umiahmed30/RuTrash/Data/paper/paper5.jpg

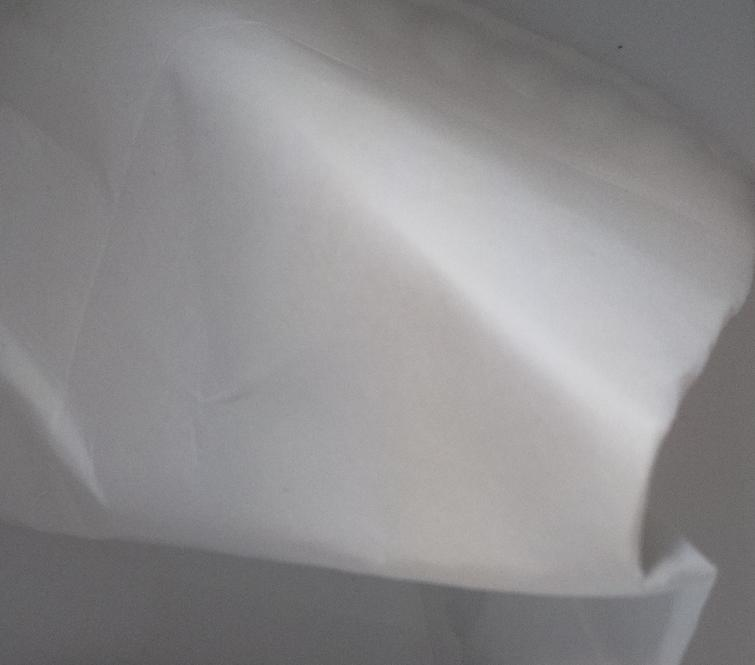
Data/paper/paper5.jpg
