umiahmed30/RuTrash/Data/Valid/paper/paper_new_14.jpg

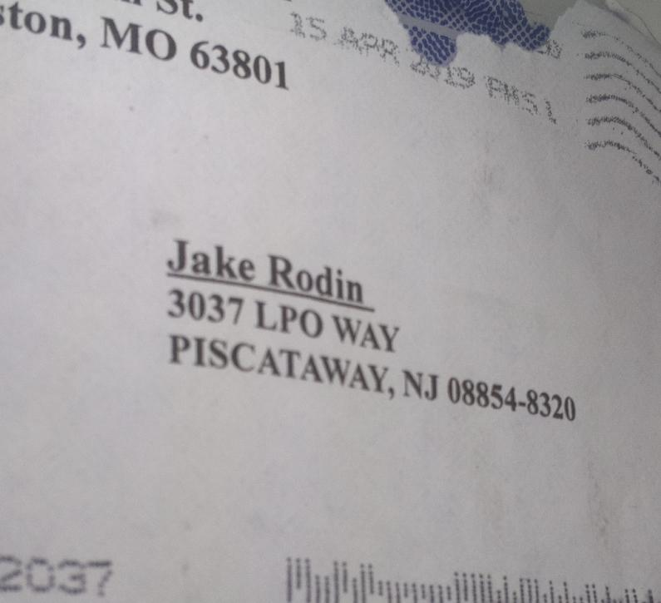
Data/Valid/paper/paper_new_14.jpg
