umiahmed30/RuTrash/Data/glass.jpg

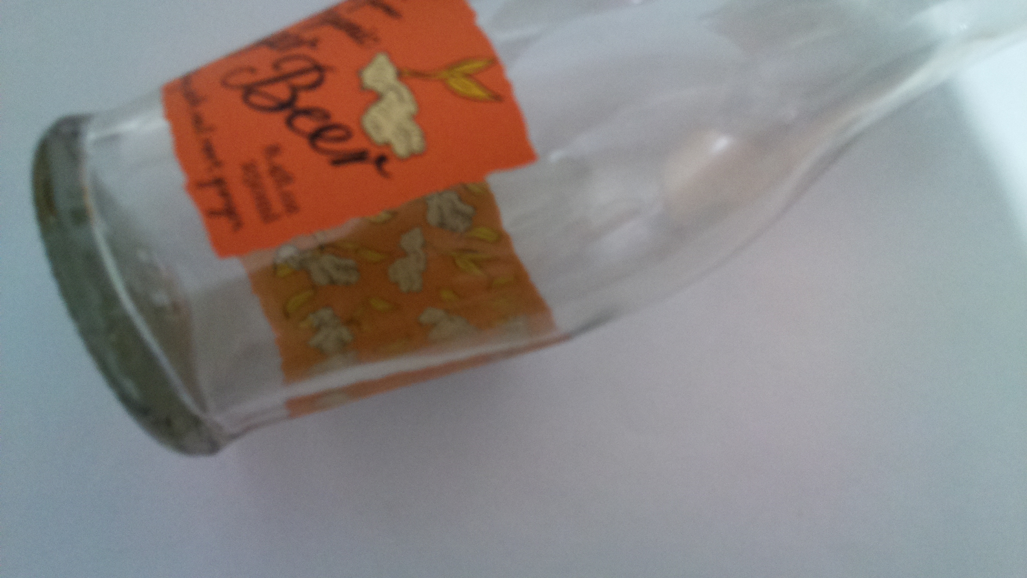
Data/glass.jpg
