umiahmed30/RuTrash/Data/glass/glass1.jpg

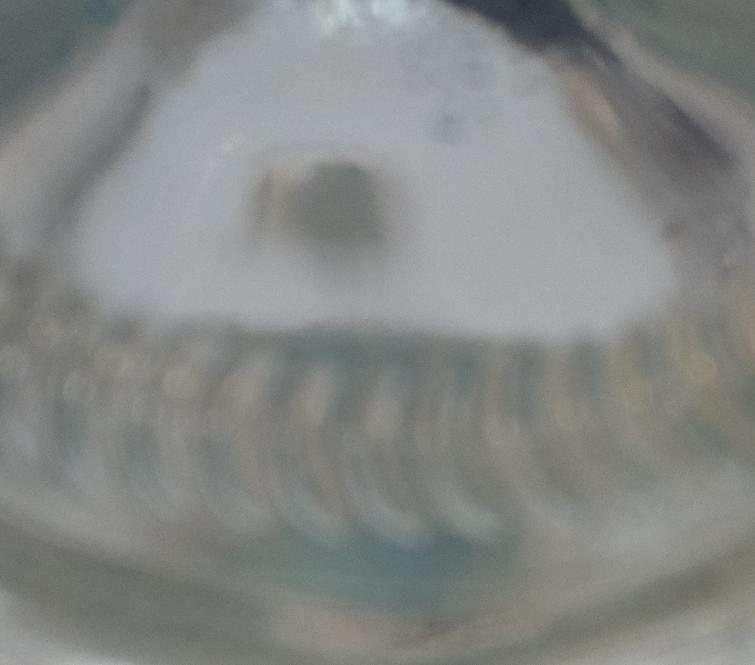
Data/glass/glass1.jpg
