umiahmed30/RuTrash/Data/glass/glass2.jpg

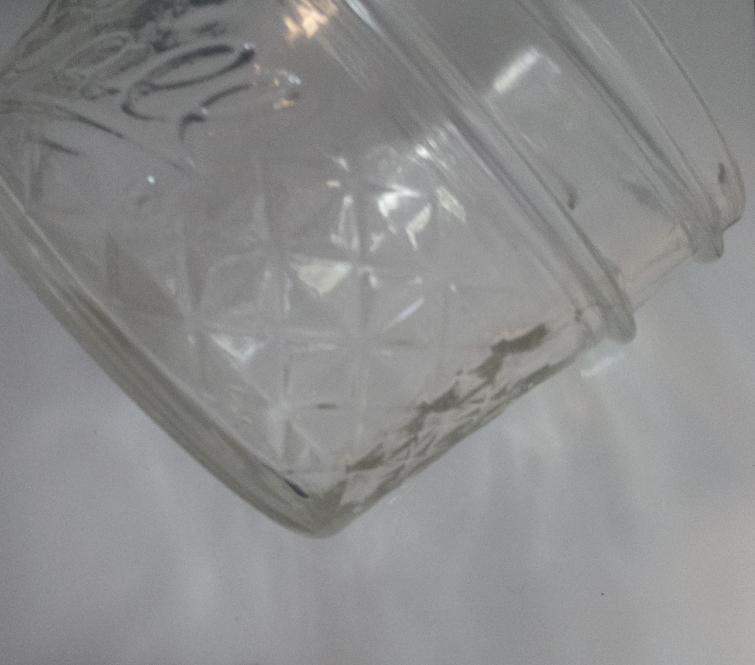
Data/glass/glass2.jpg
