umiahmed30/RuTrash/Data/glass/glass3.jpg

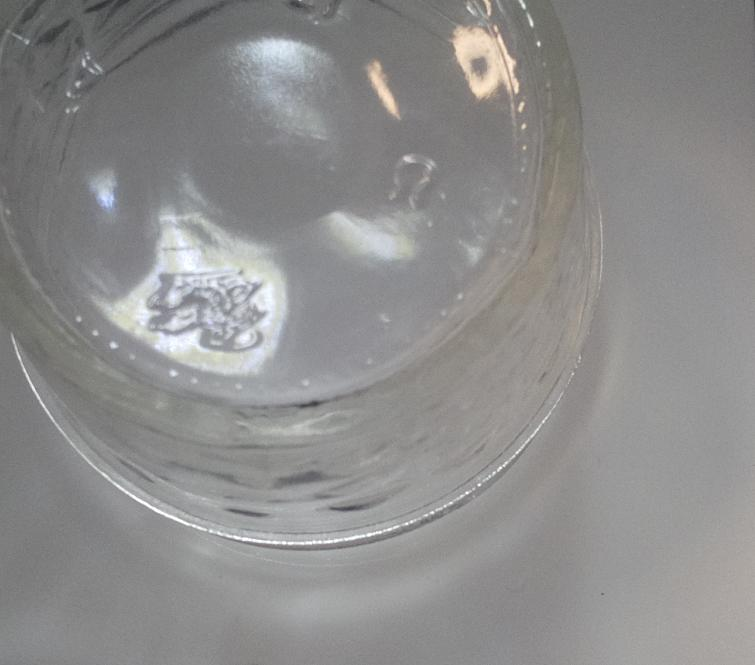
Data/glass/glass3.jpg
