umiahmed30/RuTrash/Data/glass/glass4.jpg

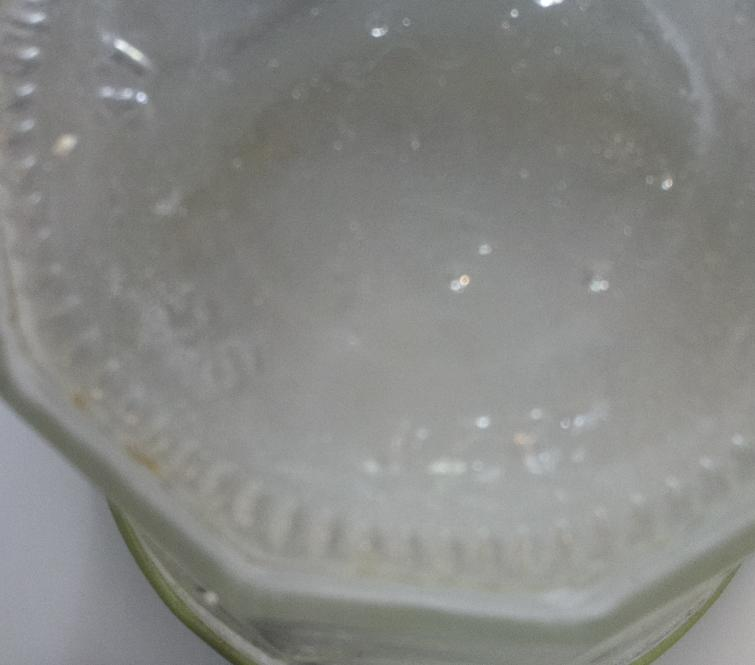
Data/glass/glass4.jpg
