umiahmed30/RuTrash/Data/metal2.jpg

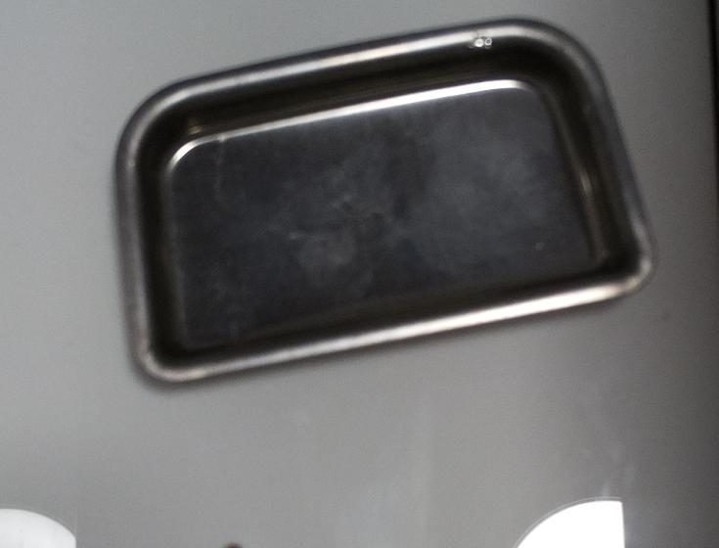
Data/metal2.jpg
