umiahmed30/RuTrash/Data/metal.jpg

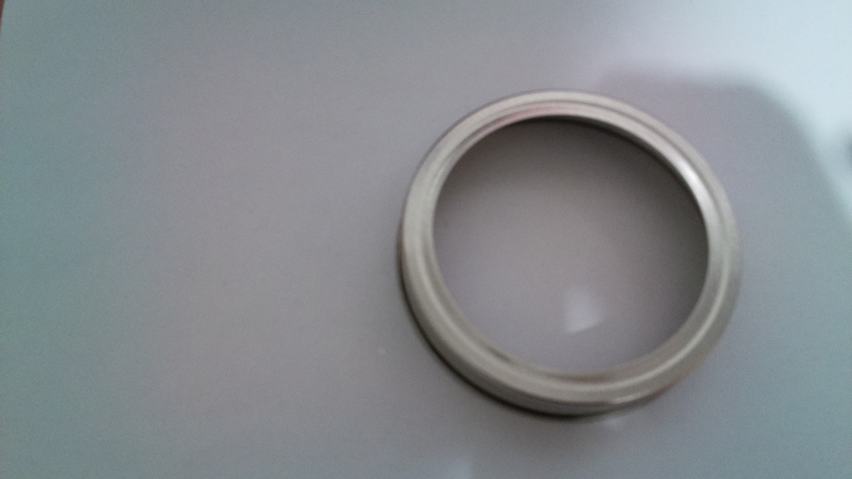
Data/metal.jpg
