umiahmed30/RuTrash/Data/metal/metal0.jpg

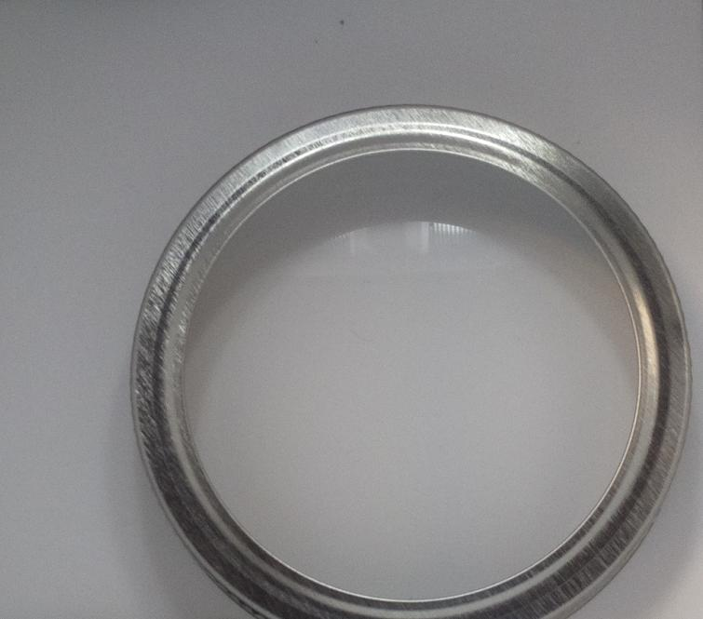
Data/metal/metal0.jpg
