umiahmed30/RuTrash/Data/metal/metal1.jpg

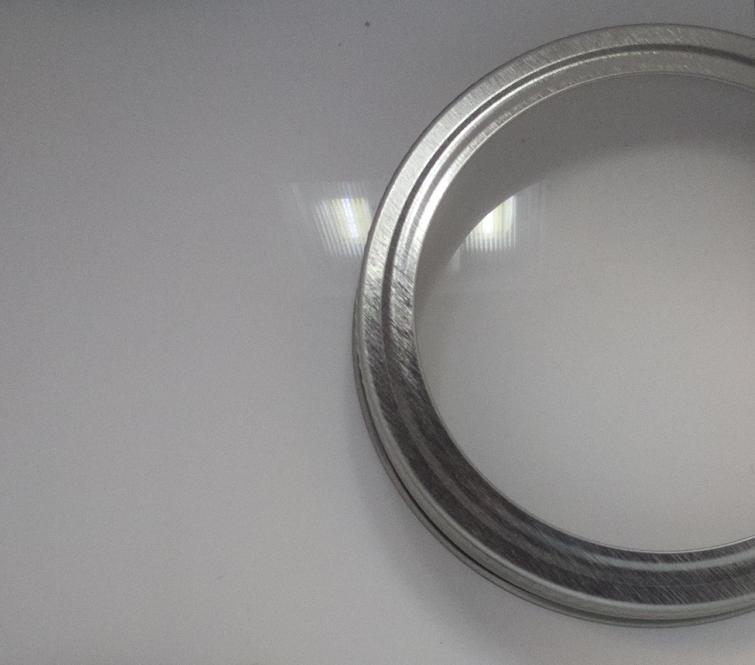
Data/metal/metal1.jpg
