umiahmed30/RuTrash/Data/metal/metal2.jpg

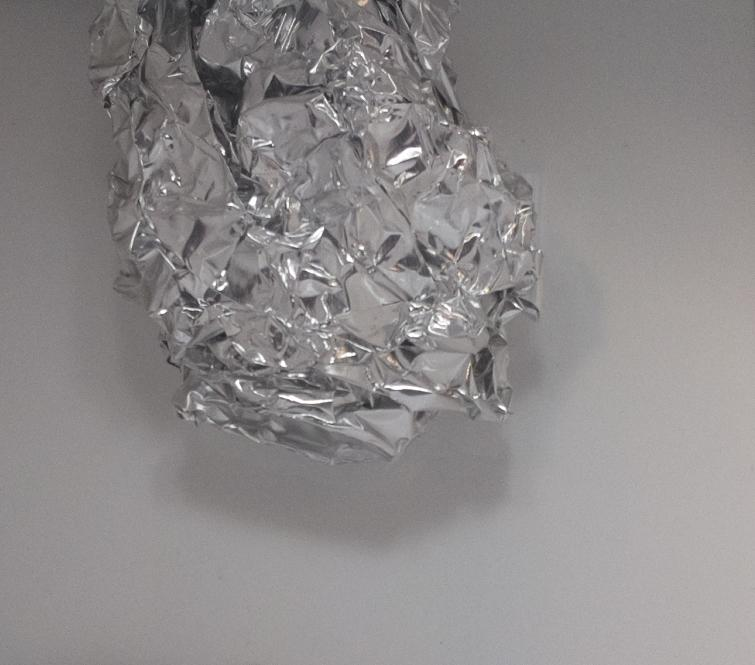
Data/metal/metal2.jpg
