umiahmed30/RuTrash/Data/metal/metal3.jpg

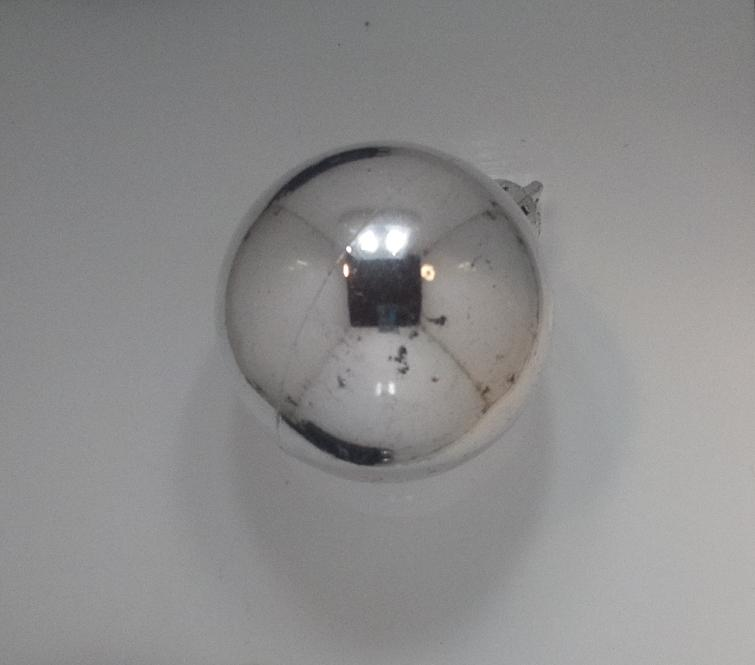
Data/metal/metal3.jpg
