umiahmed30/RuTrash/Data/metal/metal5.jpg

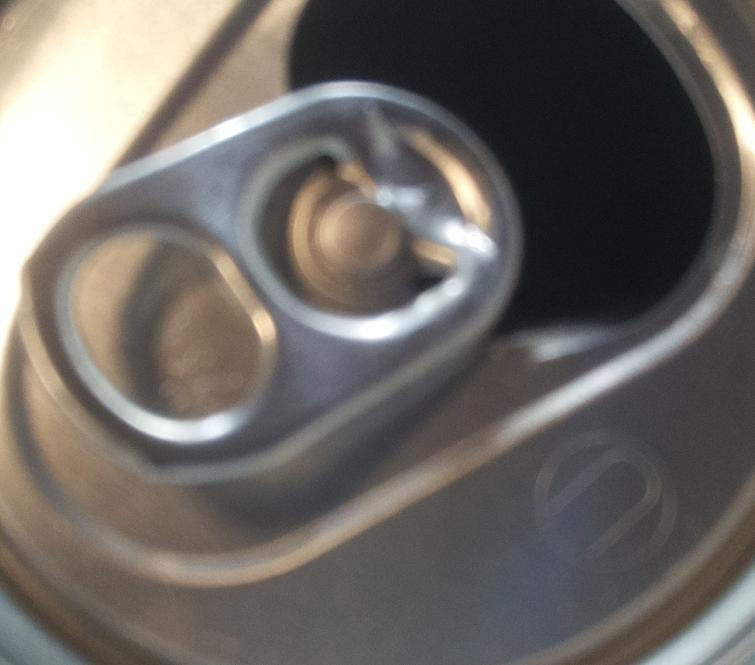
Data/metal/metal5.jpg
