umiahmed30/RuTrash/Data/metal/metal6.jpg

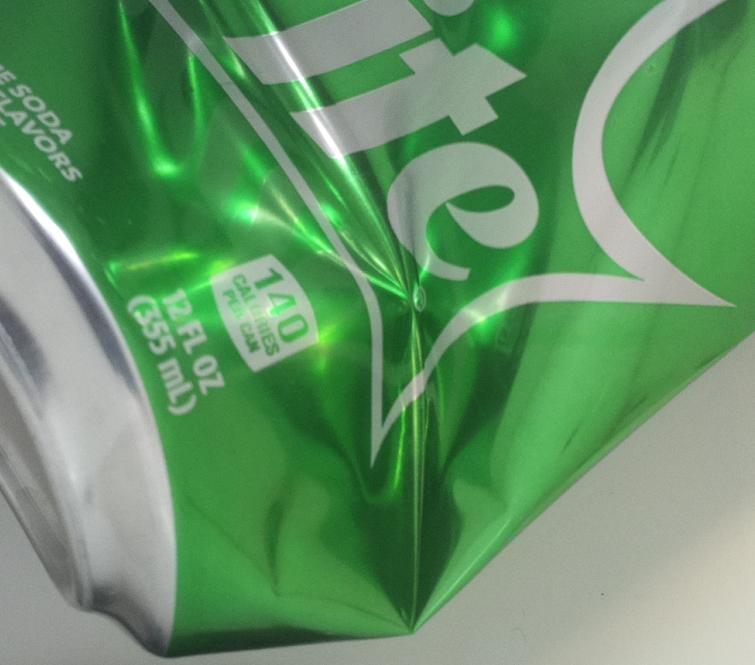
Data/metal/metal6.jpg
