umiahmed30/RuTrash/Data/metal/metal7.jpg

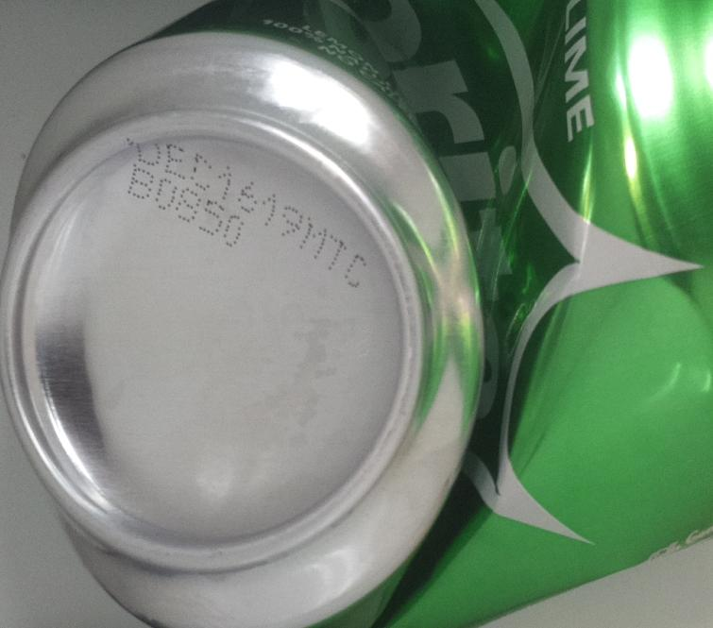
Data/metal/metal7.jpg
