umiahmed30/RuTrash/Data/metal/metal8.jpg

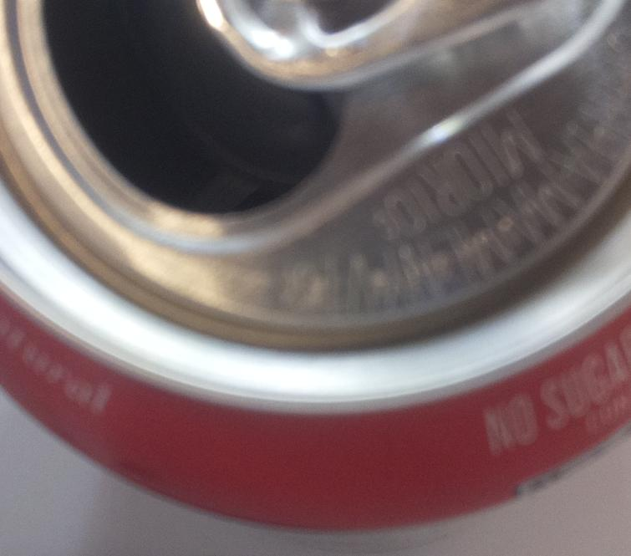
Data/metal/metal8.jpg
