umiahmed30/RuTrash/Data/metal/metal10.jpg

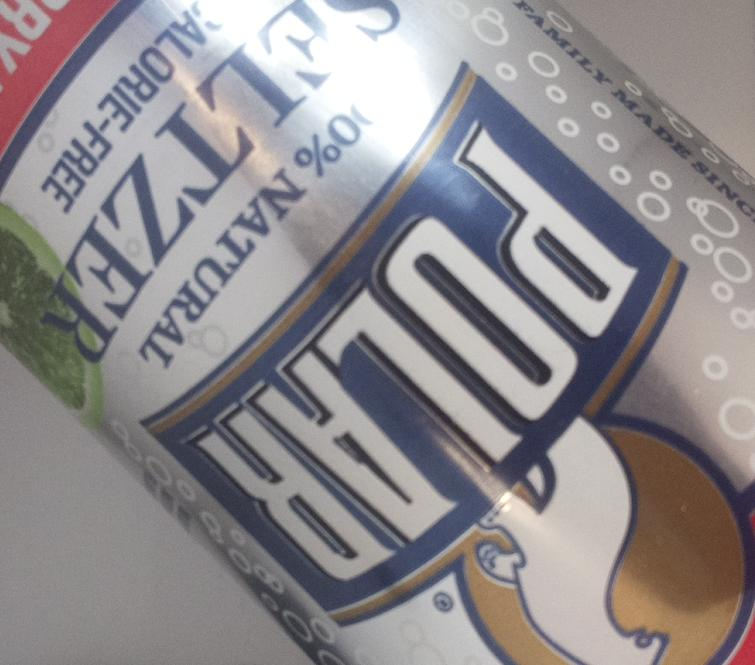
Data/metal/metal10.jpg
