umiahmed30/RuTrash/Data/metal/metal13.jpg

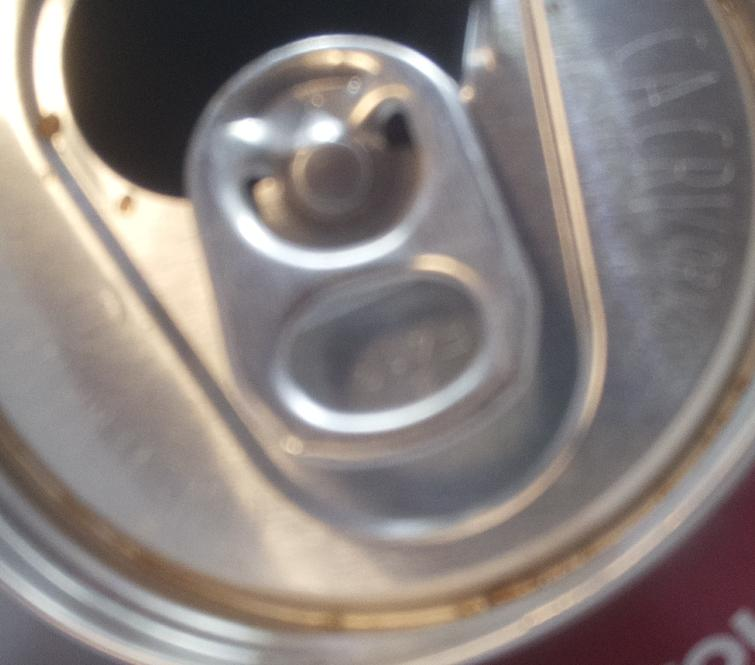
Data/metal/metal13.jpg
