umiahmed30/RuTrash/Data/metal/metal15.jpg

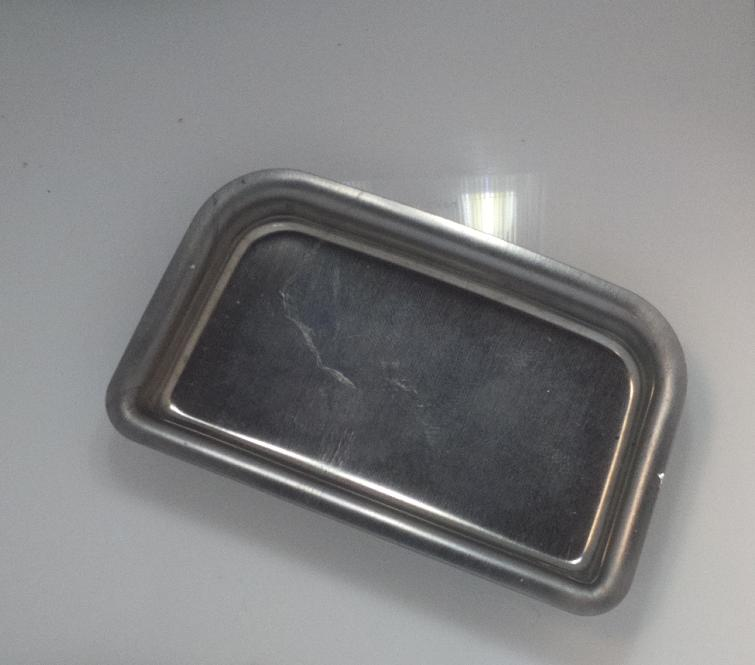
Data/metal/metal15.jpg
