umiahmed30/RuTrash/Data/metal/metal17.jpg

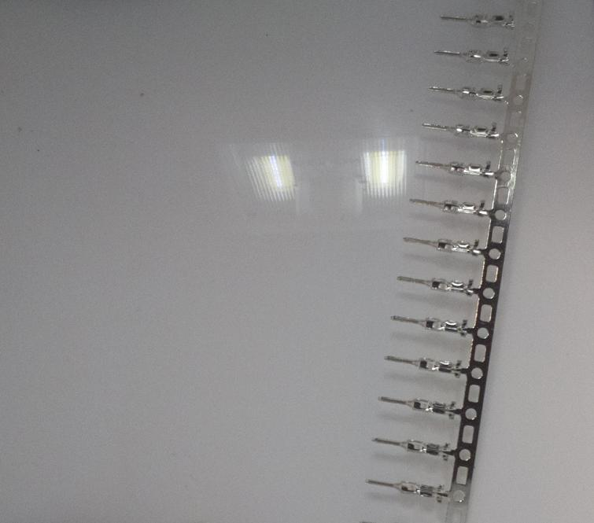
Data/metal/metal17.jpg
