umiahmed30/RuTrash/Data/metal/metal19.jpg

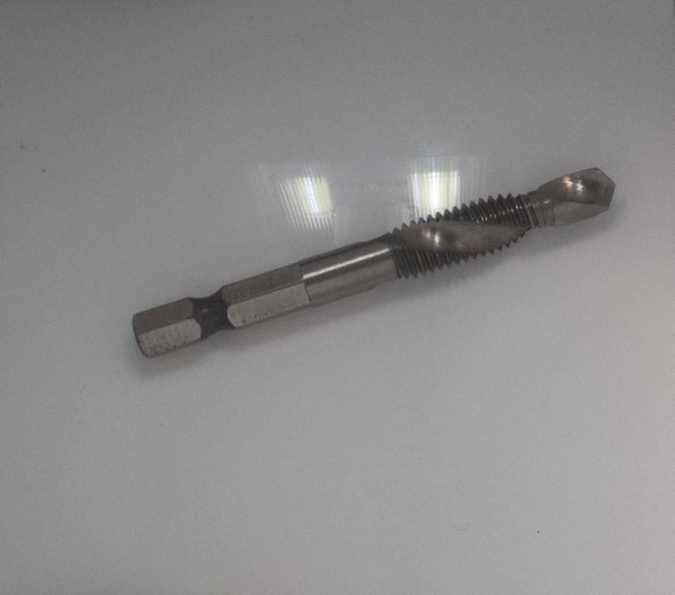
Data/metal/metal19.jpg
