umiahmed30/RuTrash/Data/metal/metal24.jpg

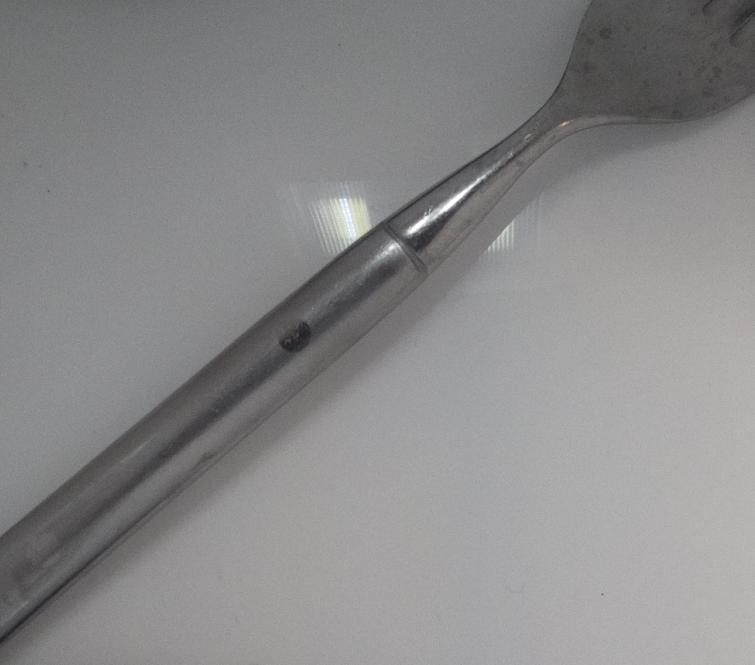
Data/metal/metal24.jpg
