umiahmed30/RuTrash/Data/metal/metal25.jpg

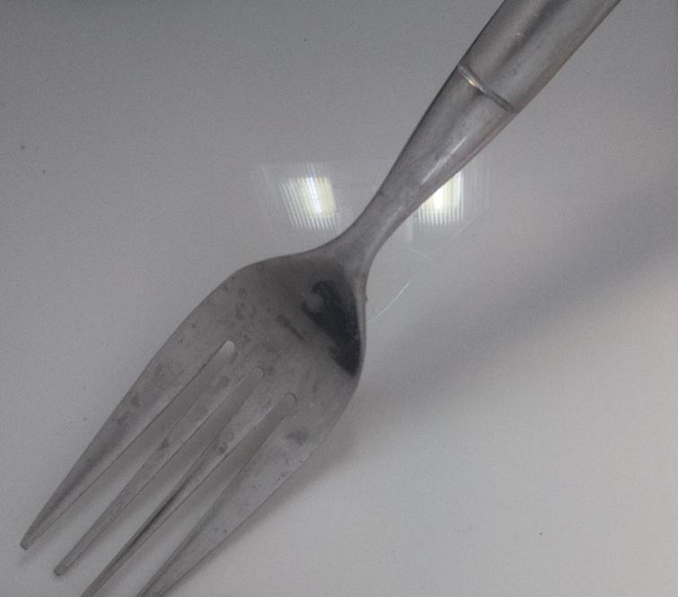
Data/metal/metal25.jpg
