umiahmed30/RuTrash/Data/metal/metal28.jpg

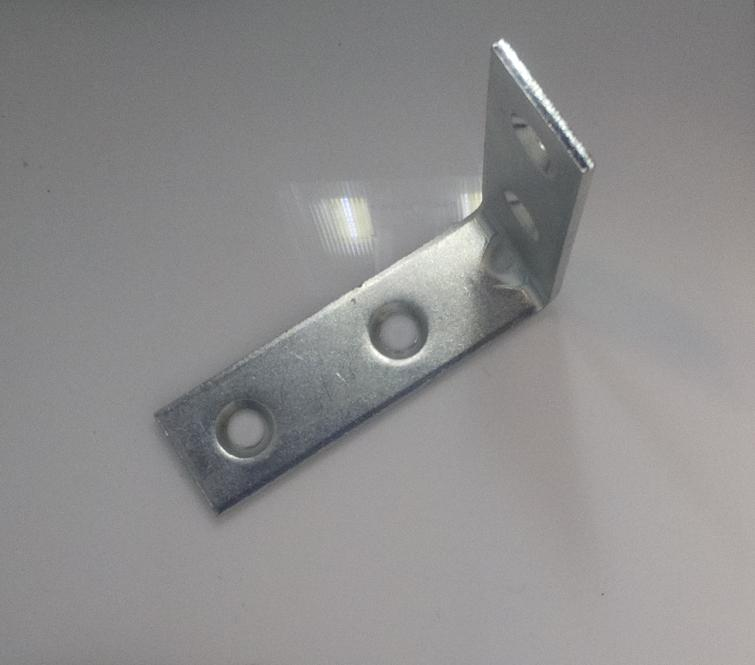
Data/metal/metal28.jpg
