umiahmed30/RuTrash/Data/metal/metal29.jpg

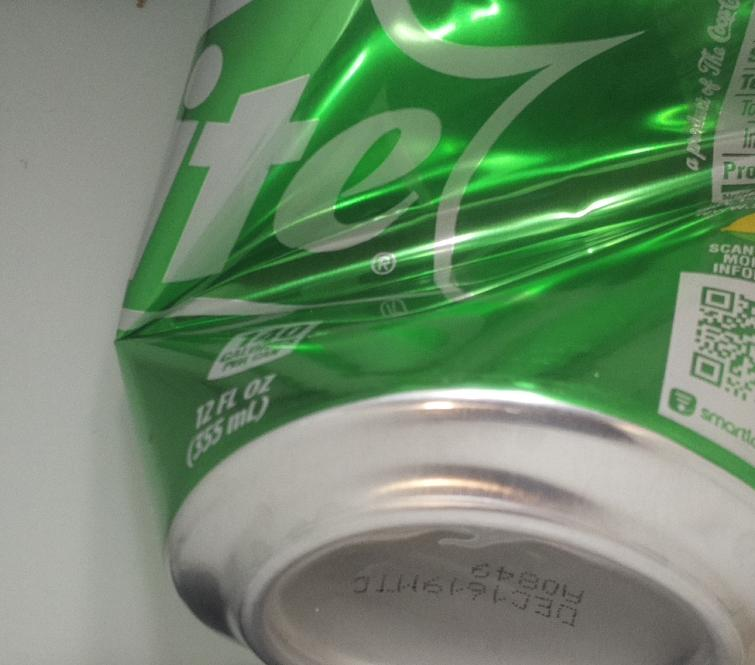
Data/metal/metal29.jpg
