umiahmed30/RuTrash/Data/paper2.jpg

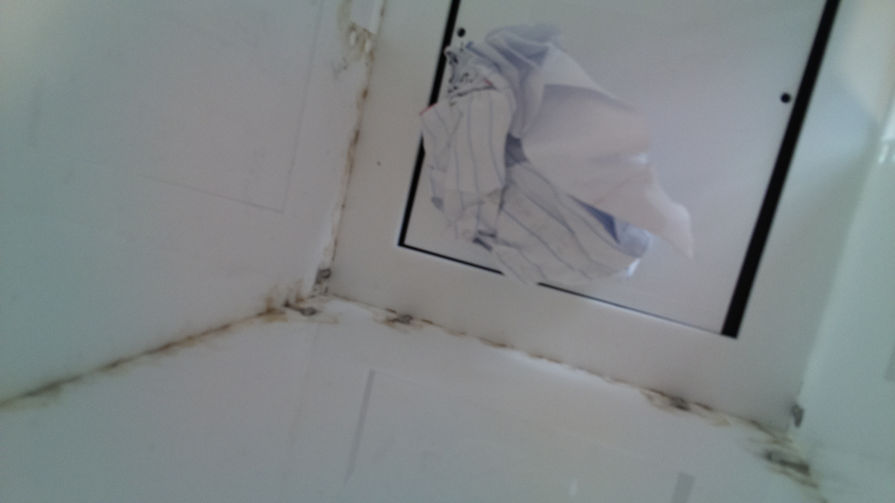
Data/paper2.jpg
