umiahmed30/RuTrash/Data/paper.jpg

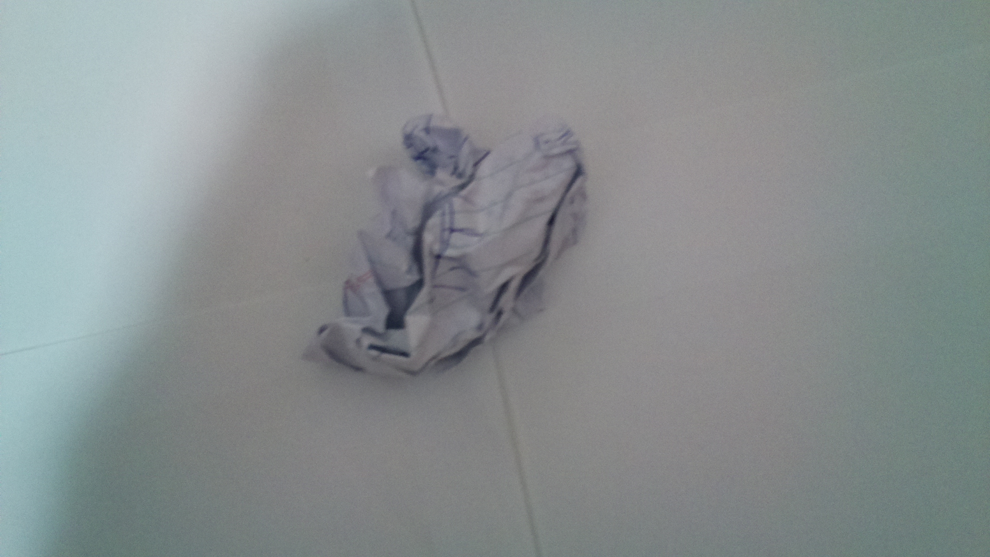
Data/paper.jpg
