umiahmed30/RuTrash/Data/paper/paper1.jpg

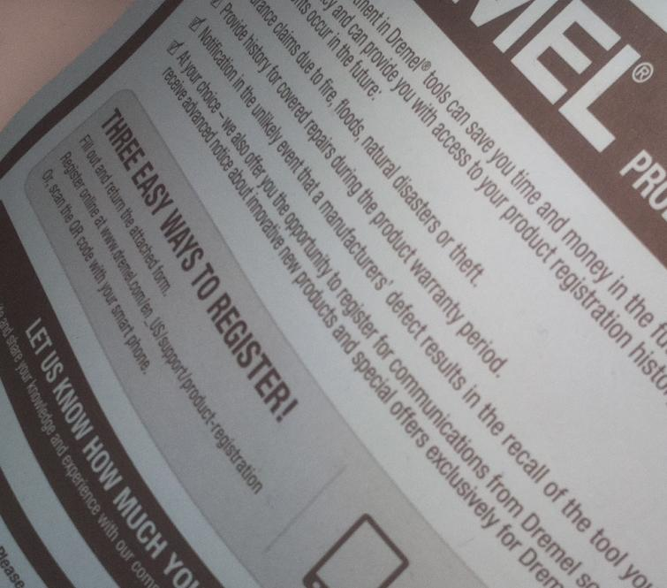
Data/paper/paper1.jpg
