umiahmed30/RuTrash/Data/paper/paper2.jpg

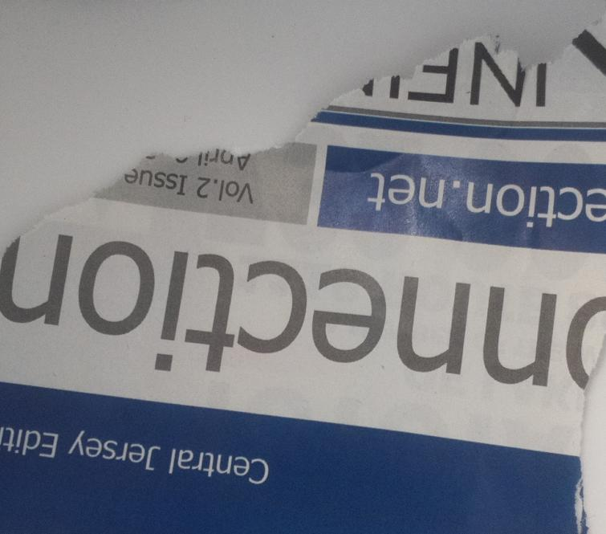
Data/paper/paper2.jpg
