umiahmed30/RuTrash/Data/paper/paper3.jpg

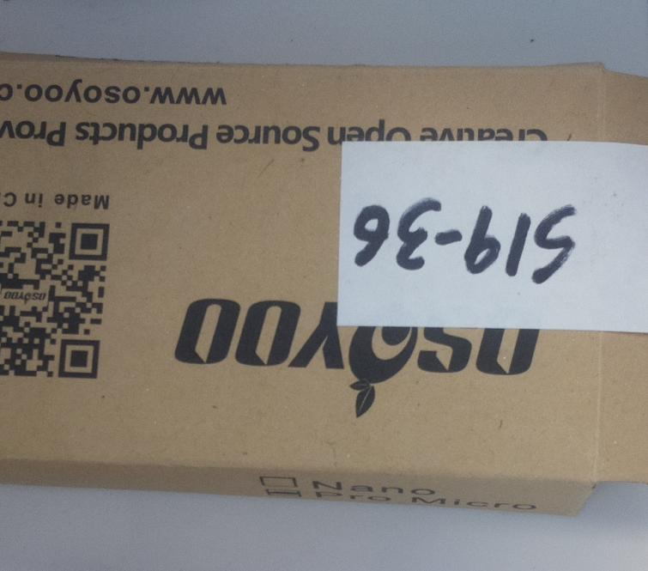
Data/paper/paper3.jpg
