umiahmed30/RuTrash/Data/paper/paper6.jpg

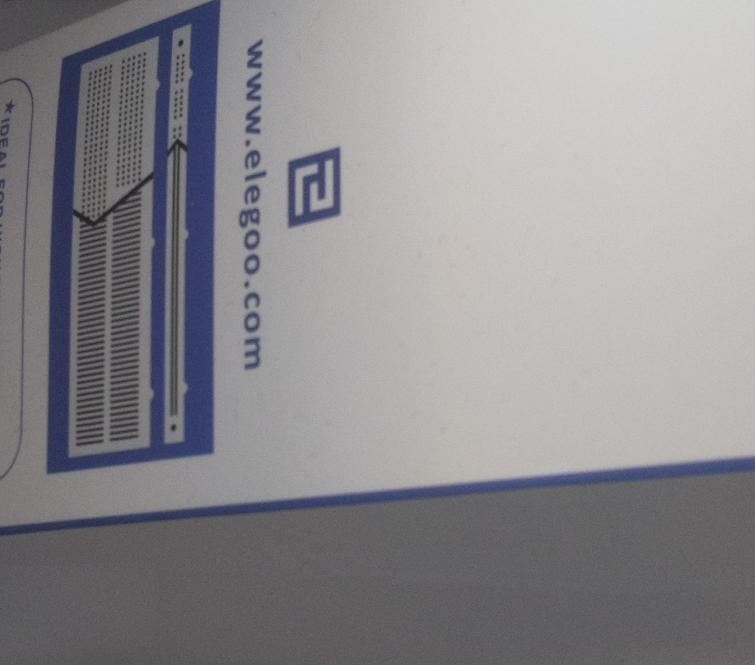
Data/paper/paper6.jpg
