umiahmed30/RuTrash/Data/paper/paper9.jpg

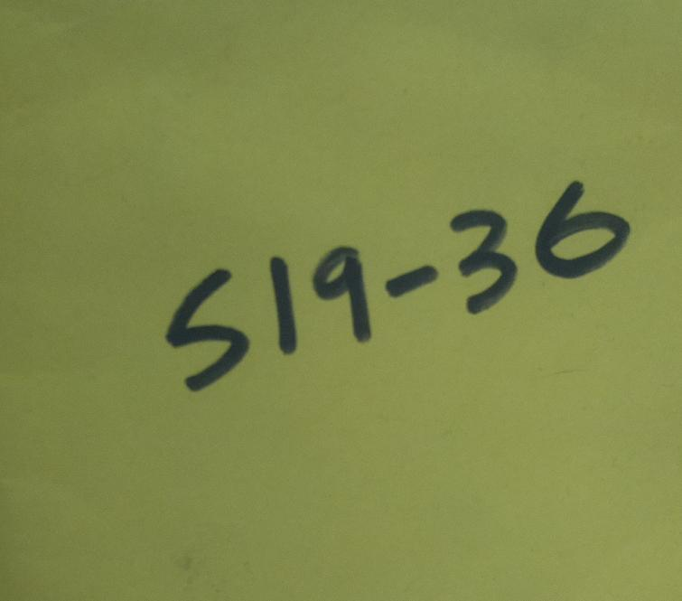
Data/paper/paper9.jpg
