umiahmed30/RuTrash/Data/paper/paper10.jpg

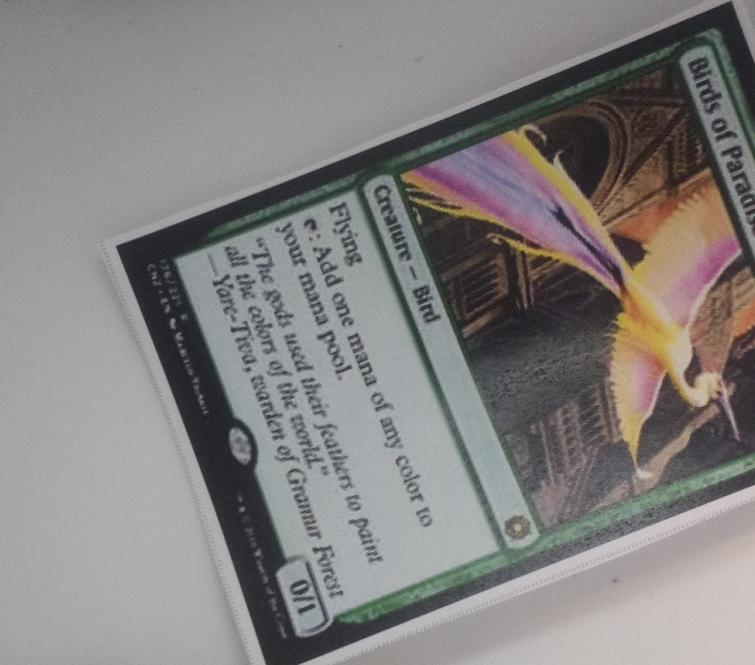
Data/paper/paper10.jpg
