umiahmed30/RuTrash/Data/paper/paper11.jpg

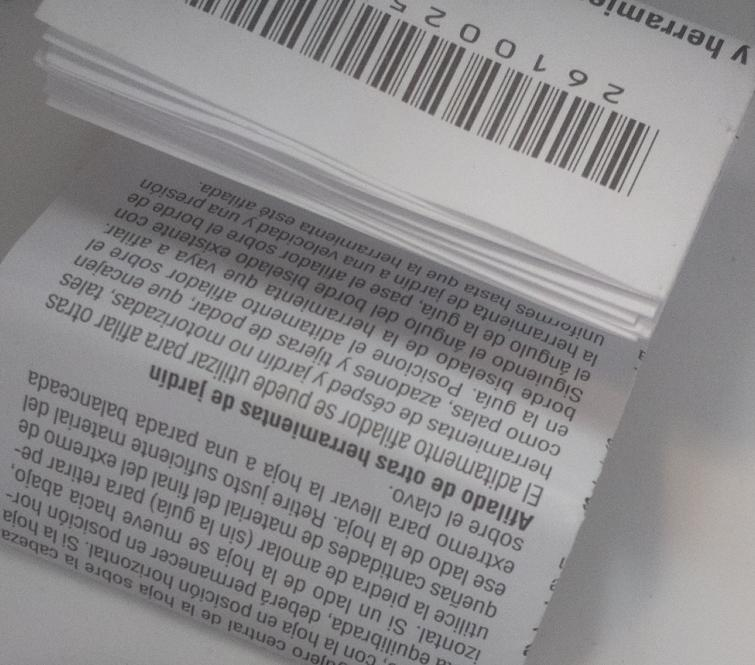
Data/paper/paper11.jpg
