umiahmed30/RuTrash/Data/paper/paper13.jpg

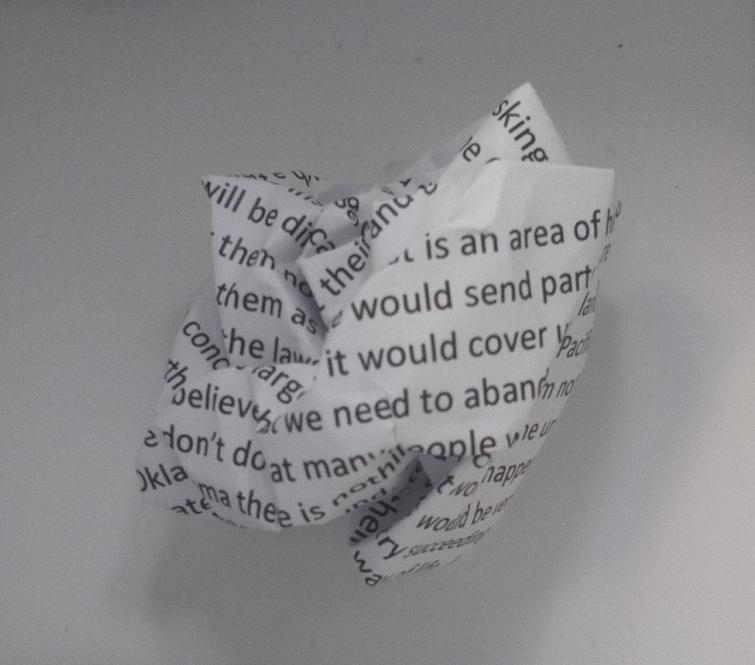
Data/paper/paper13.jpg
