umiahmed30/RuTrash/Data/paper/paper14.jpg

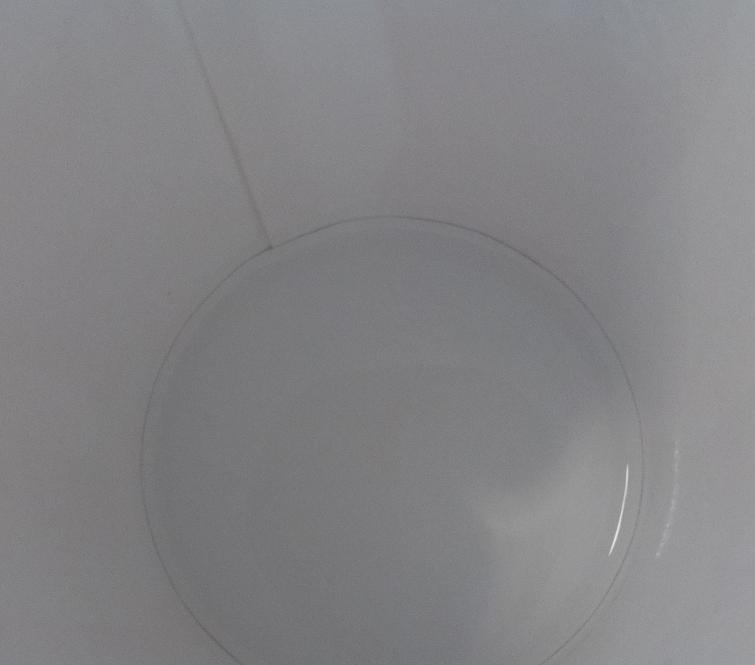
Data/paper/paper14.jpg
