umiahmed30/RuTrash/Data/paper/paper19.jpg

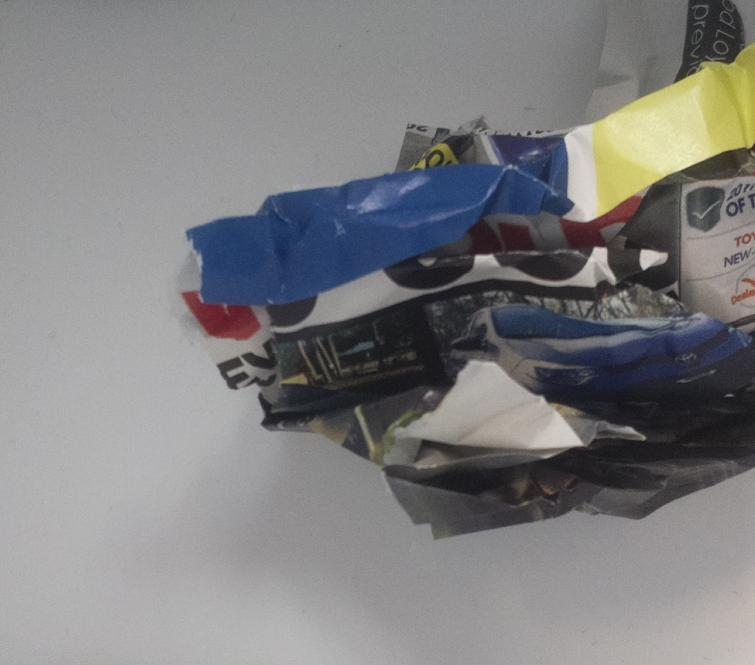
Data/paper/paper19.jpg
