umiahmed30/RuTrash/Data/paper/paper20.jpg

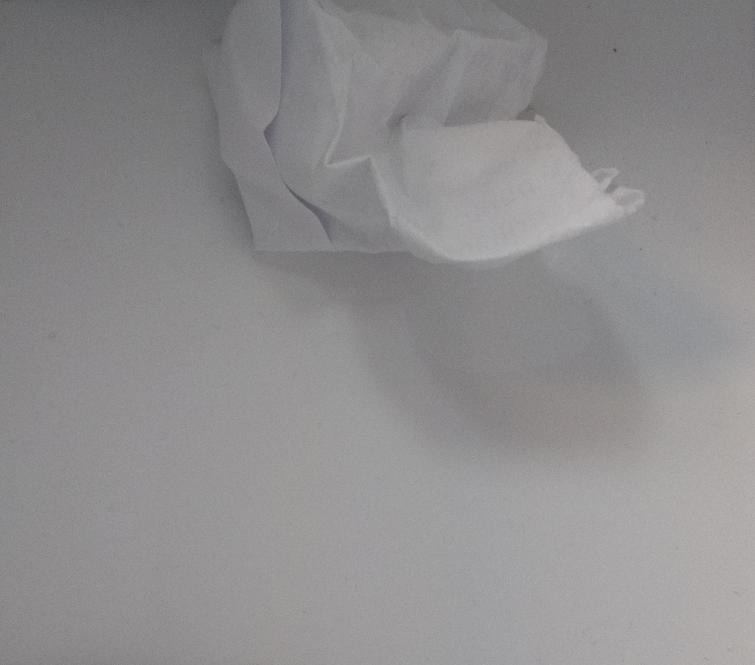
Data/paper/paper20.jpg
