umiahmed30/RuTrash/Data/paper/paper23.jpg

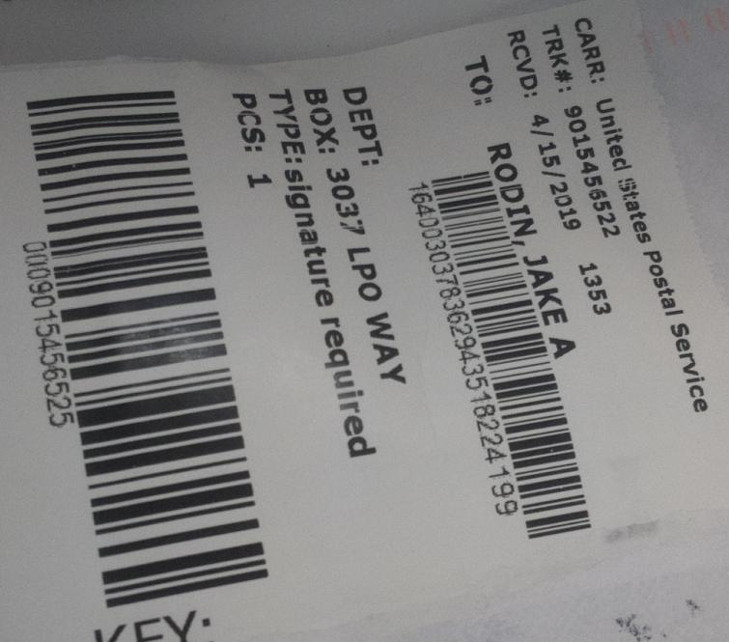
Data/paper/paper23.jpg
