umiahmed30/RuTrash/Data/paper/paper27.jpg

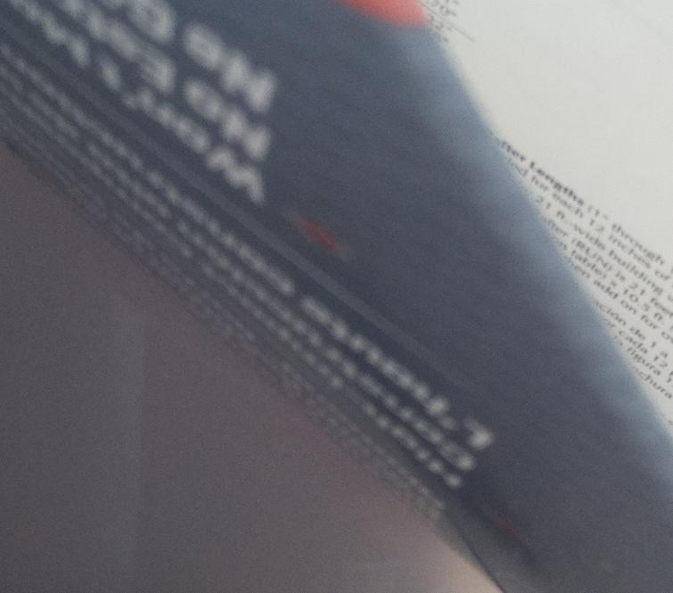
Data/paper/paper27.jpg
