umiahmed30/RuTrash/Data/paper/paper28.jpg

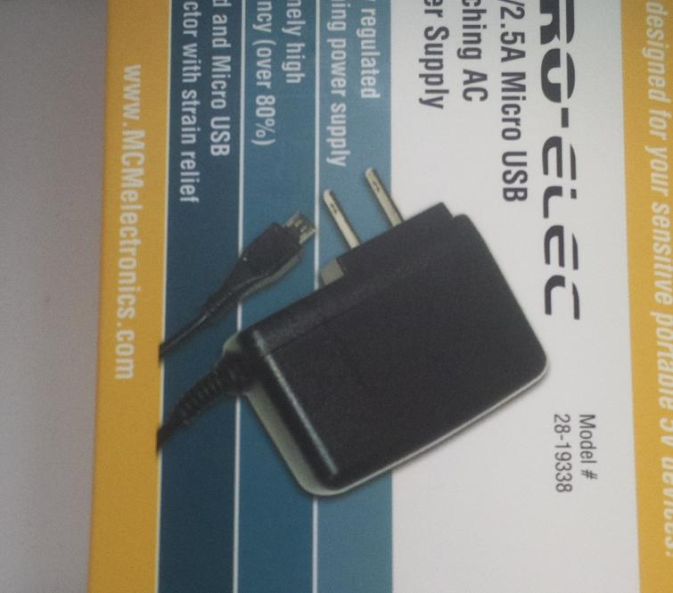
Data/paper/paper28.jpg
