umiahmed30/RuTrash/Data/paper/paper30.jpg

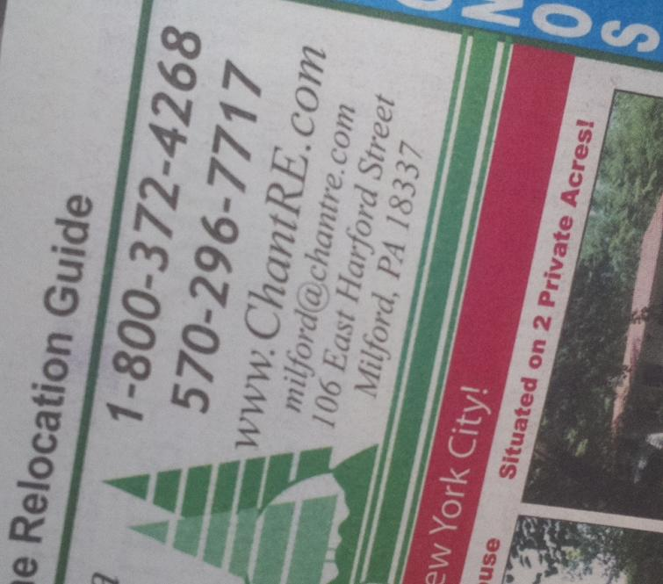
Data/paper/paper30.jpg
