umiahmed30/RuTrash/Data/plastic.jpg

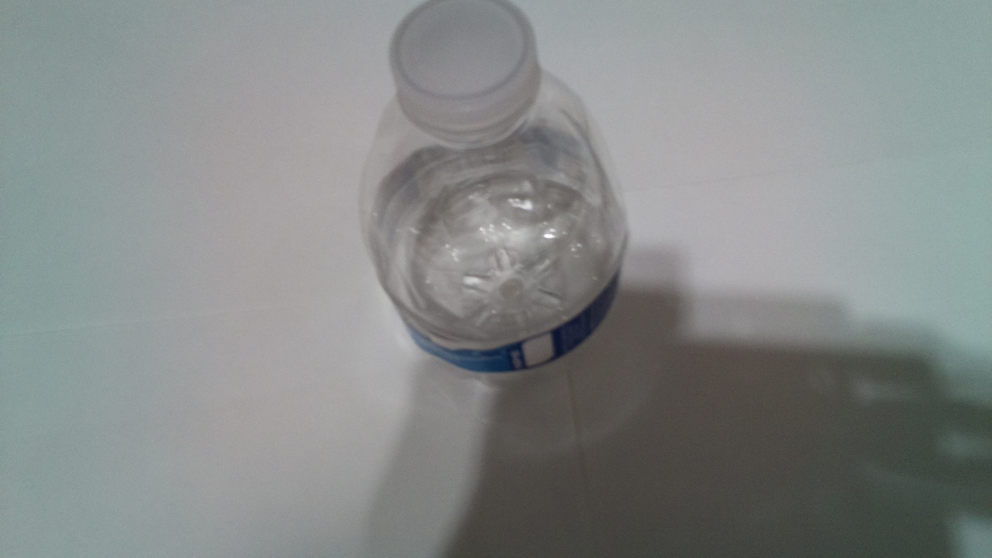
Data/plastic.jpg
