umiahmed30/RuTrash/Data/plastic/plastic1.jpg

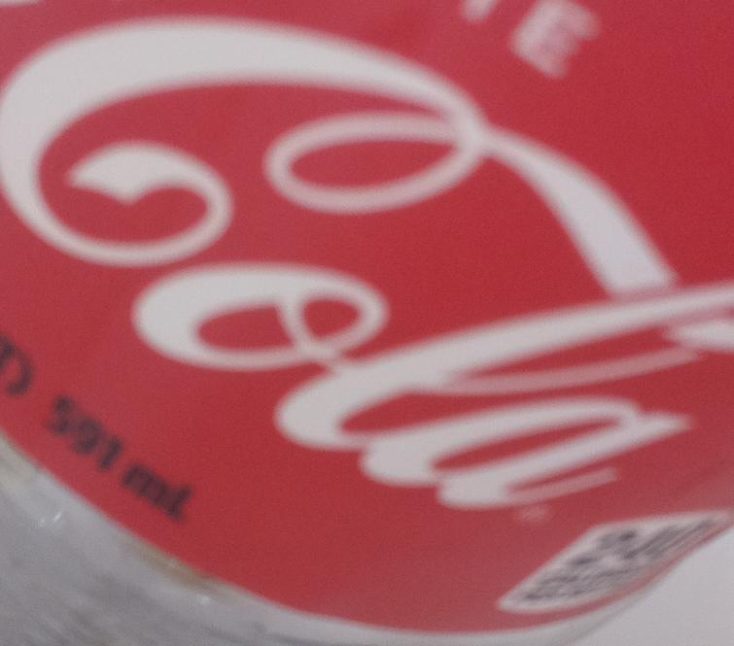
Data/plastic/plastic1.jpg
