umiahmed30/RuTrash/Data/plastic/plastic2.jpg

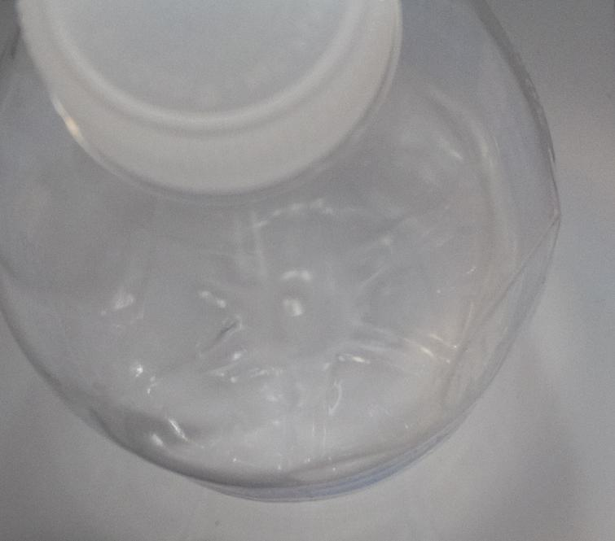
Data/plastic/plastic2.jpg
