umiahmed30/RuTrash/Data/plastic/plastic3.jpg

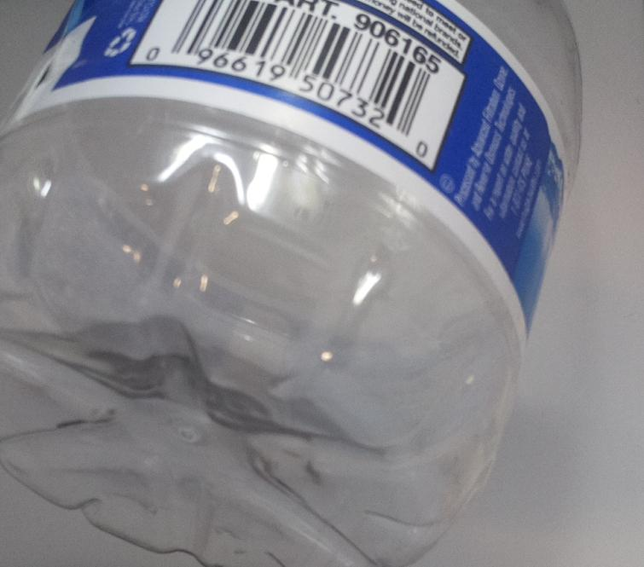
Data/plastic/plastic3.jpg
