umiahmed30/RuTrash/Data/plastic/plastic4.jpg

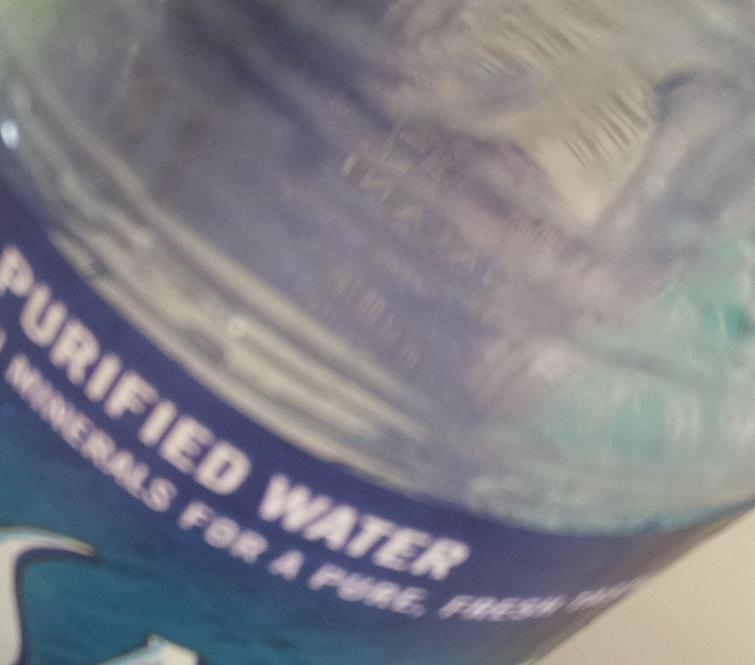
Data/plastic/plastic4.jpg
