umiahmed30/RuTrash/Data/plastic/plastic5.jpg

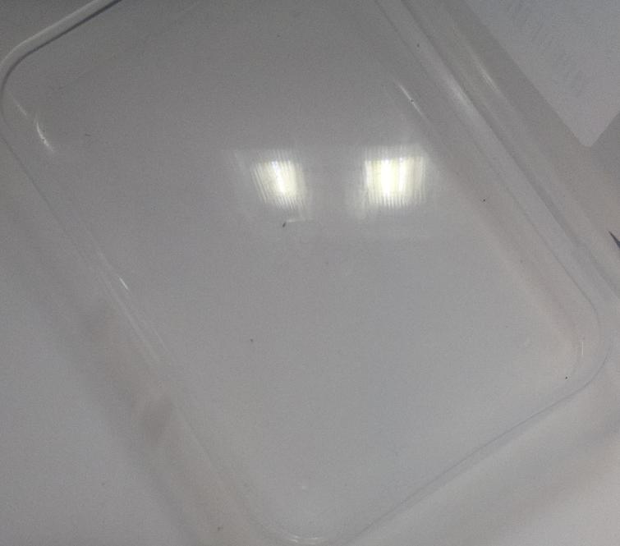
Data/plastic/plastic5.jpg
