umiahmed30/RuTrash/Data/plastic/plastic6.jpg

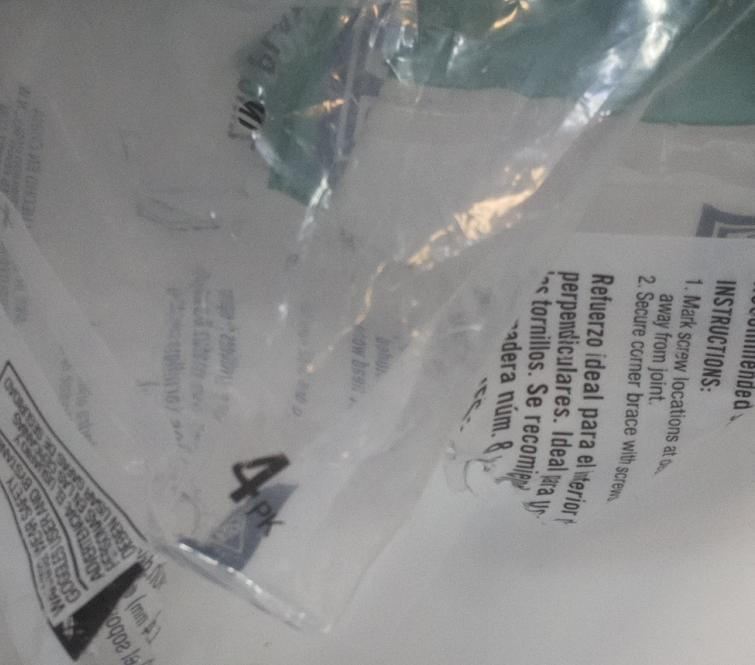
Data/plastic/plastic6.jpg
