umiahmed30/RuTrash/Data/plastic/plastic12.jpg

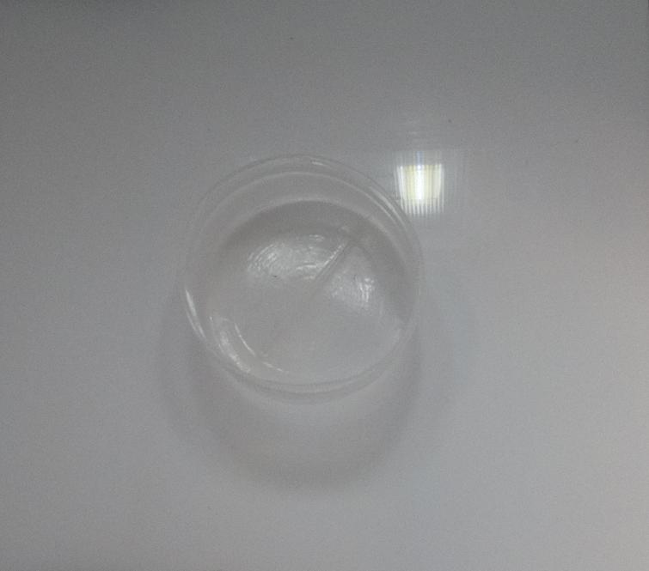
Data/plastic/plastic12.jpg
