umiahmed30/RuTrash/Data/plastic/plastic13.jpg

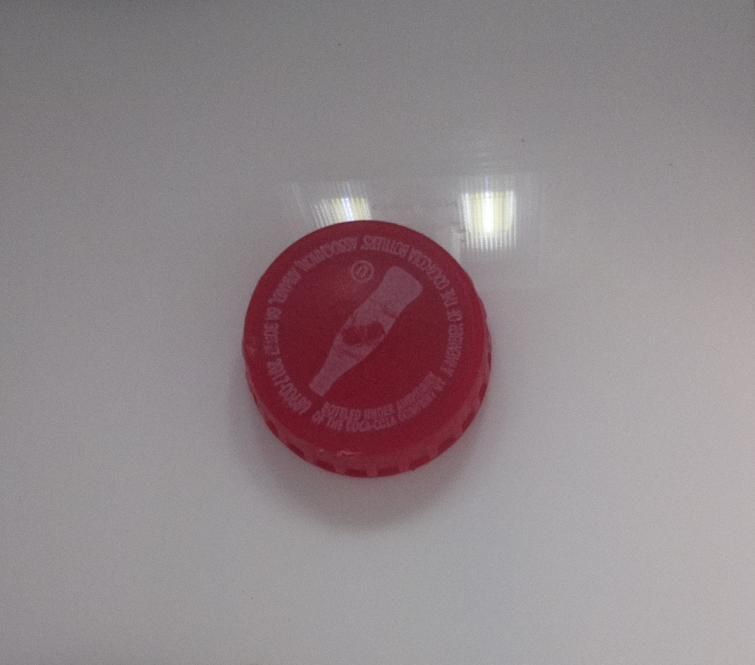
Data/plastic/plastic13.jpg
