umiahmed30/RuTrash/Data/plastic/plastic14.jpg

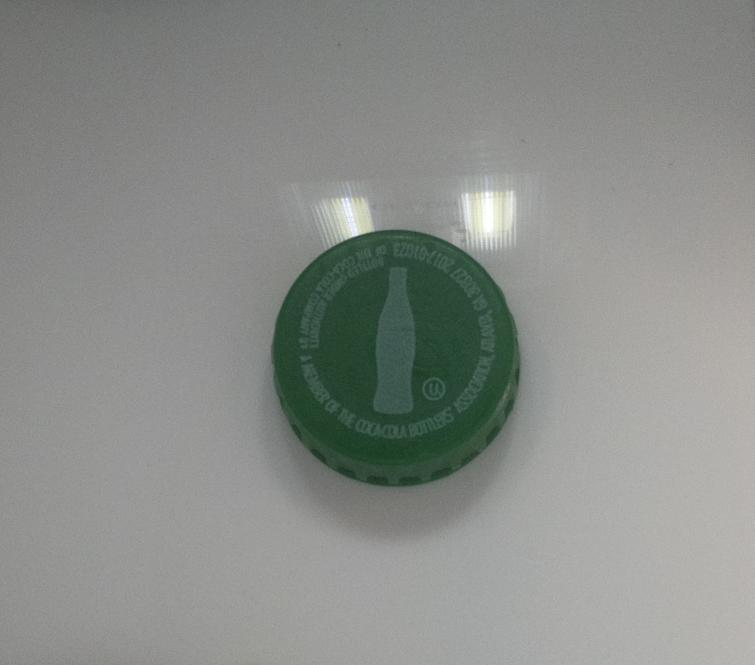
Data/plastic/plastic14.jpg
