umiahmed30/RuTrash/Data/plastic/plastic15.jpg

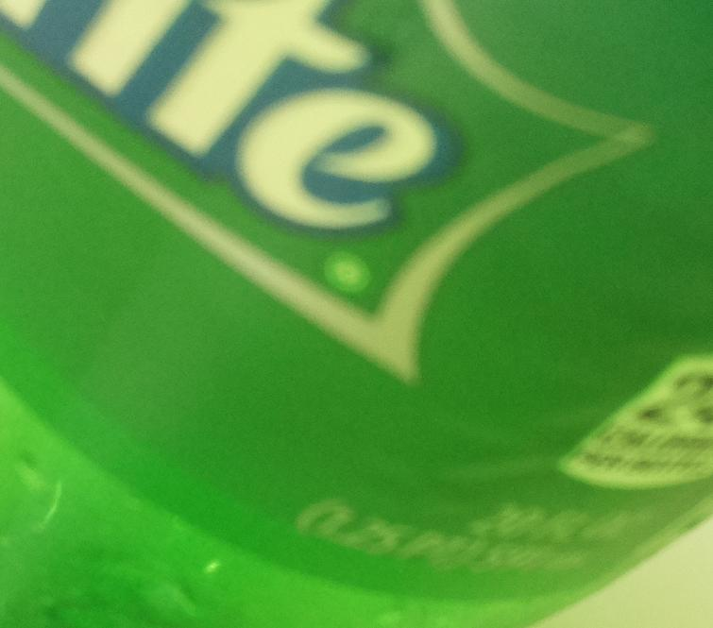
Data/plastic/plastic15.jpg
