umiahmed30/RuTrash/Data/plastic/plastic18.jpg

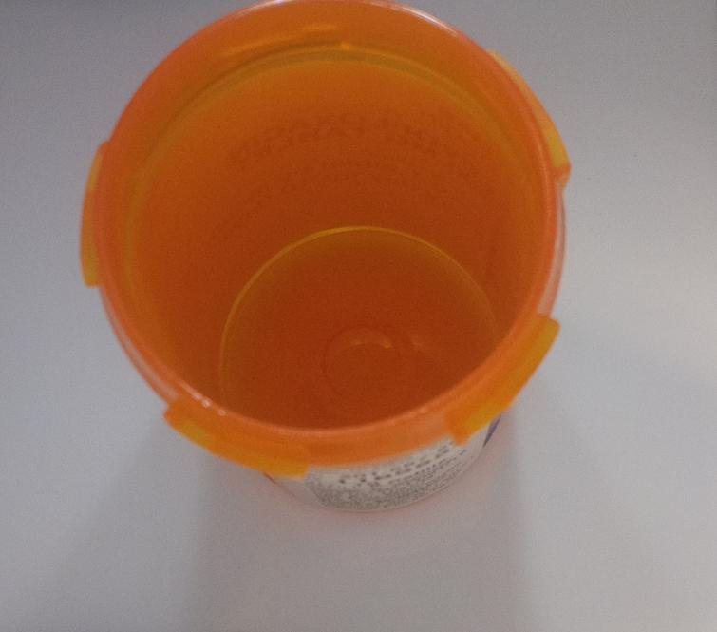
Data/plastic/plastic18.jpg
