umiahmed30/RuTrash/Data/plastic/plastic19.jpg

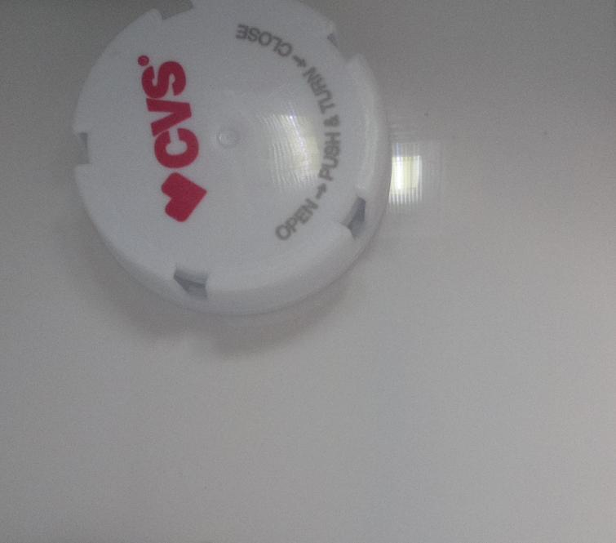
Data/plastic/plastic19.jpg
