umiahmed30/RuTrash/Data/plastic/plastic21.jpg

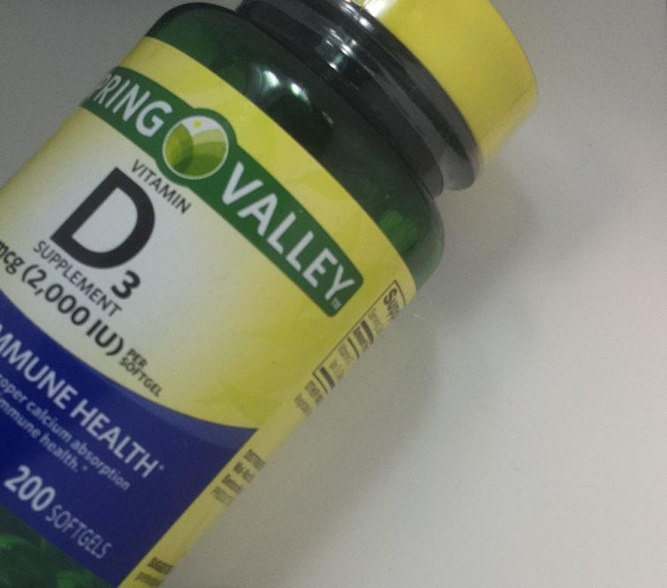
Data/plastic/plastic21.jpg
