umiahmed30/RuTrash/Data/plastic/plastic24.jpg

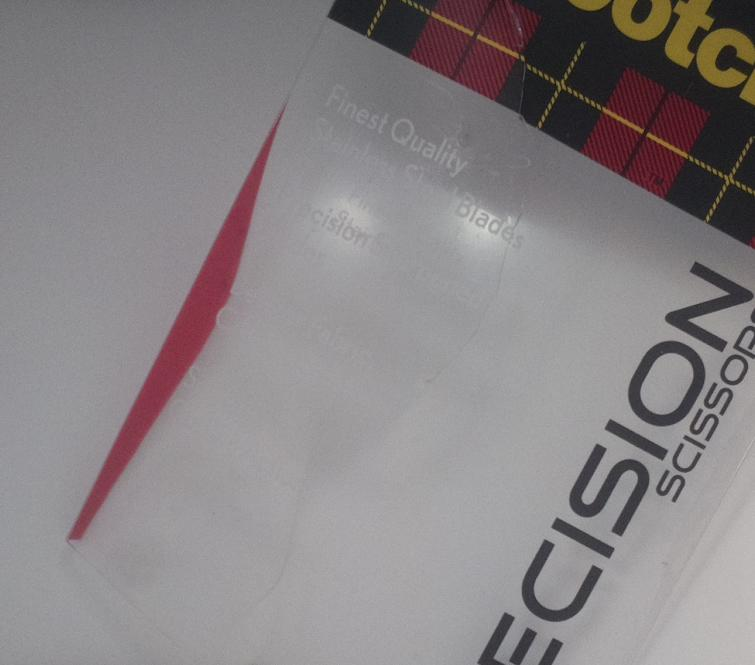
Data/plastic/plastic24.jpg
