umiahmed30/RuTrash/Data/plastic/plastic25.jpg

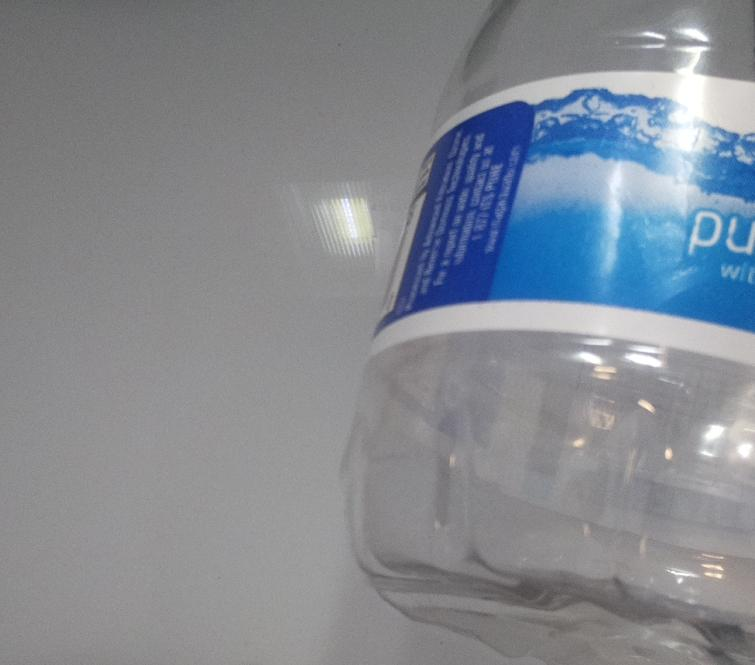
Data/plastic/plastic25.jpg
