umiahmed30/RuTrash/Data/plastic/plastic26.jpg

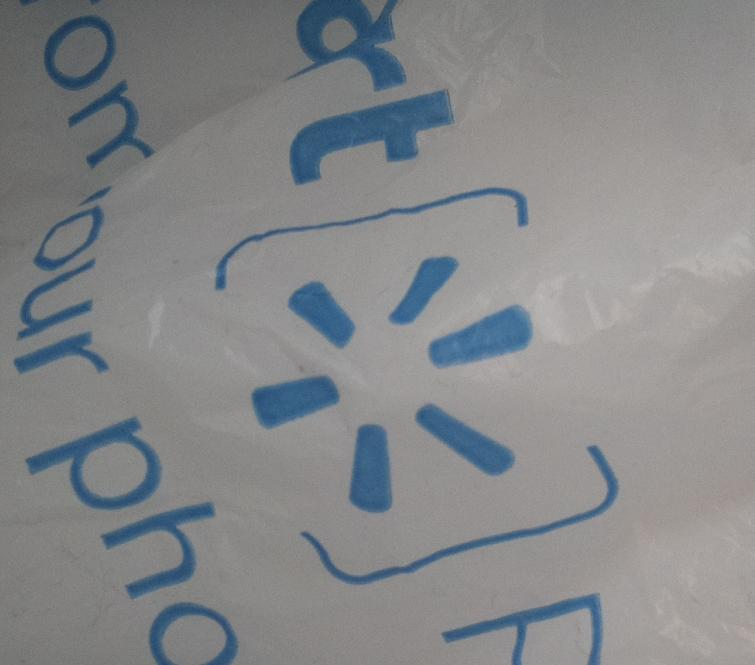
Data/plastic/plastic26.jpg
