umiahmed30/RuTrash/Data/plastic/plastic27.jpg

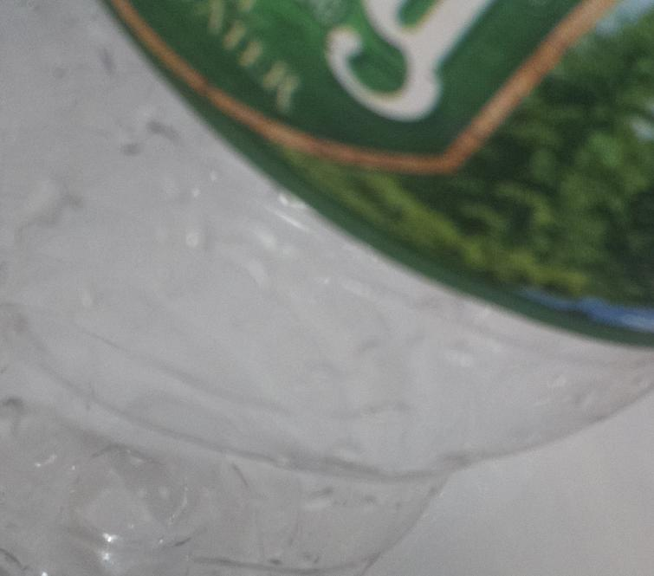
Data/plastic/plastic27.jpg
