umiahmed30/RuTrash/Data/plastic/plastic30.jpg

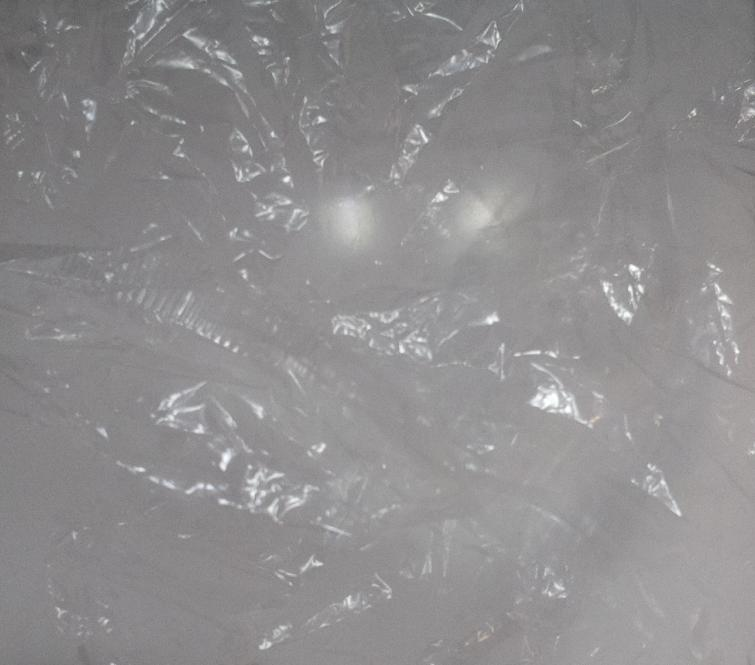
Data/plastic/plastic30.jpg
