umiahmed30/RuTrash/Data/trash.jpg

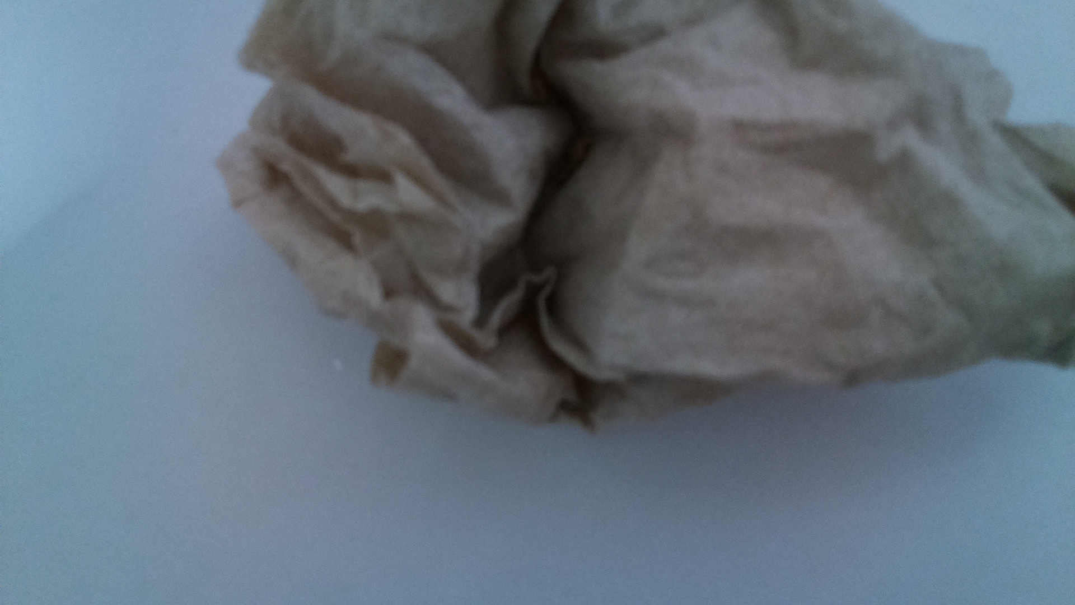
Data/trash.jpg
