umiahmed30/RuTrash/Data/trash/trash26.jpg

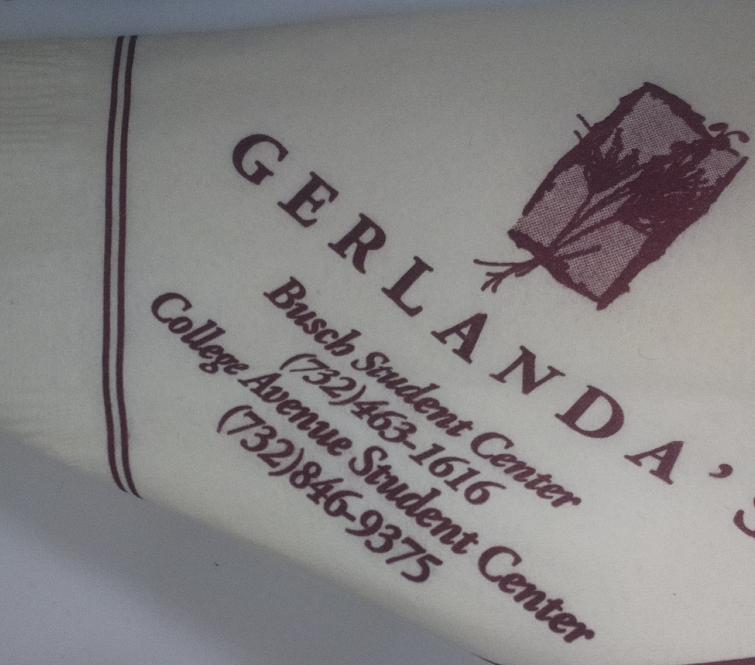
Data/trash/trash26.jpg
