umiahmed30/RuTrash/Data/trash/trash28.jpg

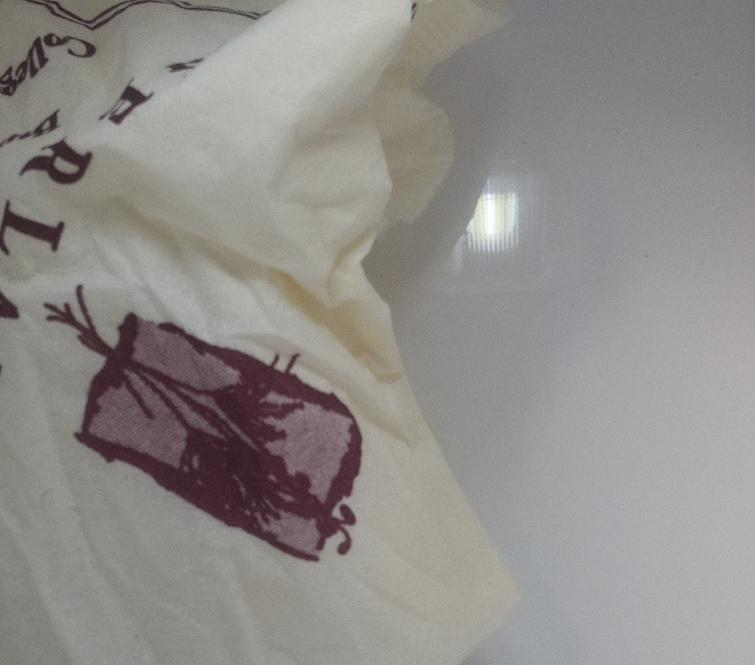
Data/trash/trash28.jpg
