umiahmed30/RuTrash/Data/trash/trash29.jpg

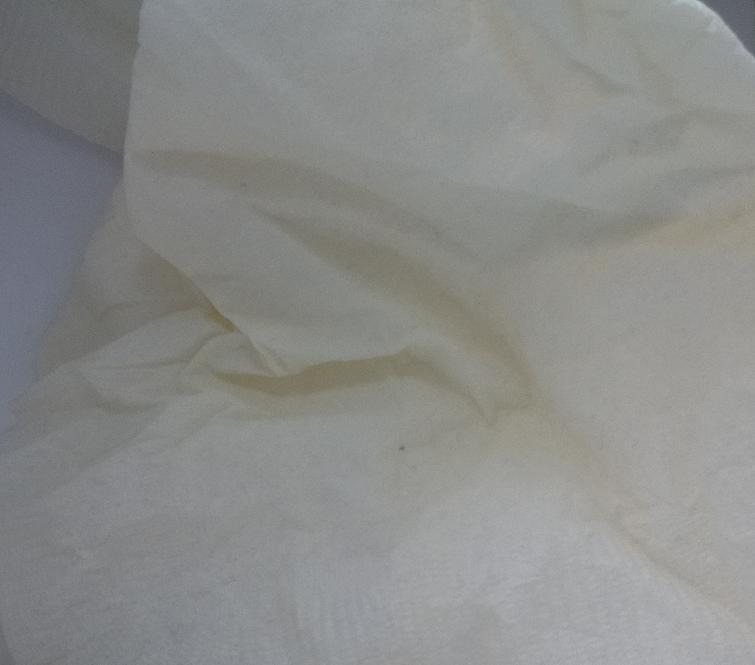
Data/trash/trash29.jpg
