umiahmed30/RuTrash/Data/trash/trash31.jpg

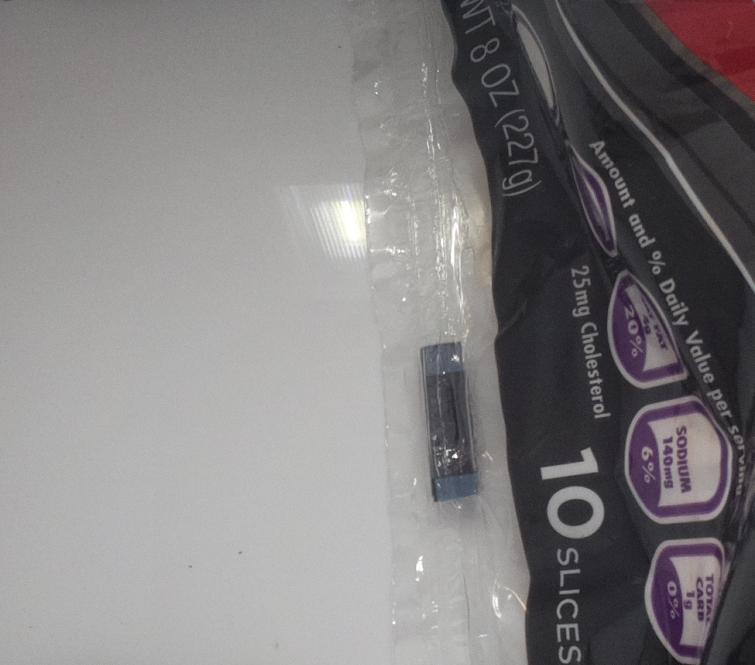
Data/trash/trash31.jpg
