umiahmed30/RuTrash/Data/trash/trash32.jpg

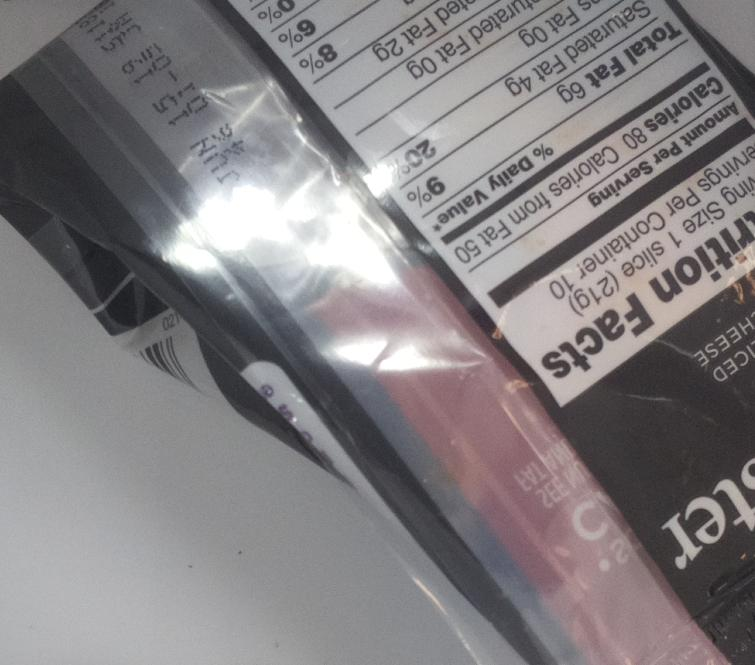
Data/trash/trash32.jpg
