umiahmed30/RuTrash/Data/trash/trash36.jpg

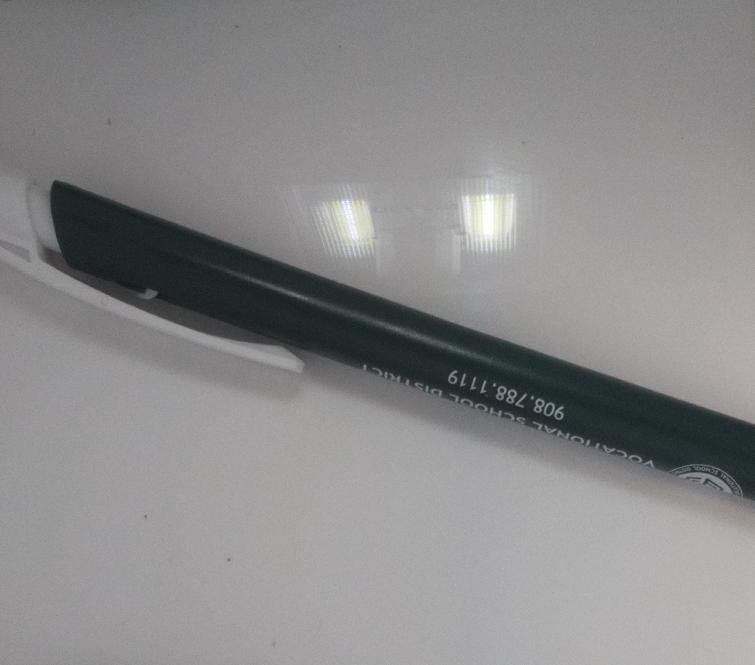
Data/trash/trash36.jpg
