umiahmed30/RuTrash/Data/trash/trash37.jpg

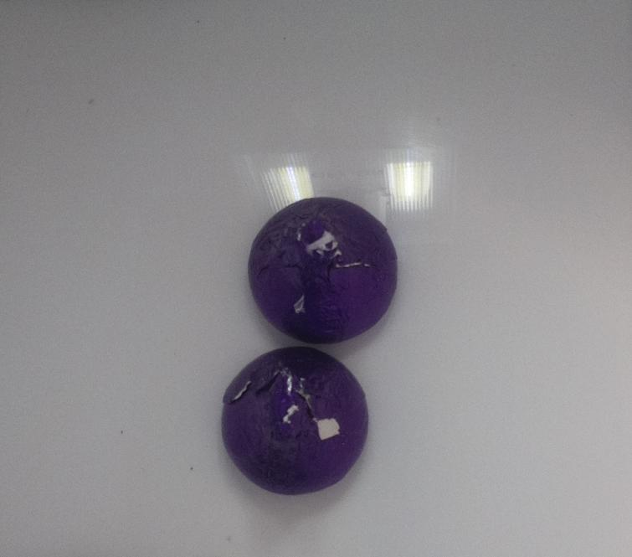
Data/trash/trash37.jpg
