umiahmed30/RuTrash/Data/trash/trash39.jpg

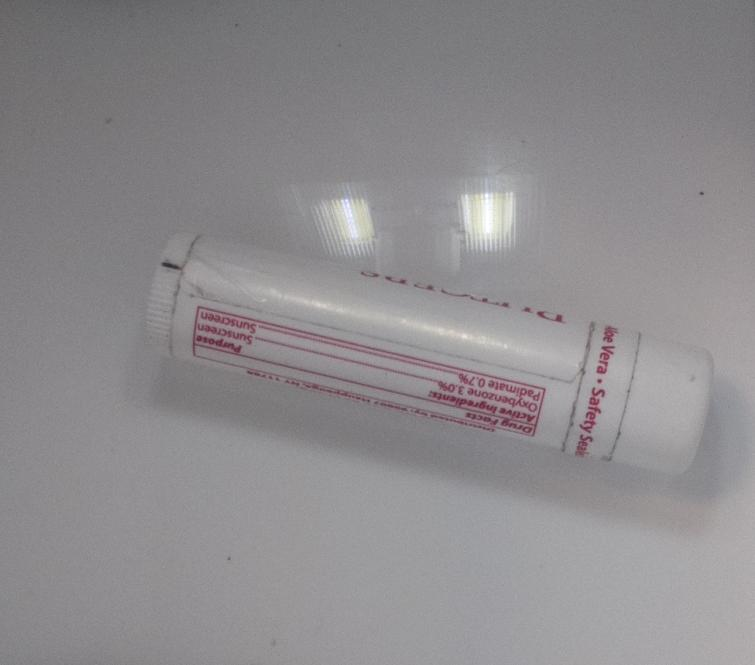
Data/trash/trash39.jpg
