umiahmed30/RuTrash/Data/trash/trash42.jpg

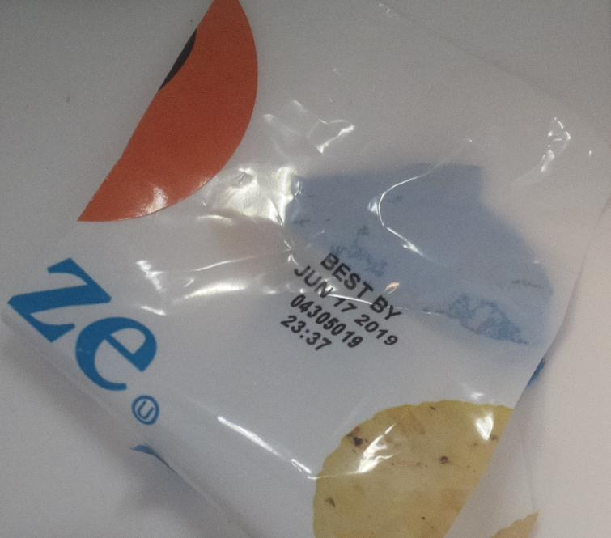
Data/trash/trash42.jpg
