umiahmed30/RuTrash/Data/trash/trash46.jpg

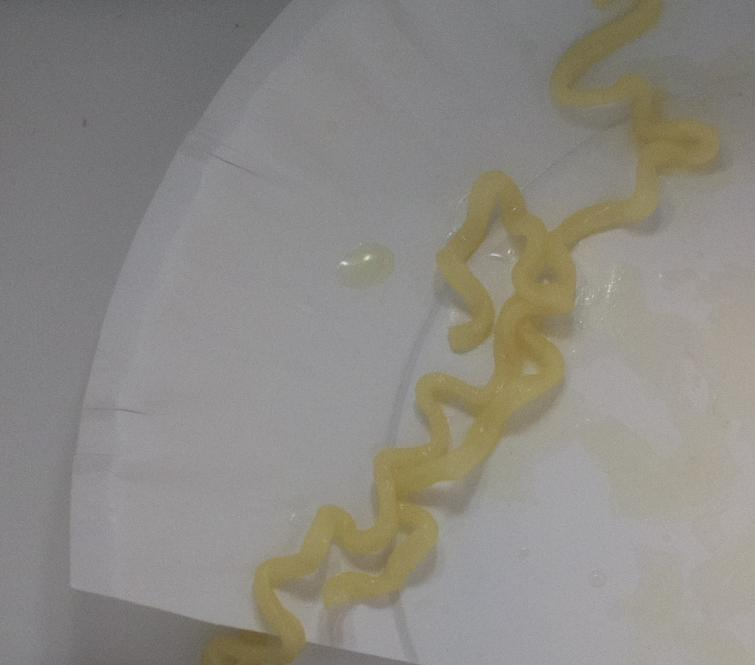
Data/trash/trash46.jpg
