umiahmed30/RuTrash/Data/trash/trash48.jpg

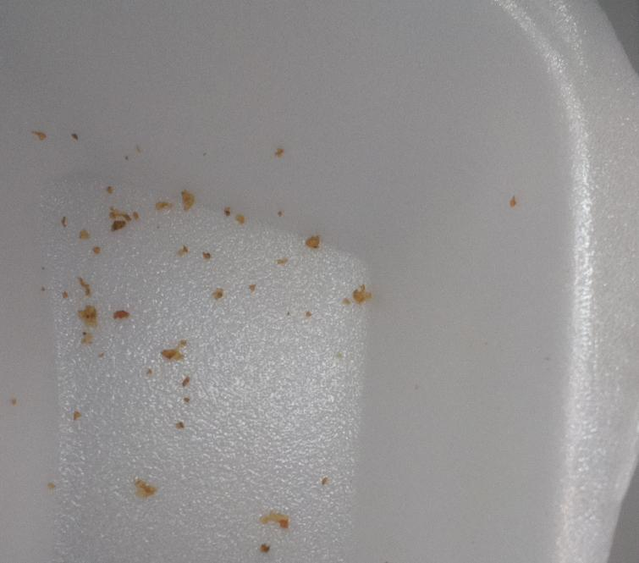
Data/trash/trash48.jpg
