umiahmed30/RuTrash/Data/trash/trash50.jpg

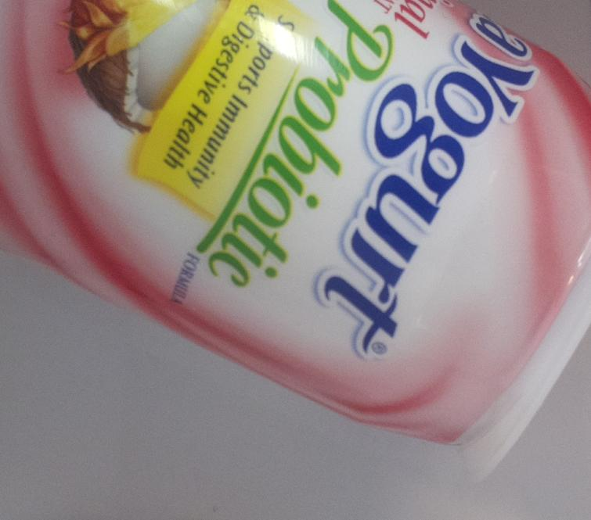
Data/trash/trash50.jpg
