umiahmed30/RuTrash/Data/trash/trash52.jpg

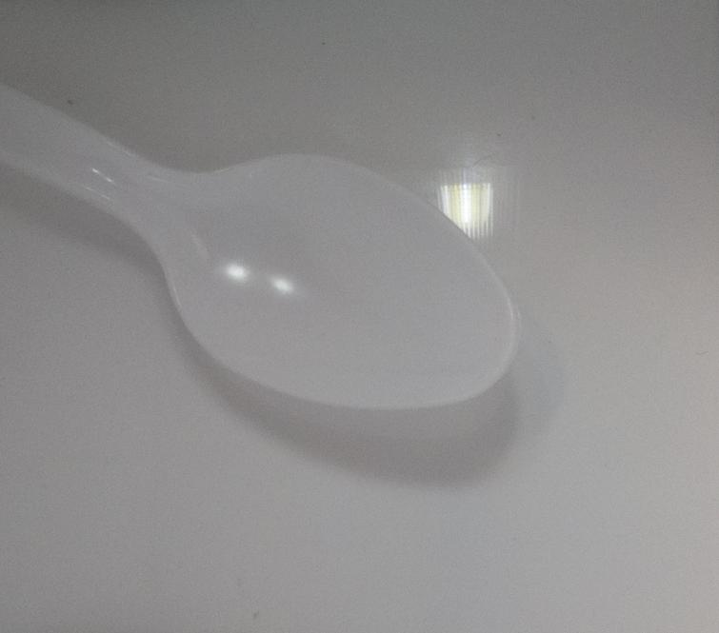
Data/trash/trash52.jpg
