umiahmed30/RuTrash/Data/trash/trash53.jpg

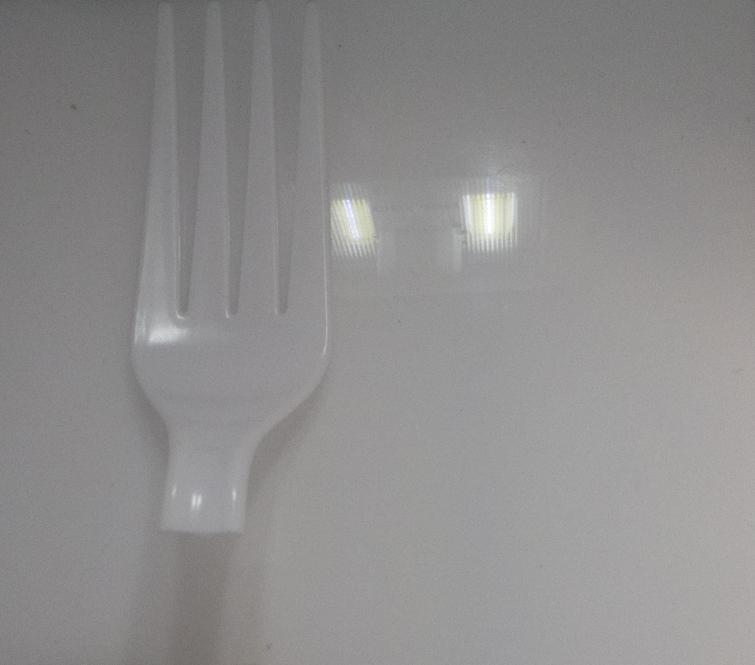
Data/trash/trash53.jpg
