umiahmed30/RuTrash/Data/trash/trash54.jpg

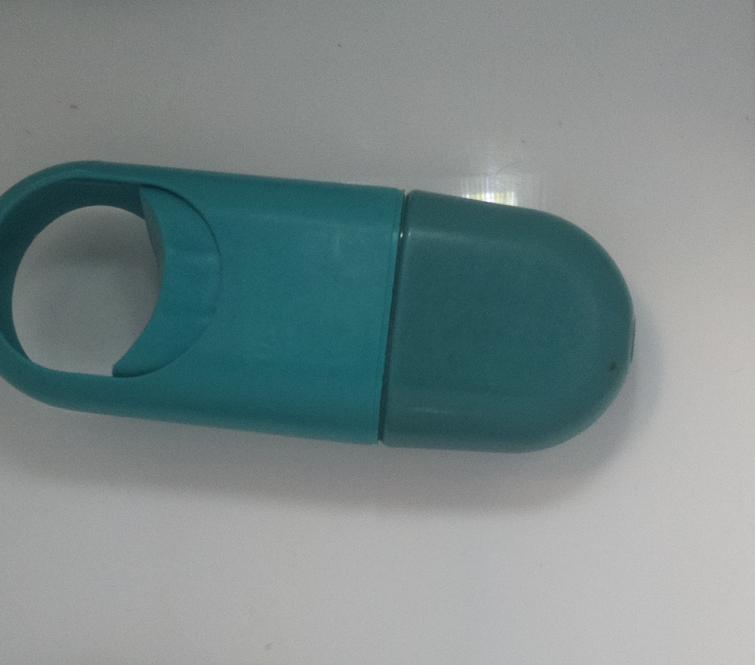
Data/trash/trash54.jpg
