umiahmed30/RuTrash/Data/Valid/metal/metal_new_0.jpg

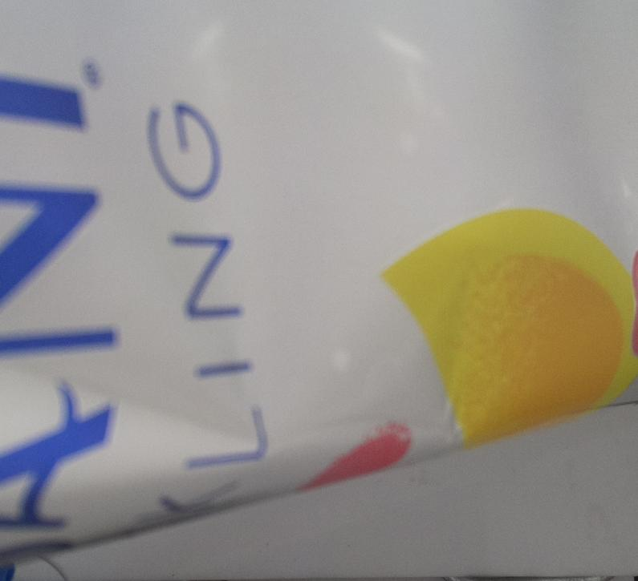
Data/Valid/metal/metal_new_0.jpg
