umiahmed30/RuTrash/Data/Valid/metal/metal_new_1.jpg

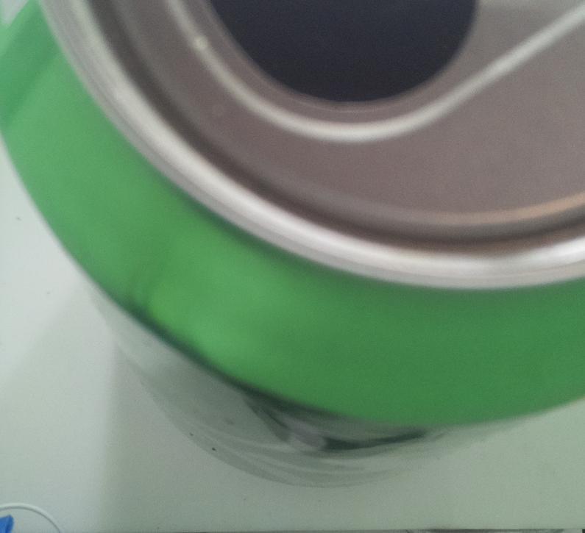
Data/Valid/metal/metal_new_1.jpg
