umiahmed30/RuTrash/Data/Valid/metal/metal_new_2.jpg

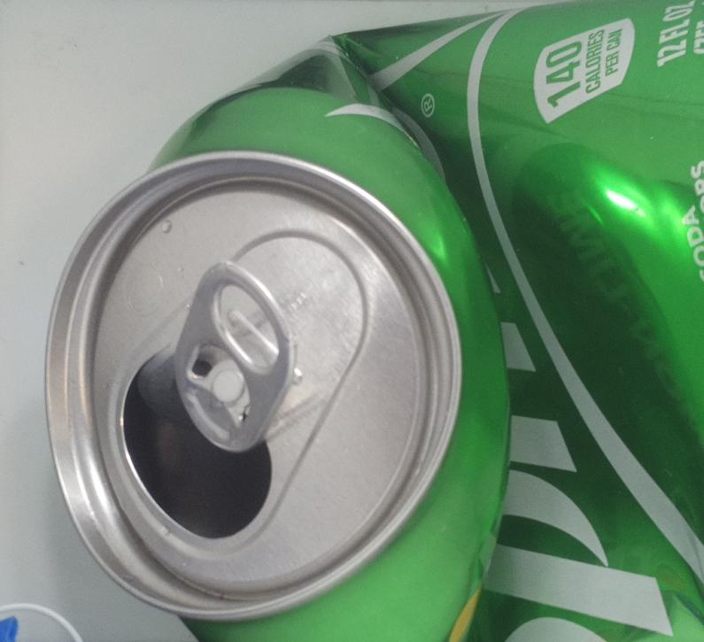
Data/Valid/metal/metal_new_2.jpg
