umiahmed30/RuTrash/Data/Valid/metal/metal_new_3.jpg

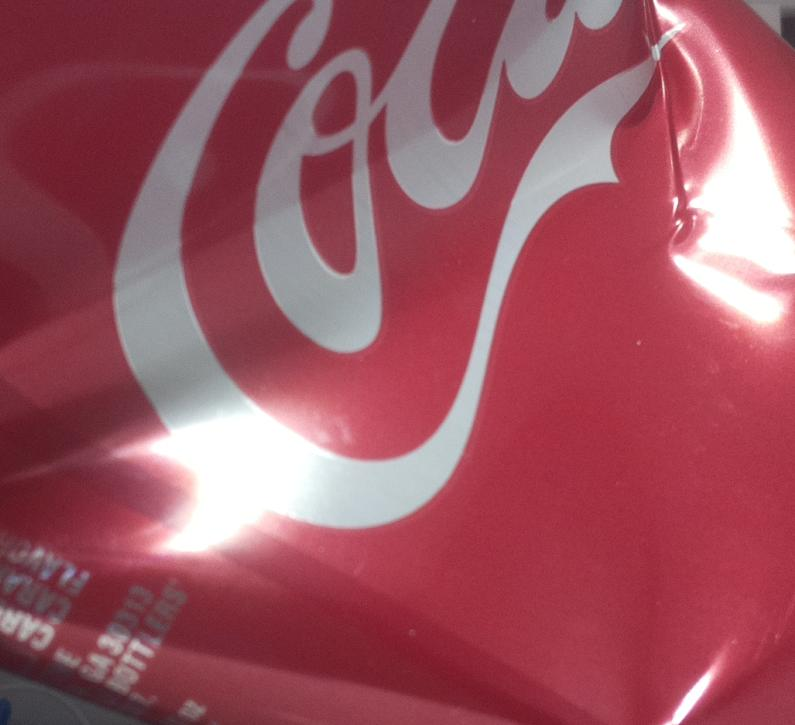
Data/Valid/metal/metal_new_3.jpg
