umiahmed30/RuTrash/Data/Valid/metal/metal_new_4.jpg

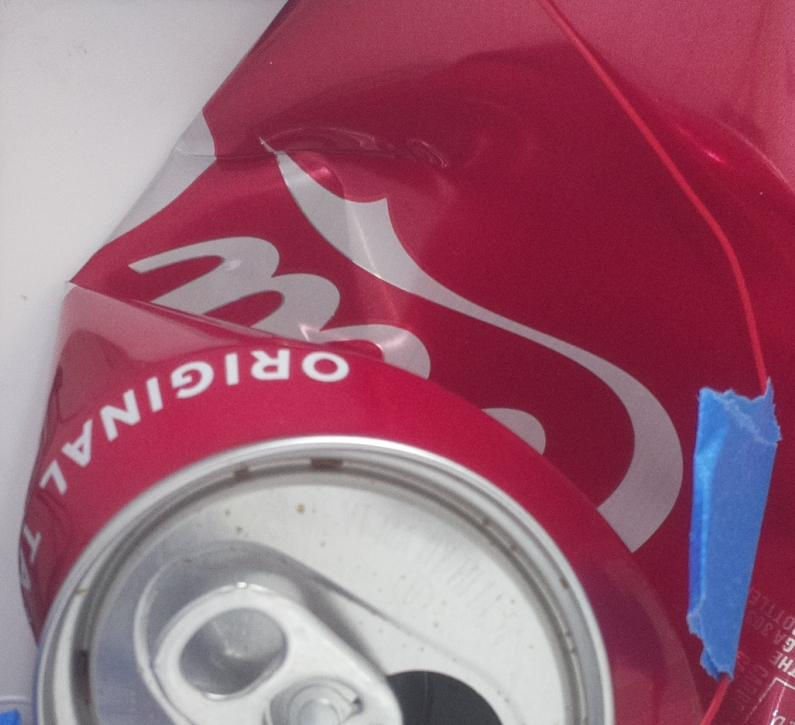
Data/Valid/metal/metal_new_4.jpg
