umiahmed30/RuTrash/Data/Valid/metal/metal_new_5.jpg

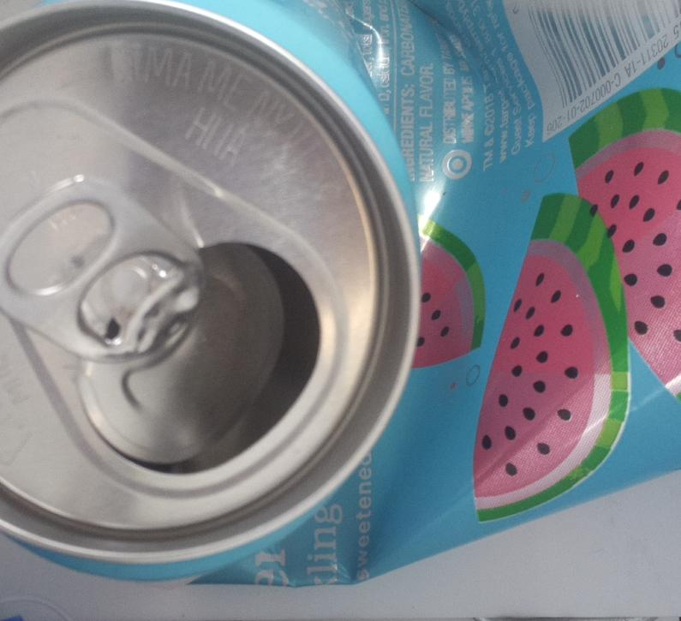
Data/Valid/metal/metal_new_5.jpg
