umiahmed30/RuTrash/Data/Valid/metal/metal_new_6.jpg

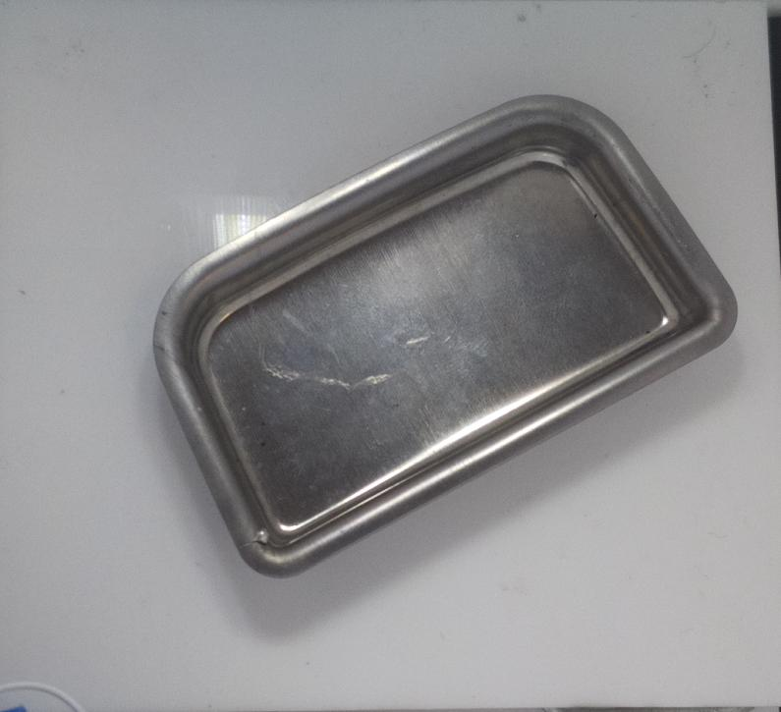
Data/Valid/metal/metal_new_6.jpg
