umiahmed30/RuTrash/Data/Valid/metal/metal_new_7.jpg

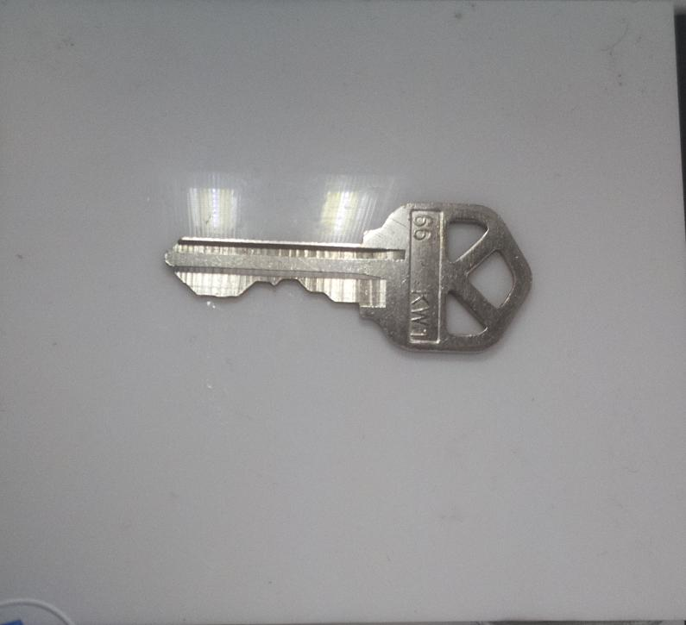
Data/Valid/metal/metal_new_7.jpg
