umiahmed30/RuTrash/Data/Valid/metal/metal_new_8.jpg

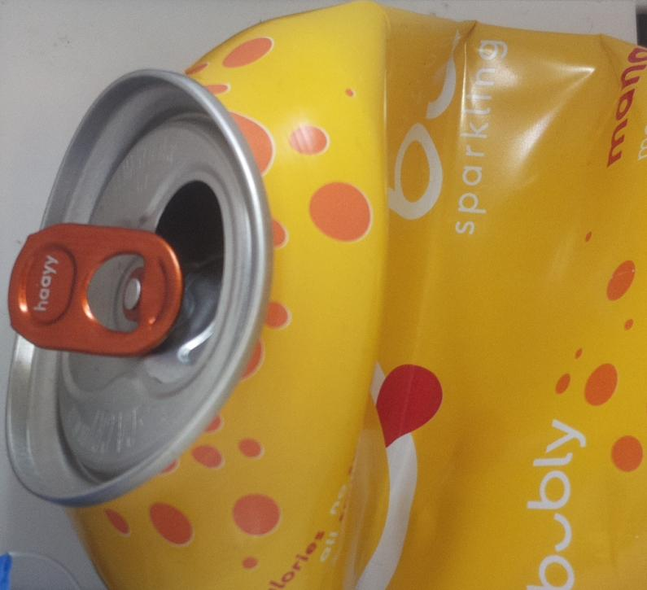
Data/Valid/metal/metal_new_8.jpg
