umiahmed30/RuTrash/Data/Valid/metal/metal_new_10.jpg

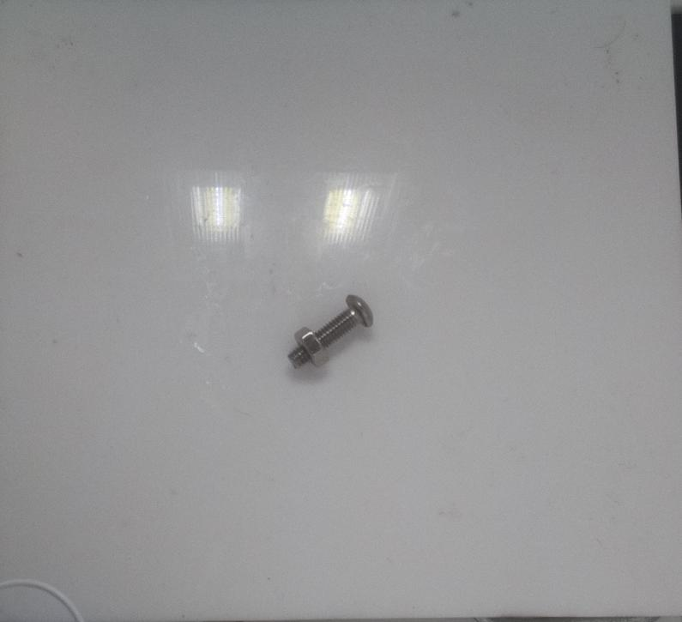
Data/Valid/metal/metal_new_10.jpg
