umiahmed30/RuTrash/Data/Valid/metal/metal_new_11.jpg

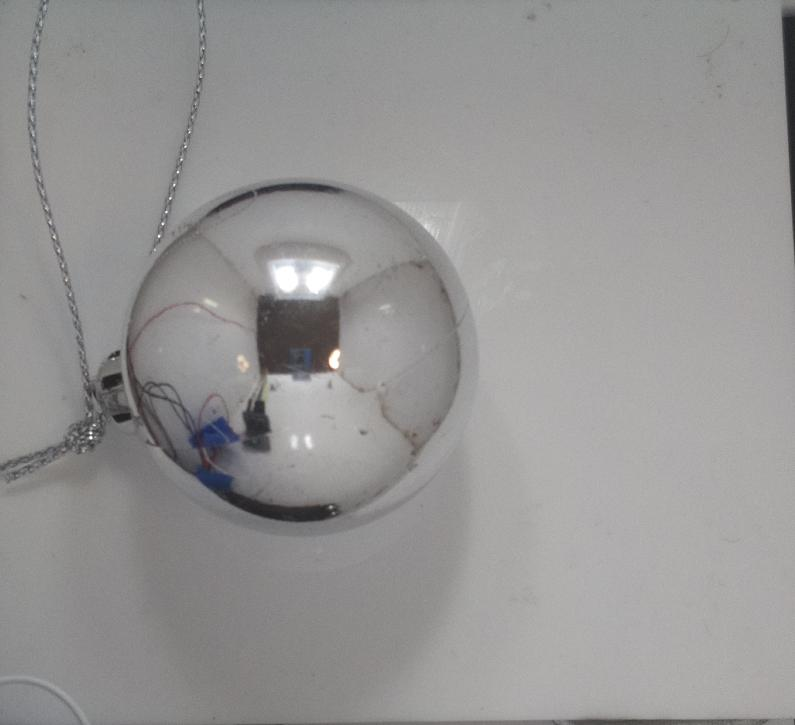
Data/Valid/metal/metal_new_11.jpg
