umiahmed30/RuTrash/Data/Valid/metal/metal_new_12.jpg

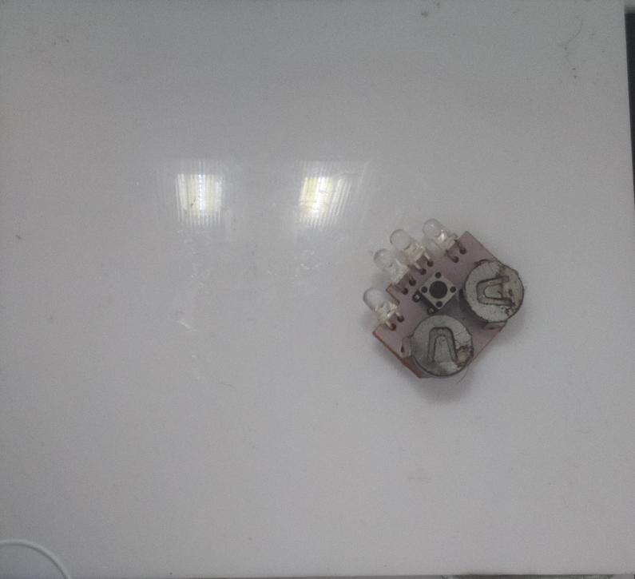
Data/Valid/metal/metal_new_12.jpg
