umiahmed30/RuTrash/Data/Valid/metal/metal_new_15.jpg

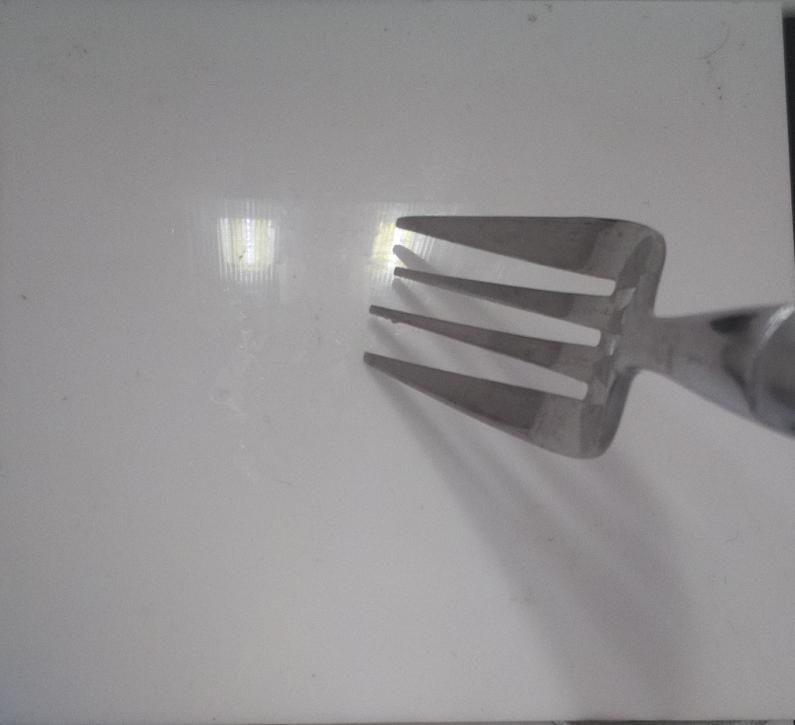
Data/Valid/metal/metal_new_15.jpg
