umiahmed30/RuTrash/Data/Valid/metal/metal_new_16.jpg

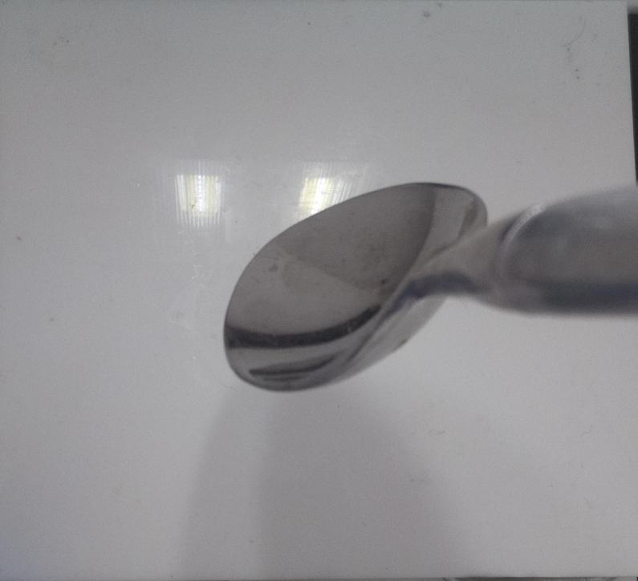
Data/Valid/metal/metal_new_16.jpg
