umiahmed30/RuTrash/Data/Valid/metal/metal_new_17.jpg

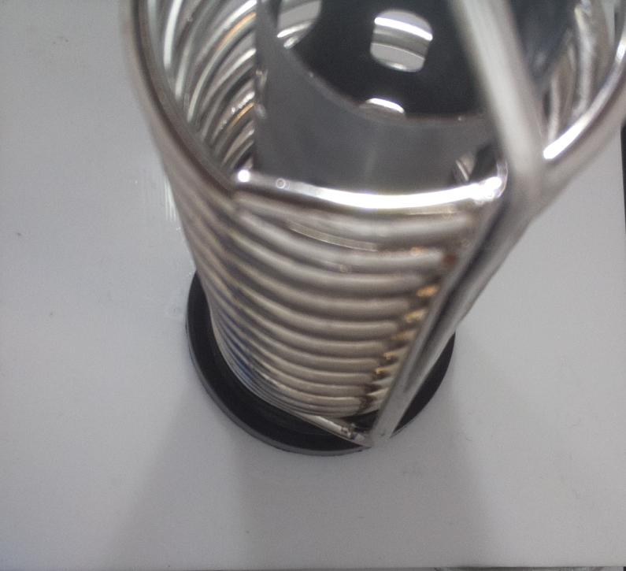
Data/Valid/metal/metal_new_17.jpg
