umiahmed30/RuTrash/Data/Valid/metal/metal_new_18.jpg

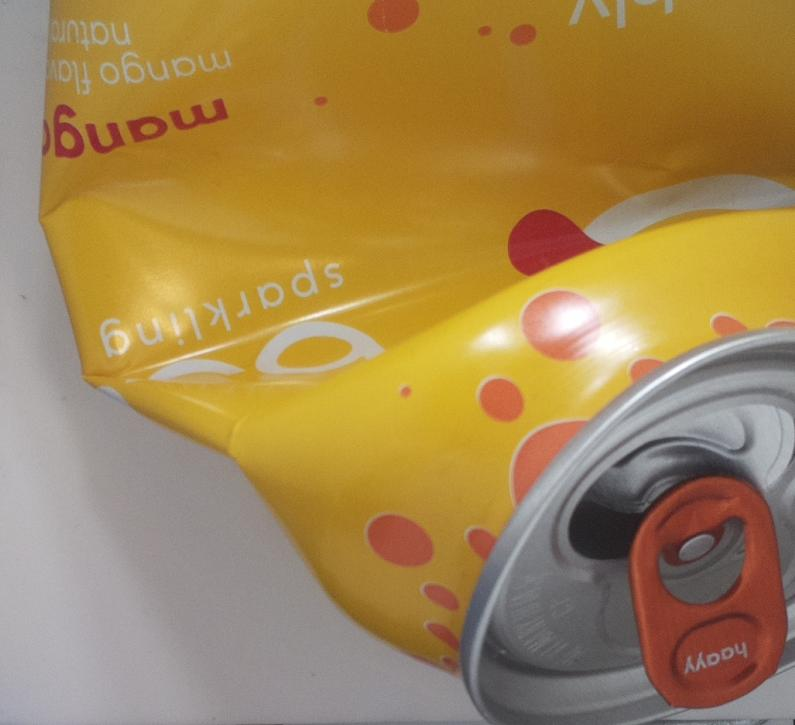
Data/Valid/metal/metal_new_18.jpg
