umiahmed30/RuTrash/Data/Valid/metal/metal_new_19.jpg

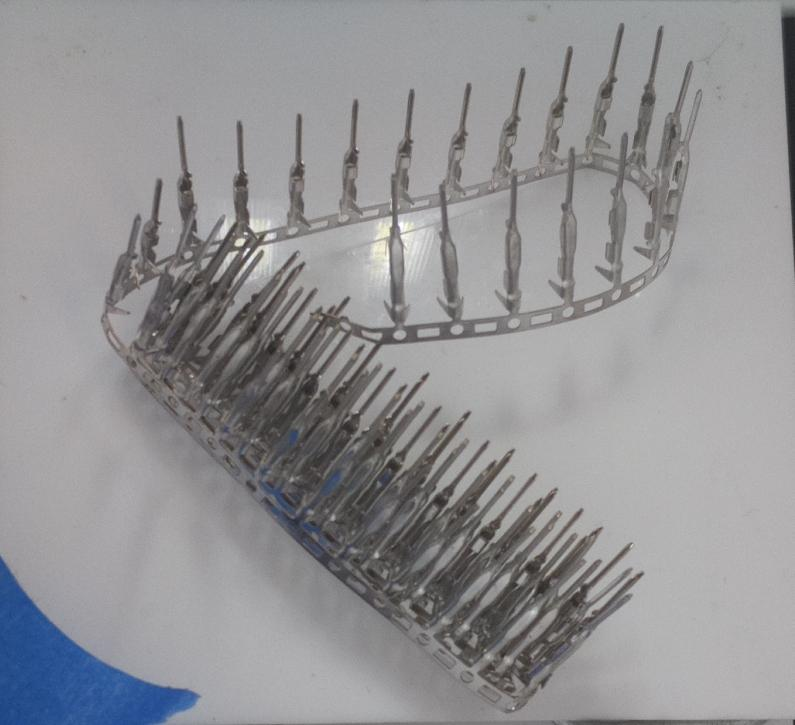
Data/Valid/metal/metal_new_19.jpg
