umiahmed30/RuTrash/Data/Valid/metal/metal_new_20.jpg

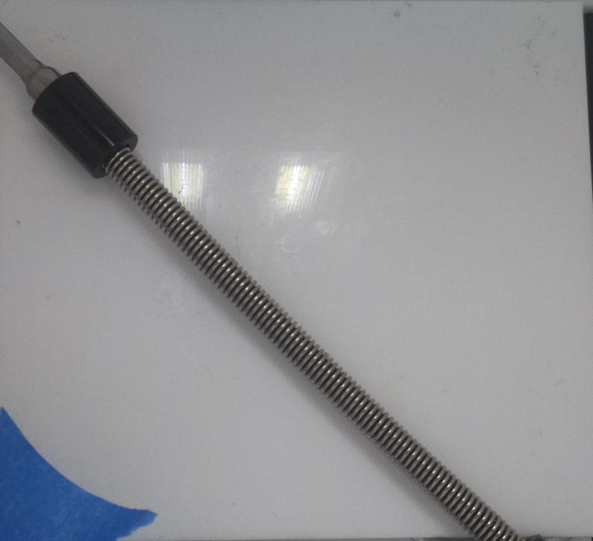
Data/Valid/metal/metal_new_20.jpg
