umiahmed30/RuTrash/Data/Valid/metal/metal_new_21.jpg

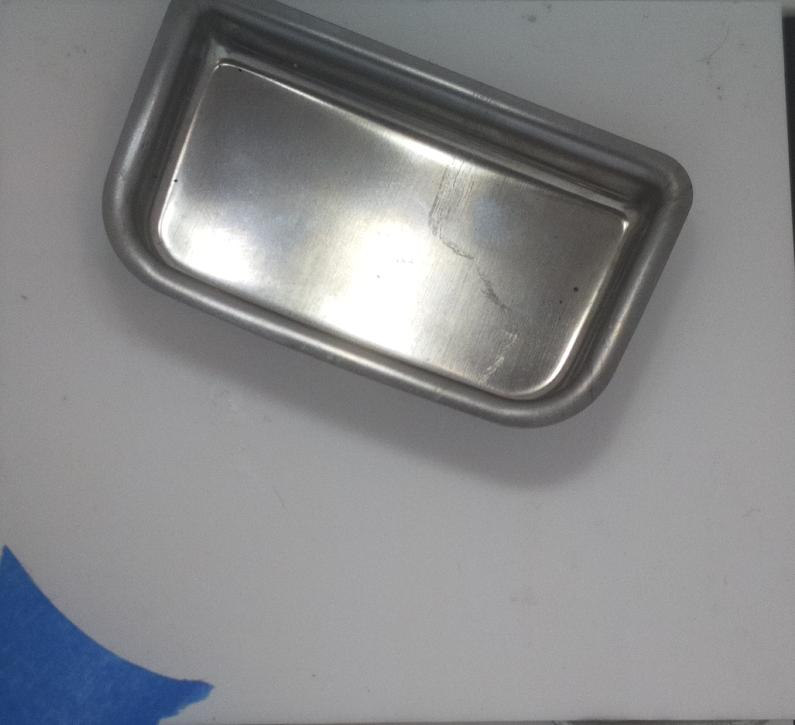
Data/Valid/metal/metal_new_21.jpg
