umiahmed30/RuTrash/Data/Valid/metal/metal_new_22.jpg

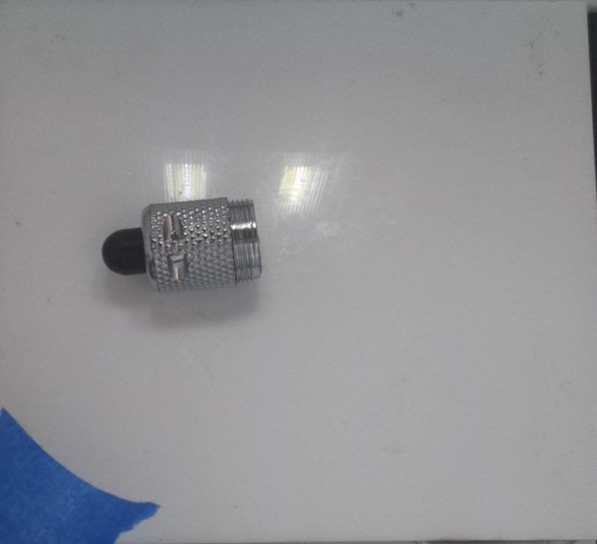
Data/Valid/metal/metal_new_22.jpg
