umiahmed30/RuTrash/Data/Valid/metal/metal_new_23.jpg

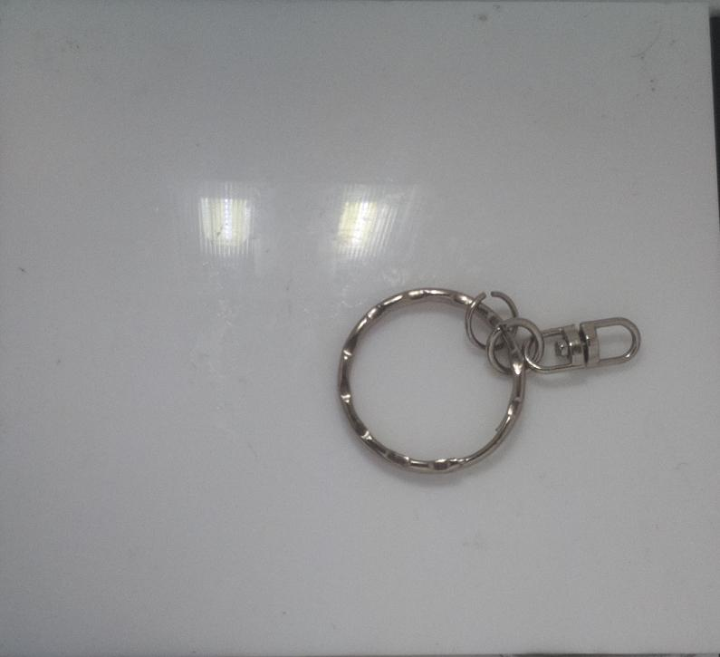
Data/Valid/metal/metal_new_23.jpg
