umiahmed30/RuTrash/Data/Valid/metal/metal_new_24.jpg

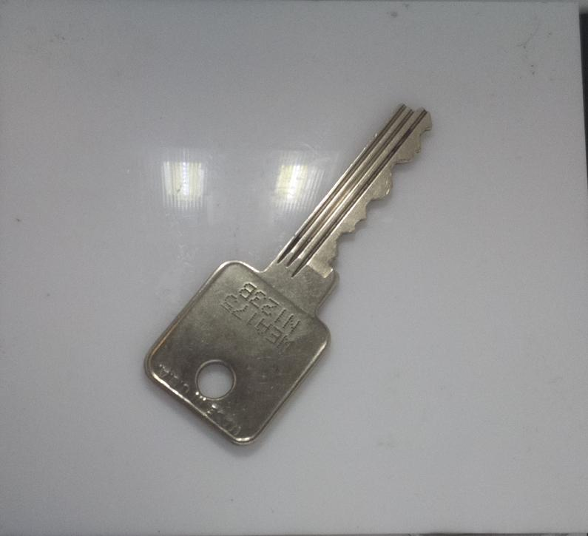
Data/Valid/metal/metal_new_24.jpg
