umiahmed30/RuTrash/Data/Valid/metal/metal_new_25.jpg

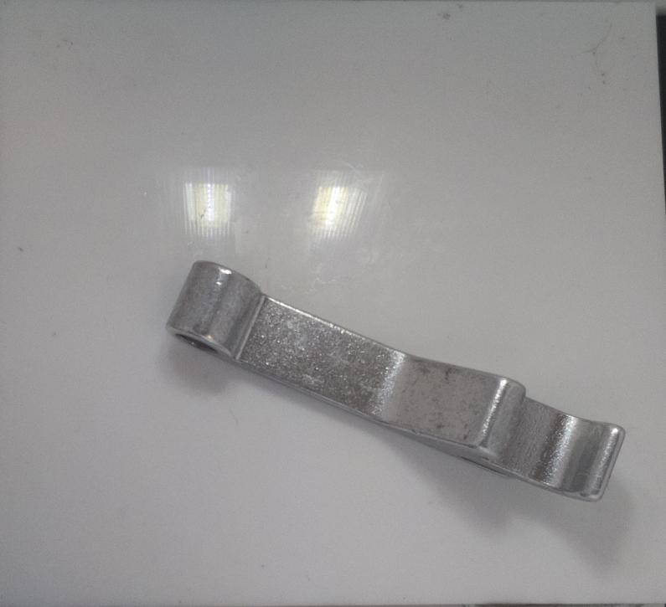
Data/Valid/metal/metal_new_25.jpg
