umiahmed30/RuTrash/Data/Valid/metal/metal_new_28.jpg

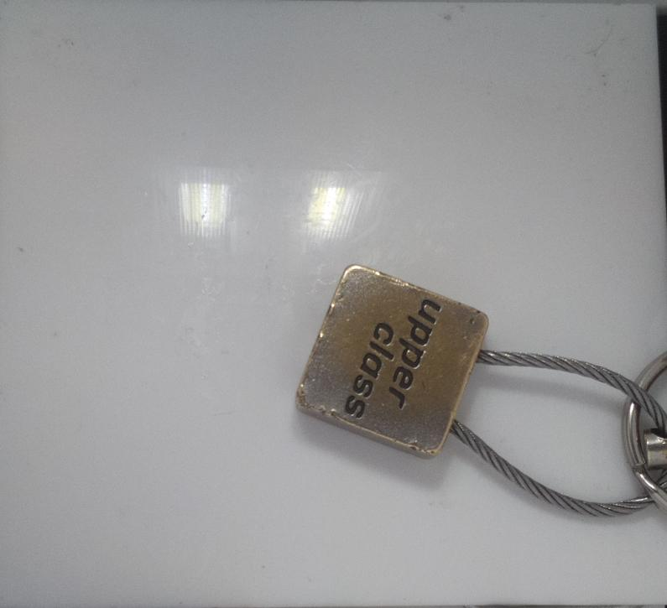
Data/Valid/metal/metal_new_28.jpg
