umiahmed30/RuTrash/Data/Valid/metal/metal_new_29.jpg

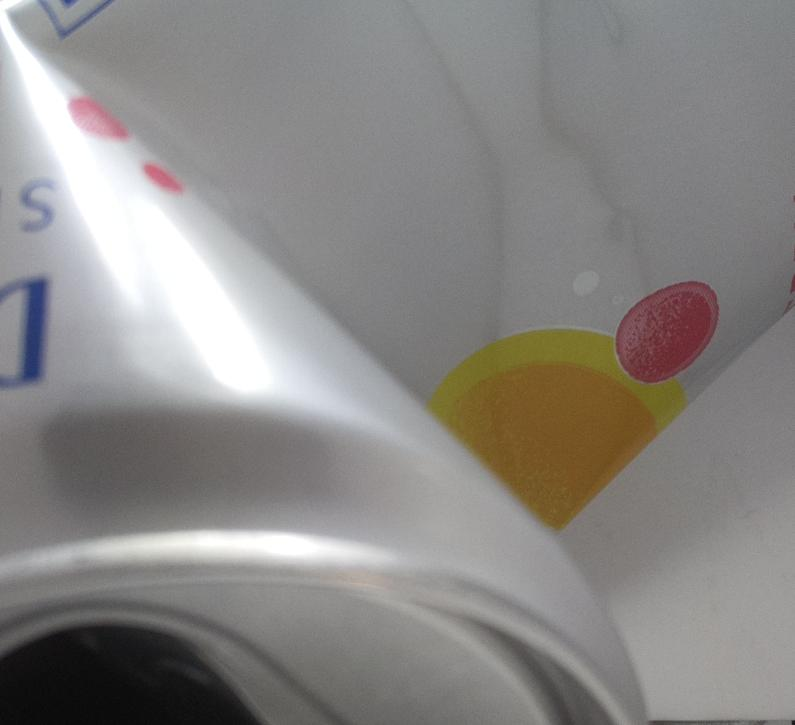
Data/Valid/metal/metal_new_29.jpg
