umiahmed30/RuTrash/Data/Valid/metal/metal_new_30.jpg

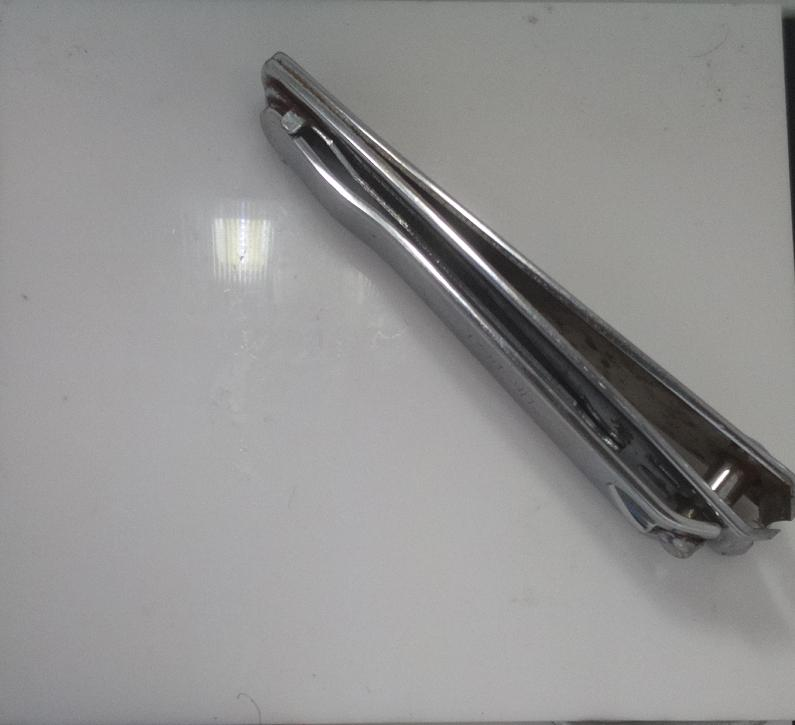
Data/Valid/metal/metal_new_30.jpg
