umiahmed30/RuTrash/Data/Valid/metal/metal_new_31.jpg

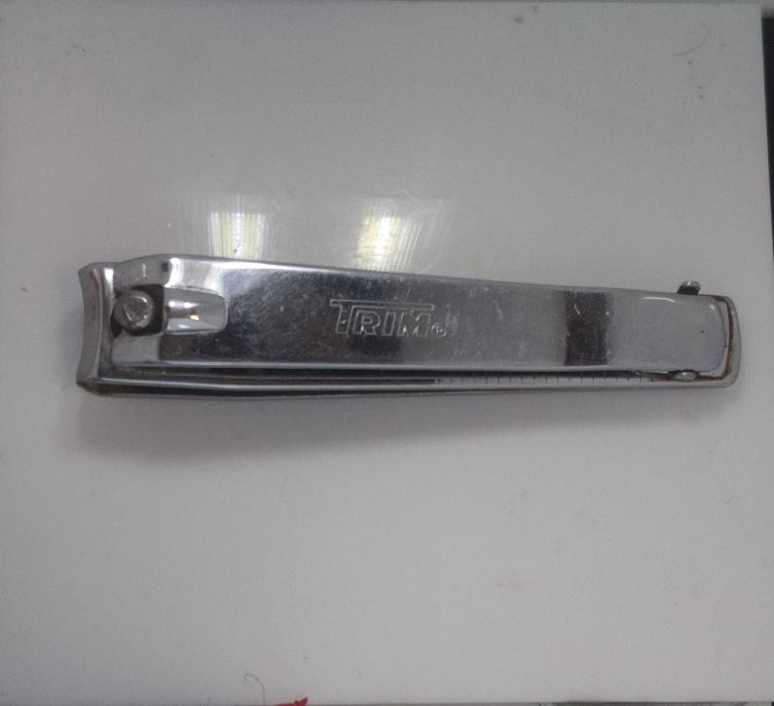
Data/Valid/metal/metal_new_31.jpg
