umiahmed30/RuTrash/Data/Valid/metal/metal_new_32.jpg

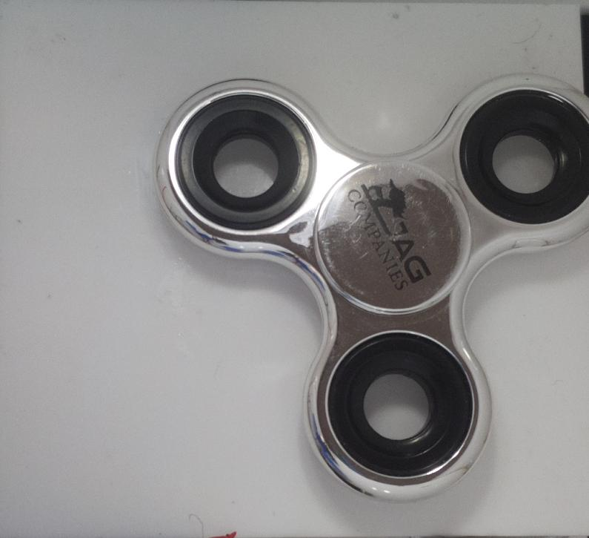
Data/Valid/metal/metal_new_32.jpg
