umiahmed30/RuTrash/Data/Valid/paper/paper_new_0.jpg

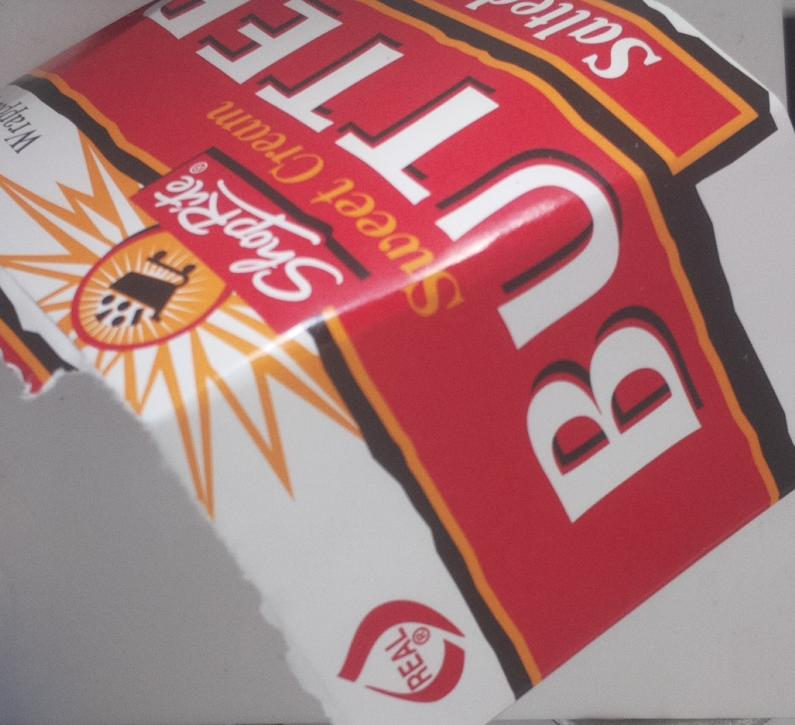
Data/Valid/paper/paper_new_0.jpg
