umiahmed30/RuTrash/Data/Valid/paper/paper_new_1.jpg

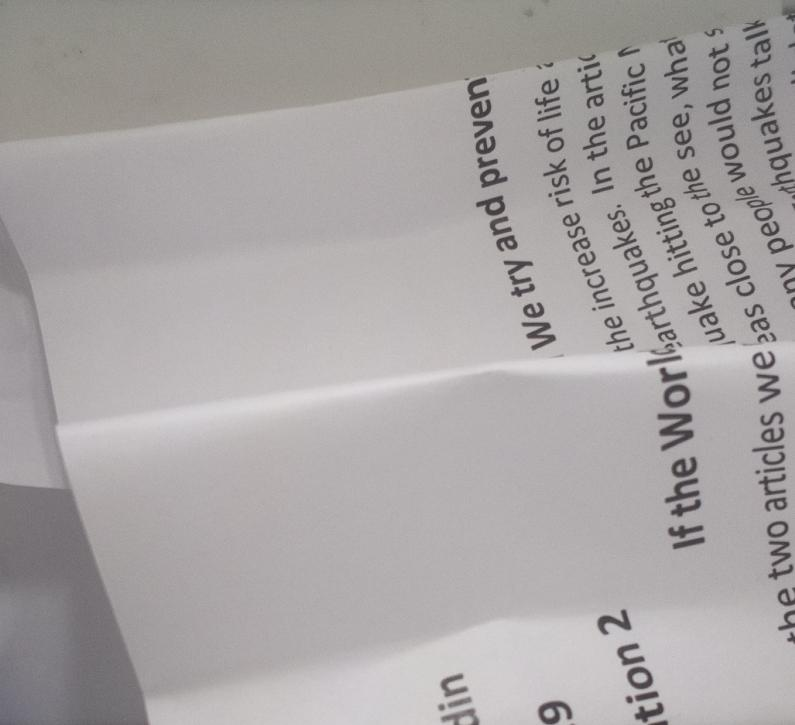
Data/Valid/paper/paper_new_1.jpg
