umiahmed30/RuTrash/Data/Valid/paper/paper_new_2.jpg

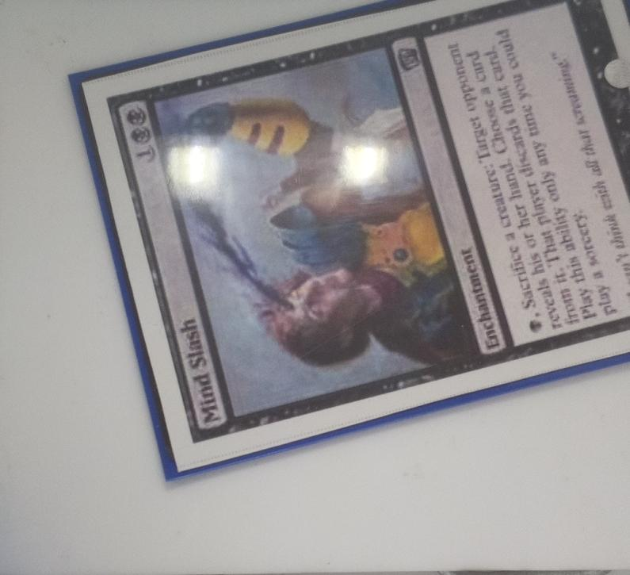
Data/Valid/paper/paper_new_2.jpg
