umiahmed30/RuTrash/Data/Valid/paper/paper_new_7.jpg

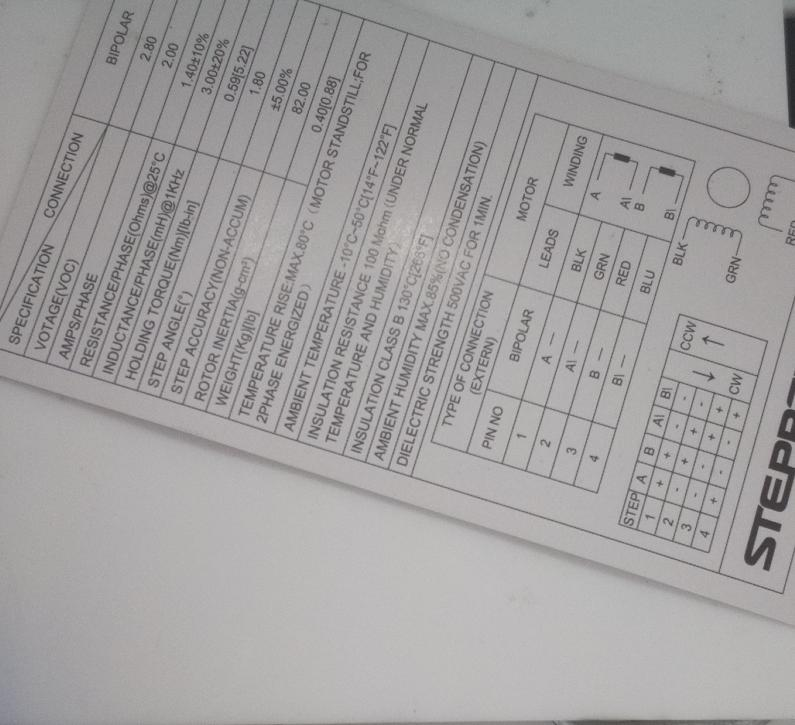
Data/Valid/paper/paper_new_7.jpg
