umiahmed30/RuTrash/Data/Valid/paper/paper_new_8.jpg

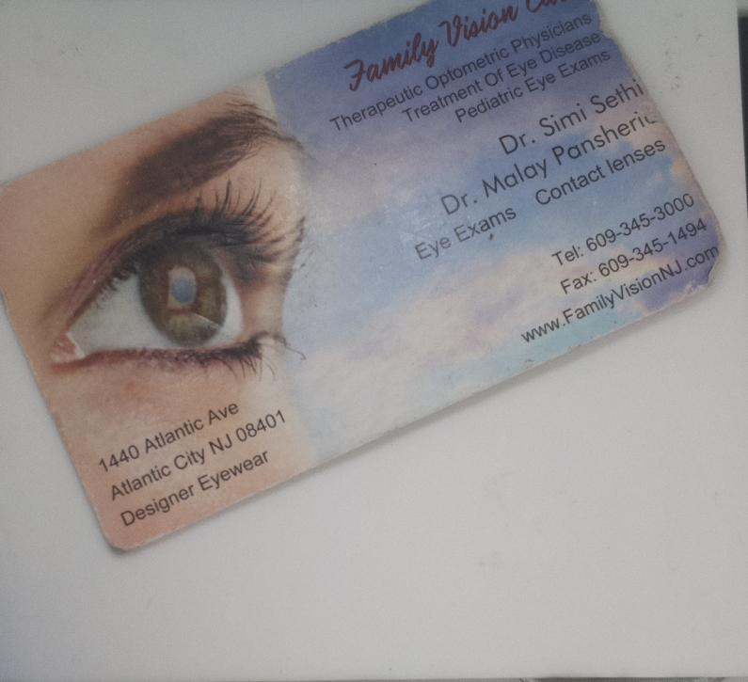
Data/Valid/paper/paper_new_8.jpg
