umiahmed30/RuTrash/Data/Valid/paper/paper_new_11.jpg

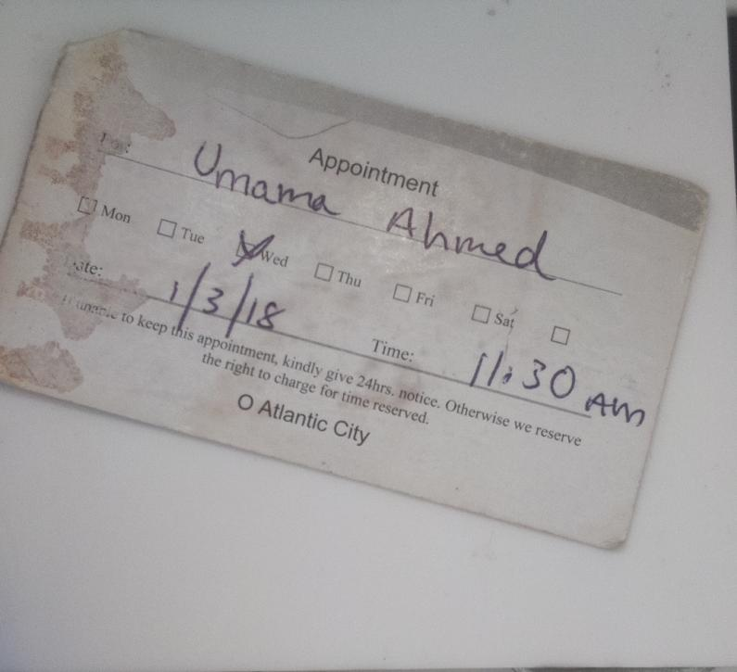
Data/Valid/paper/paper_new_11.jpg
