umiahmed30/RuTrash/Data/Valid/paper/paper_new_19.jpg

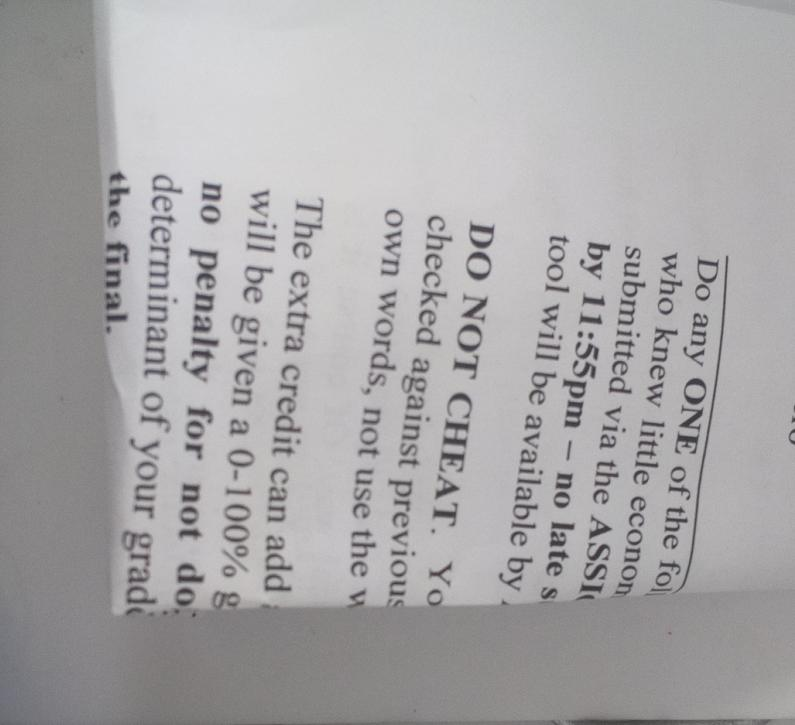
Data/Valid/paper/paper_new_19.jpg
