umiahmed30/RuTrash/Data/Valid/paper/paper_new_20.jpg

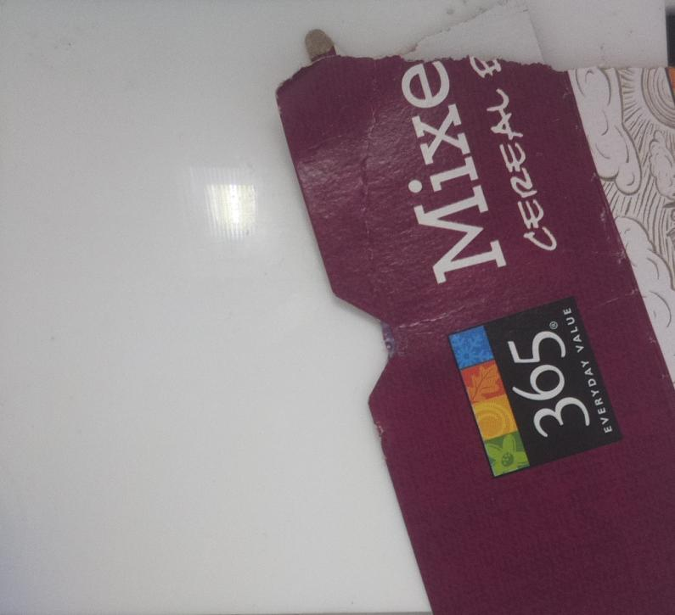
Data/Valid/paper/paper_new_20.jpg
