umiahmed30/RuTrash/Data/Valid/paper/paper_new_22.jpg

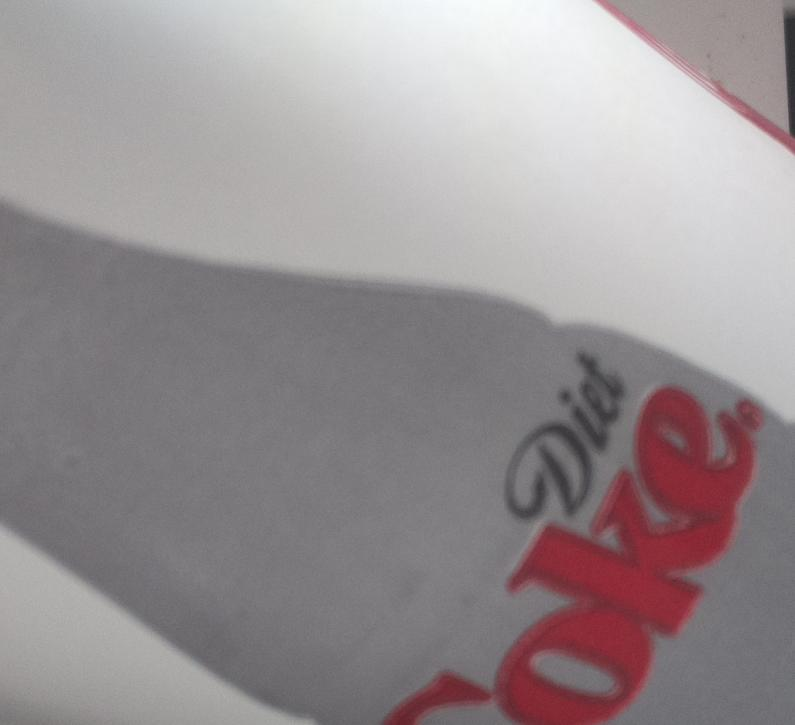
Data/Valid/paper/paper_new_22.jpg
