umiahmed30/RuTrash/Data/Valid/paper/paper_new_23.jpg

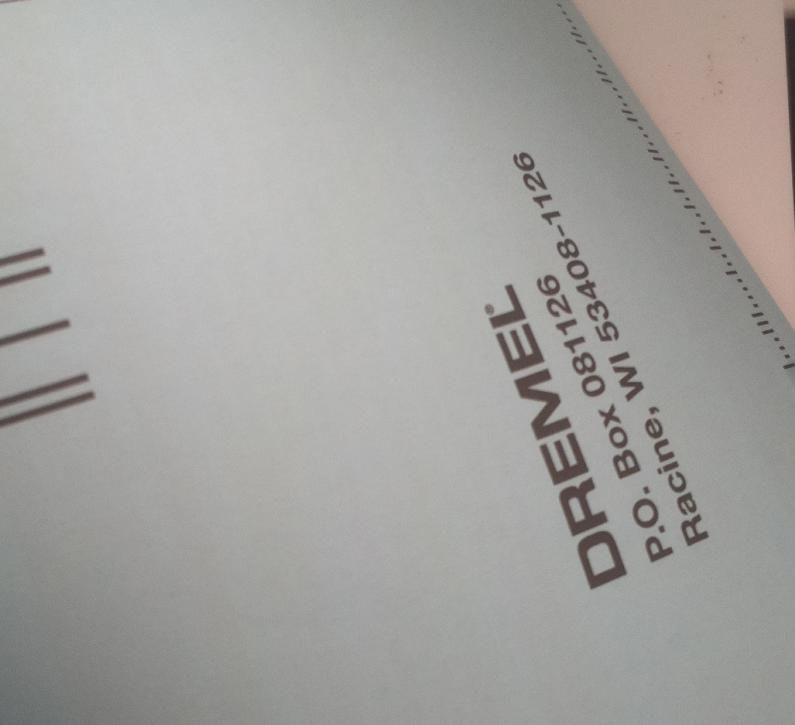
Data/Valid/paper/paper_new_23.jpg
