umiahmed30/RuTrash/Data/Valid/paper/paper_new_24.jpg

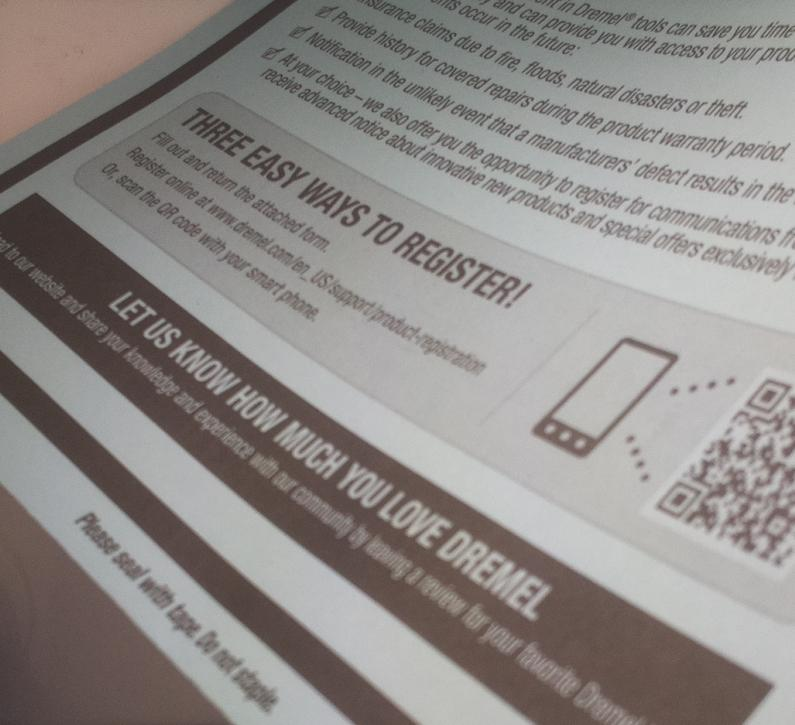
Data/Valid/paper/paper_new_24.jpg
