umiahmed30/RuTrash/Data/Valid/paper/paper_new_26.jpg

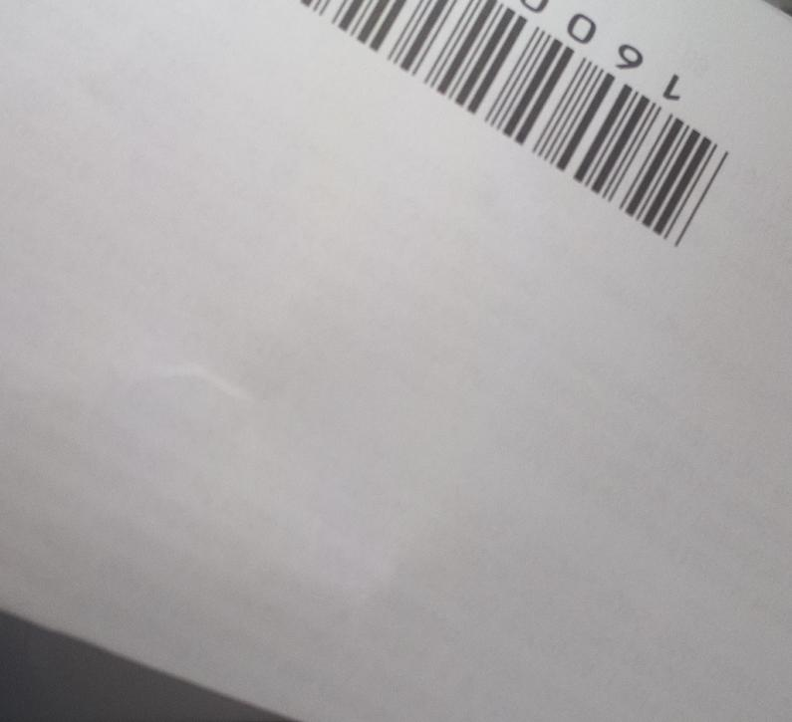
Data/Valid/paper/paper_new_26.jpg
