umiahmed30/RuTrash/Data/Valid/paper/paper_new_27.jpg

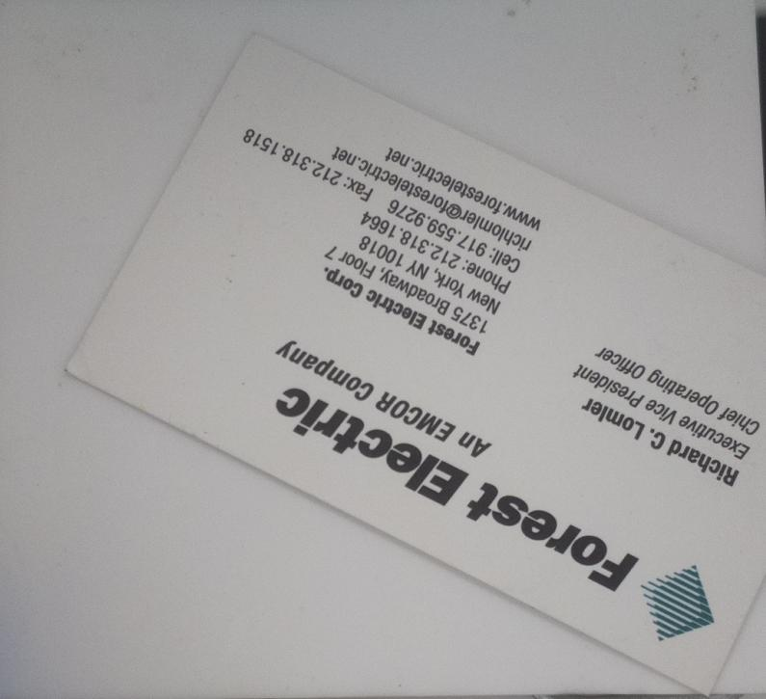
Data/Valid/paper/paper_new_27.jpg
