umiahmed30/RuTrash/Data/Valid/paper/paper_new_28.jpg

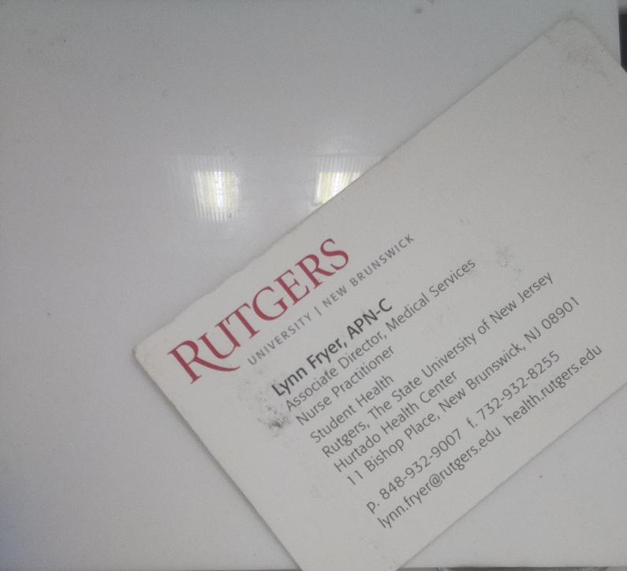
Data/Valid/paper/paper_new_28.jpg
