umiahmed30/RuTrash/Data/Valid/paper/paper_new_30.jpg

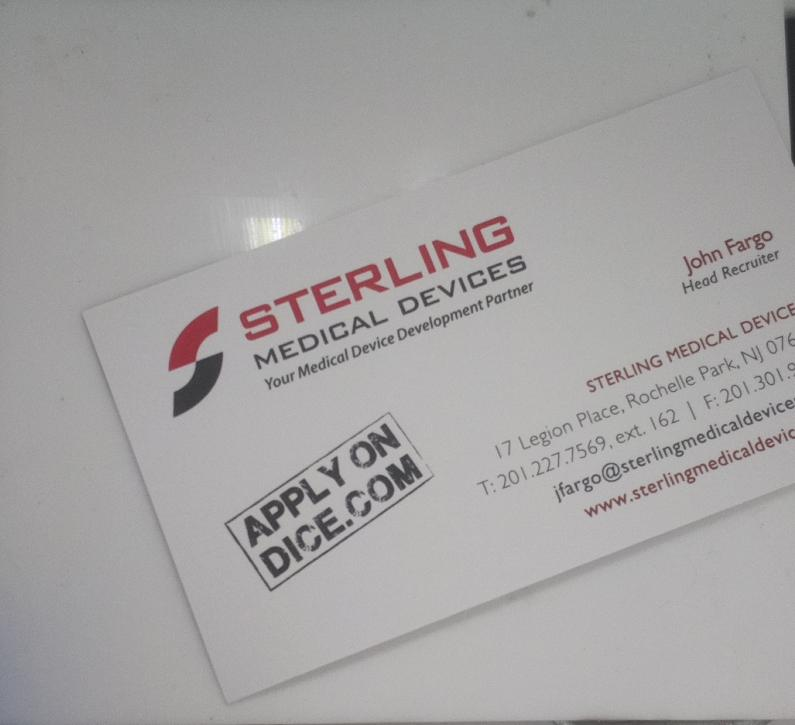
Data/Valid/paper/paper_new_30.jpg
