umiahmed30/RuTrash/Data/Valid/paper/paper_new_31.jpg

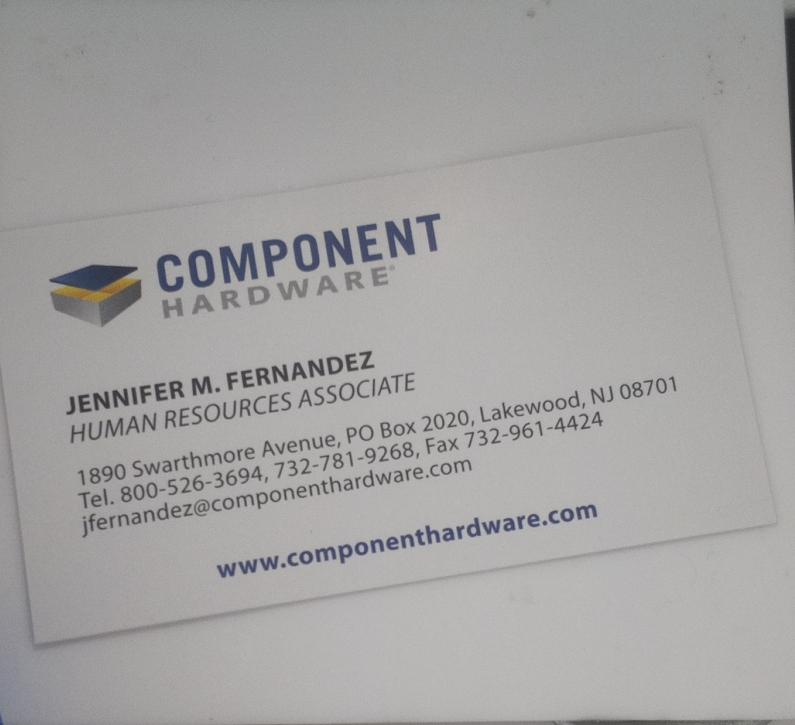
Data/Valid/paper/paper_new_31.jpg
