umiahmed30/RuTrash/Data/Valid/paper/paper_new_32.jpg

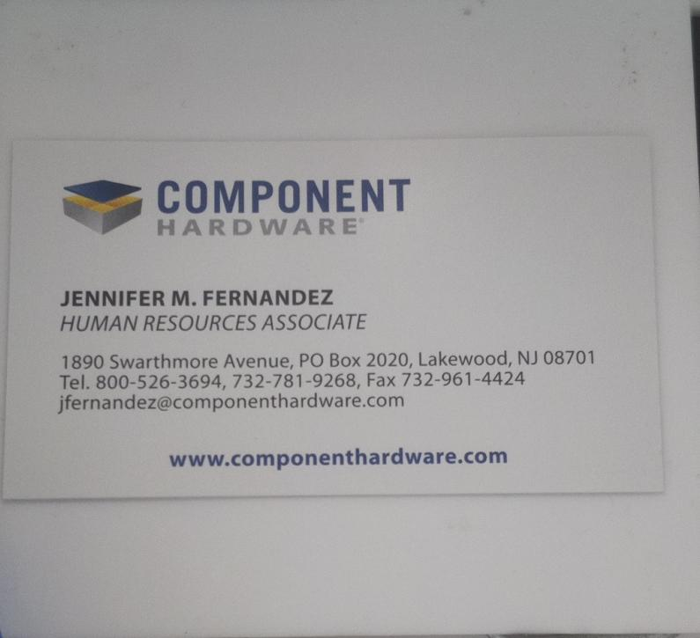
Data/Valid/paper/paper_new_32.jpg
