umiahmed30/RuTrash/Data/Valid/plastic/plastic_new_0.jpg

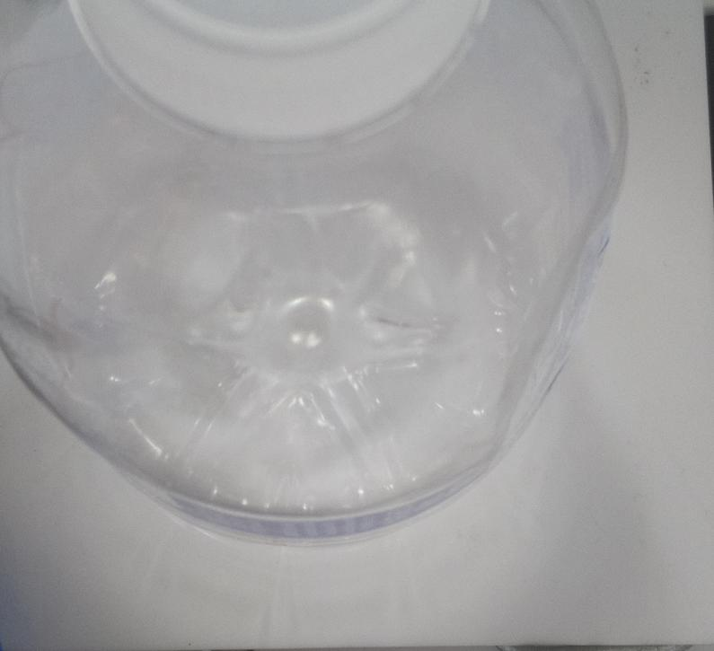
Data/Valid/plastic/plastic_new_0.jpg
