umiahmed30/RuTrash/Data/Valid/plastic/plastic_new_1.jpg

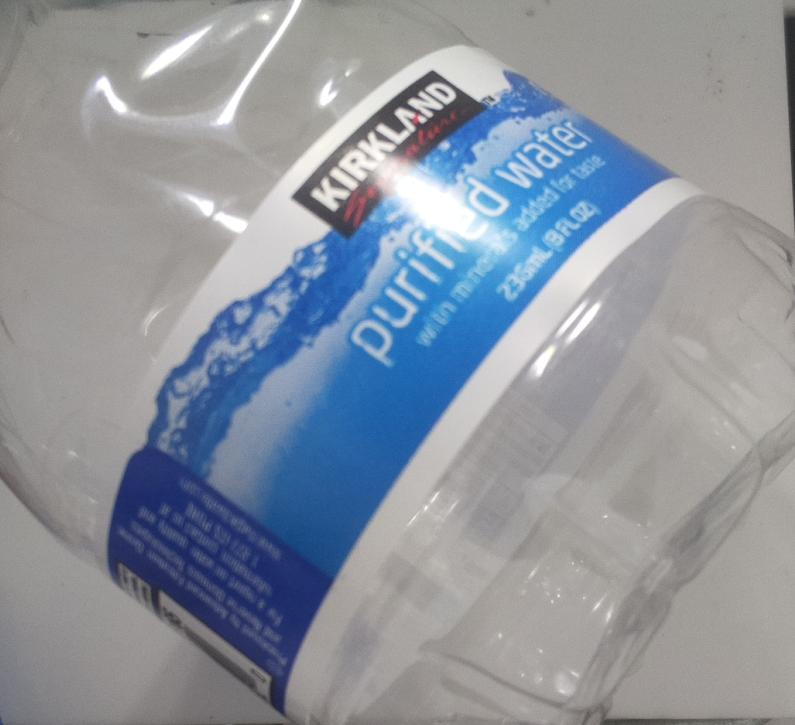
Data/Valid/plastic/plastic_new_1.jpg
