umiahmed30/RuTrash/Data/Valid/plastic/plastic_new_2.jpg

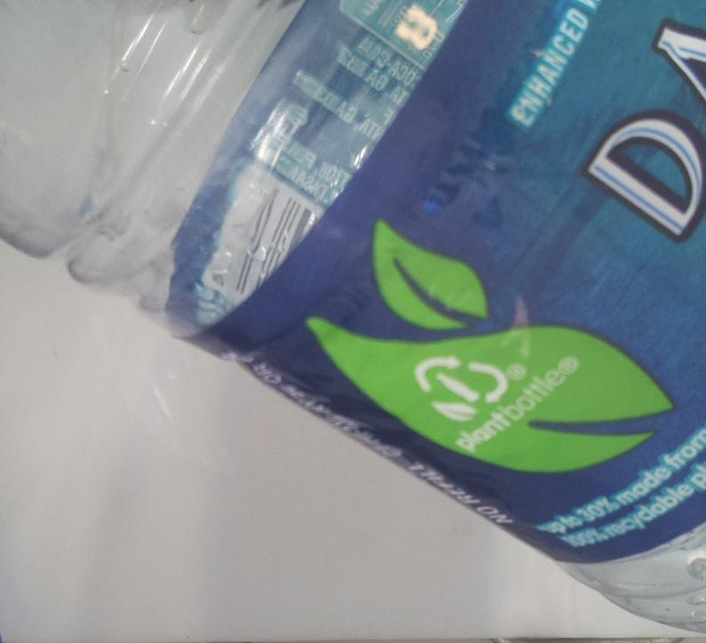
Data/Valid/plastic/plastic_new_2.jpg
