umiahmed30/RuTrash/Data/Valid/plastic/plastic_new_3.jpg

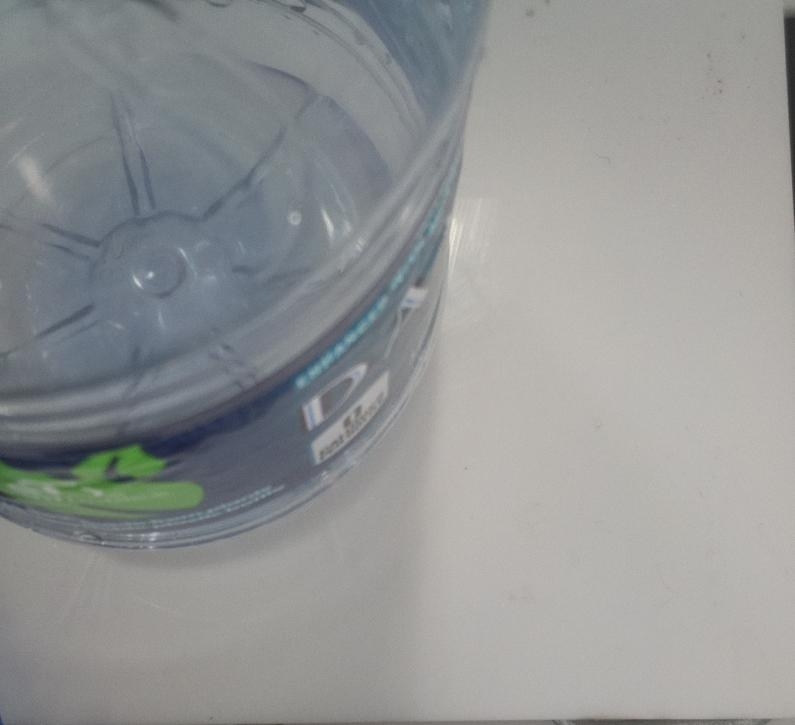
Data/Valid/plastic/plastic_new_3.jpg
