umiahmed30/RuTrash/Data/Valid/plastic/plastic_new_4.jpg

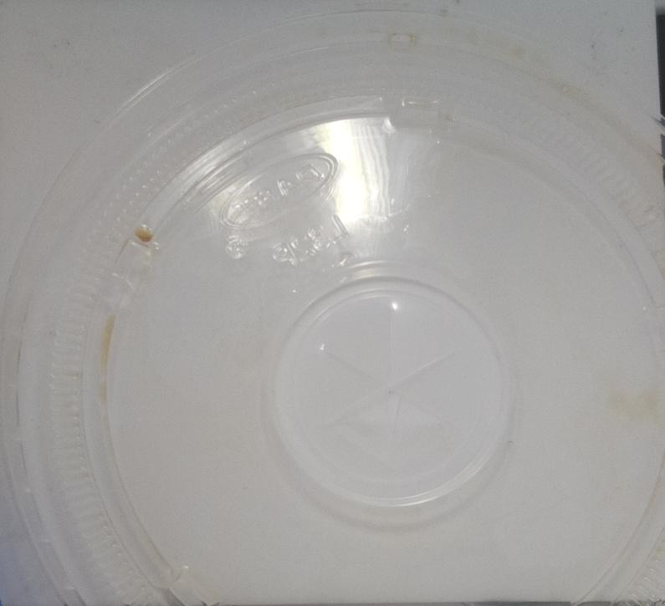
Data/Valid/plastic/plastic_new_4.jpg
