umiahmed30/RuTrash/Data/Valid/plastic/plastic_new_5.jpg

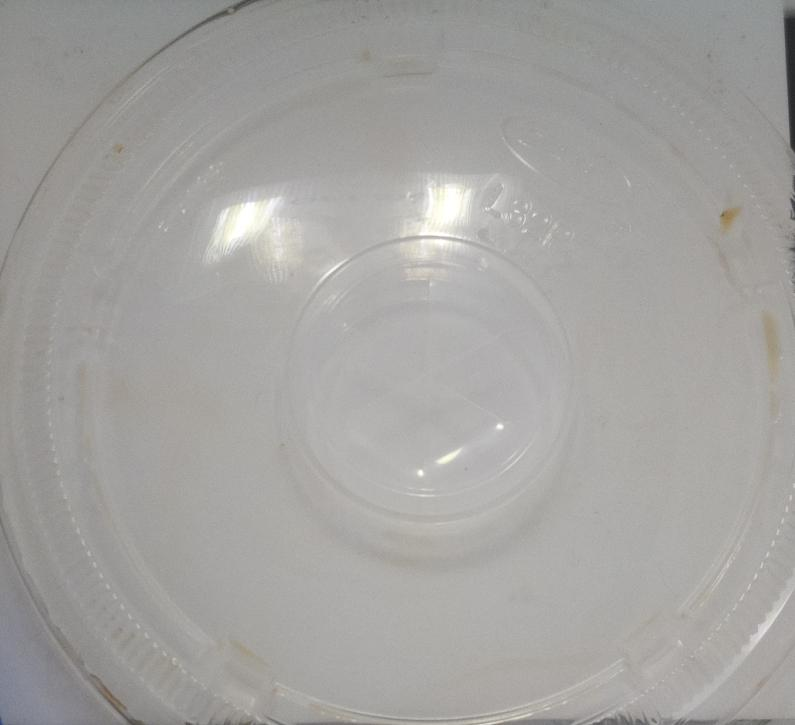
Data/Valid/plastic/plastic_new_5.jpg
