umiahmed30/RuTrash/Data/Valid/plastic/plastic_new_6.jpg

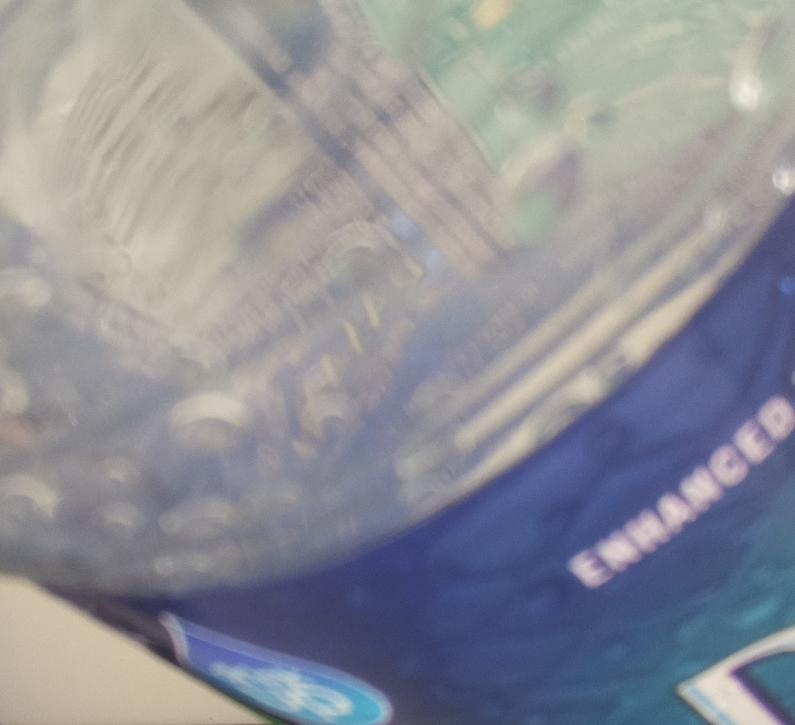
Data/Valid/plastic/plastic_new_6.jpg
