umiahmed30/RuTrash/Data/Valid/plastic/plastic_new_7.jpg

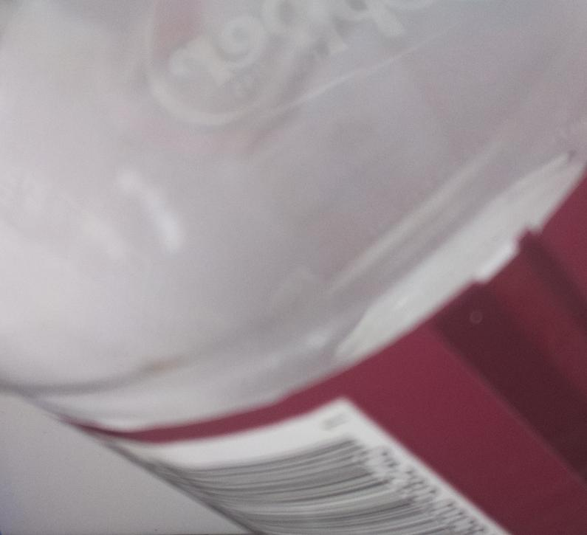
Data/Valid/plastic/plastic_new_7.jpg
