umiahmed30/RuTrash/Data/Valid/plastic/plastic_new_8.jpg

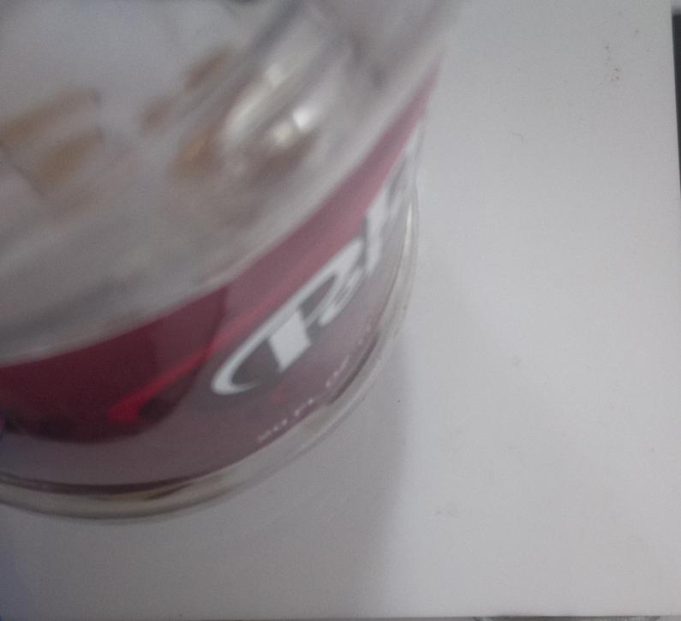
Data/Valid/plastic/plastic_new_8.jpg
