umiahmed30/RuTrash/Data/Valid/plastic/plastic_new_9.jpg

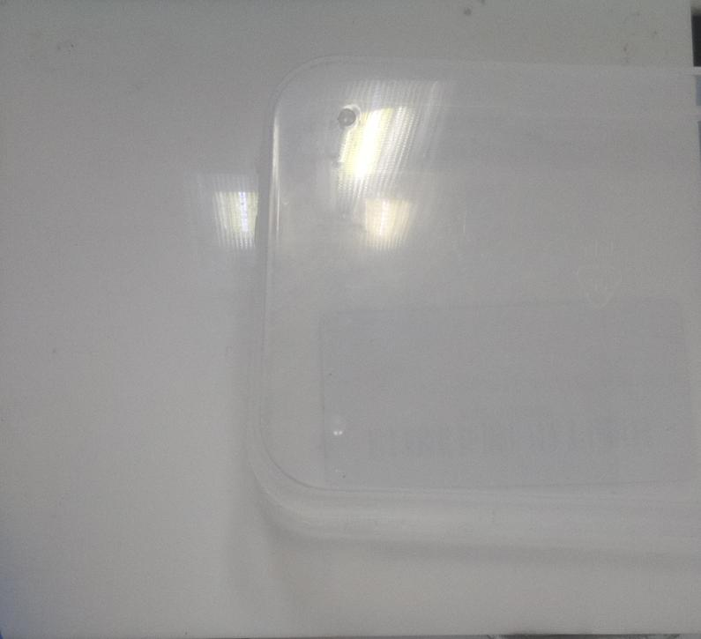
Data/Valid/plastic/plastic_new_9.jpg
