umiahmed30/RuTrash/Data/Valid/plastic/plastic_new_11.jpg

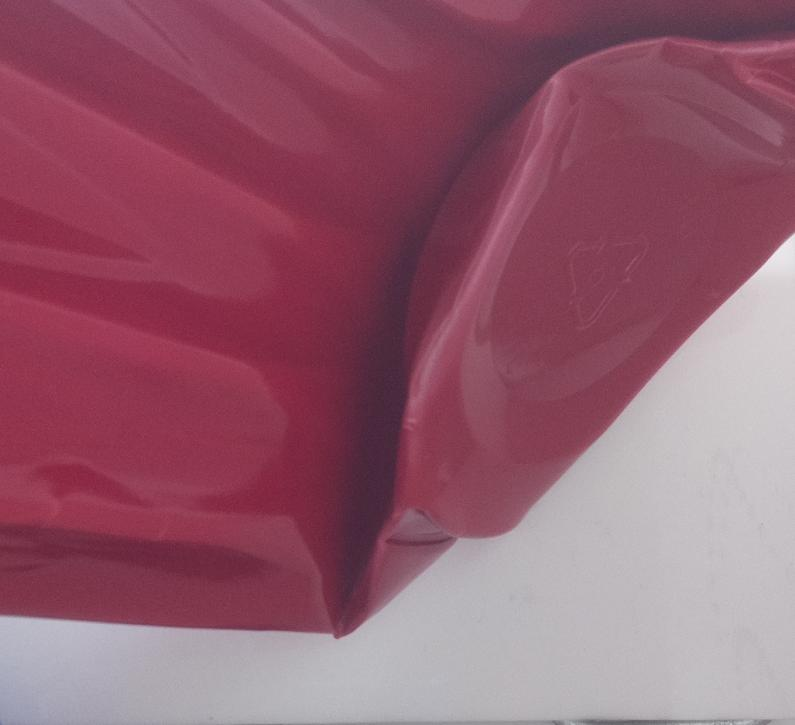
Data/Valid/plastic/plastic_new_11.jpg
