umiahmed30/RuTrash/Data/Valid/plastic/plastic_new_12.jpg

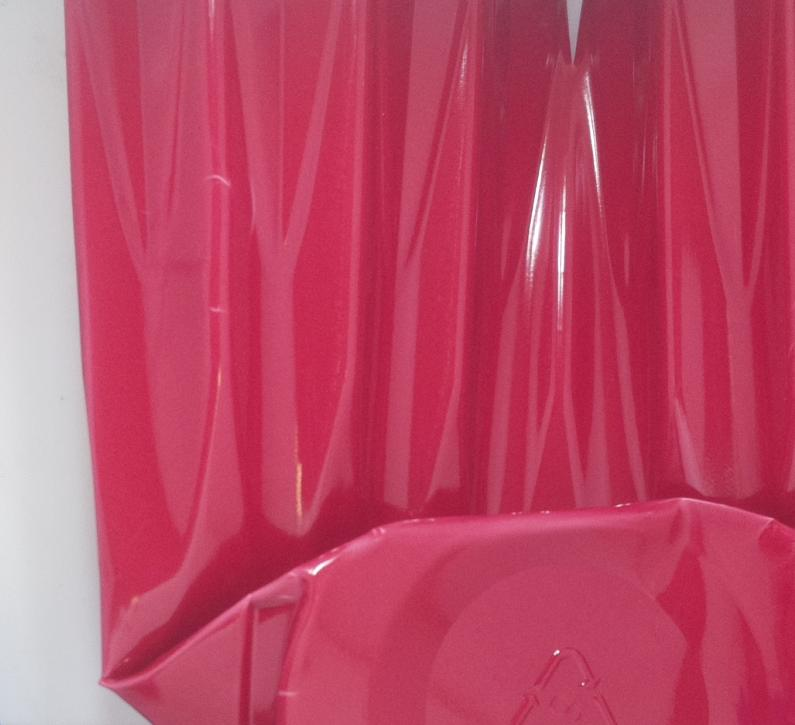
Data/Valid/plastic/plastic_new_12.jpg
