umiahmed30/RuTrash/Data/Valid/plastic/plastic_new_13.jpg

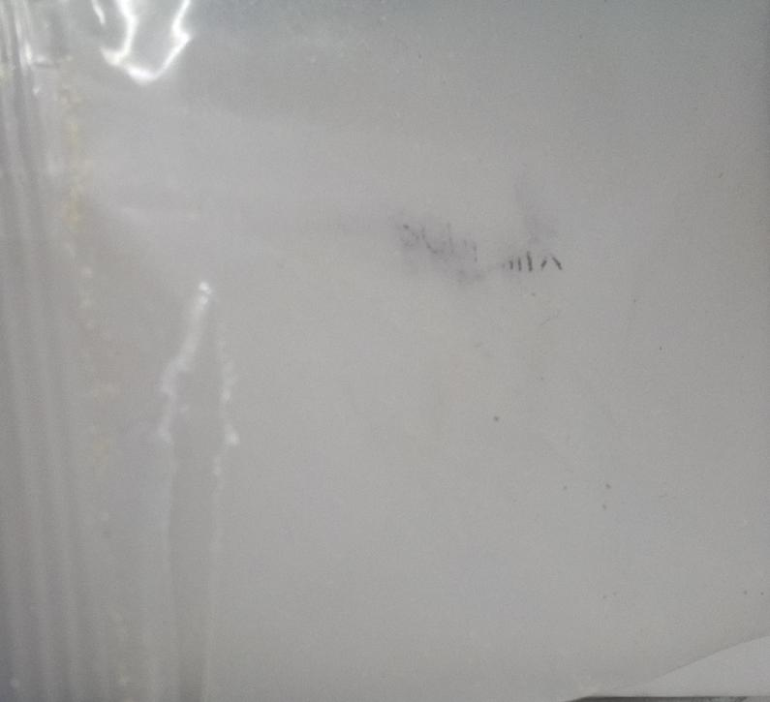
Data/Valid/plastic/plastic_new_13.jpg
