umiahmed30/RuTrash/Data/Valid/plastic/plastic_new_14.jpg

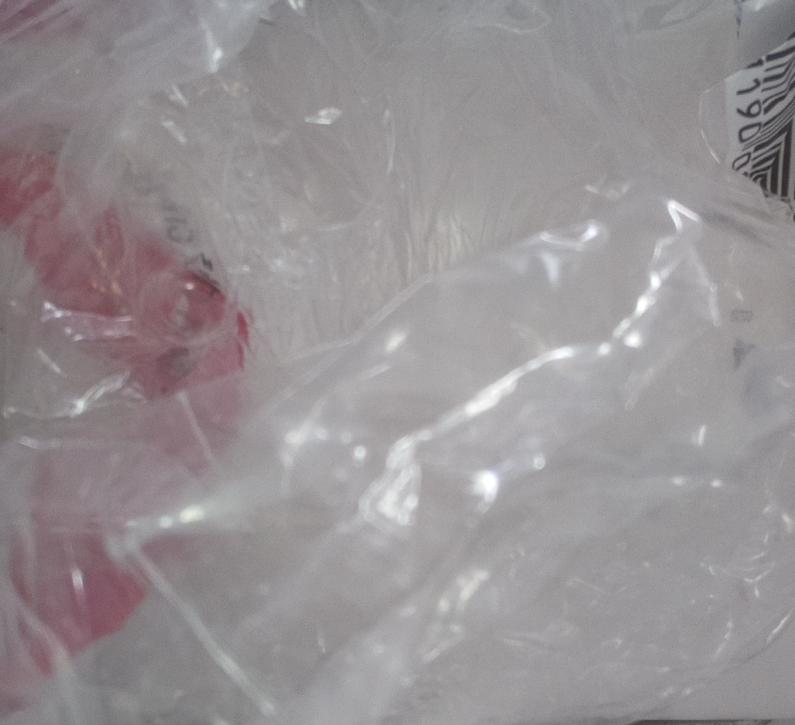
Data/Valid/plastic/plastic_new_14.jpg
