umiahmed30/RuTrash/Data/Valid/plastic/plastic_new_15.jpg

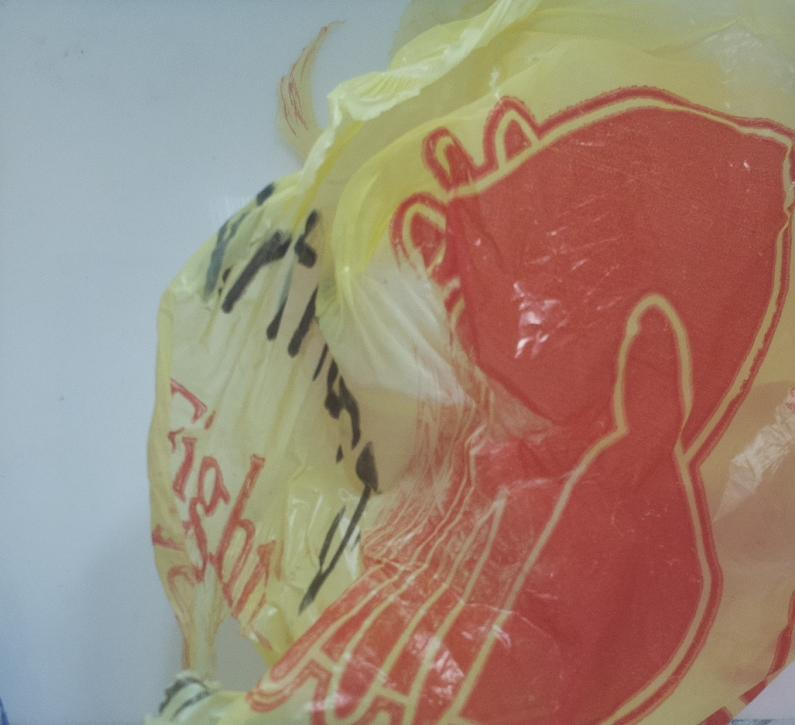
Data/Valid/plastic/plastic_new_15.jpg
