umiahmed30/RuTrash/Data/Valid/plastic/plastic_new_16.jpg

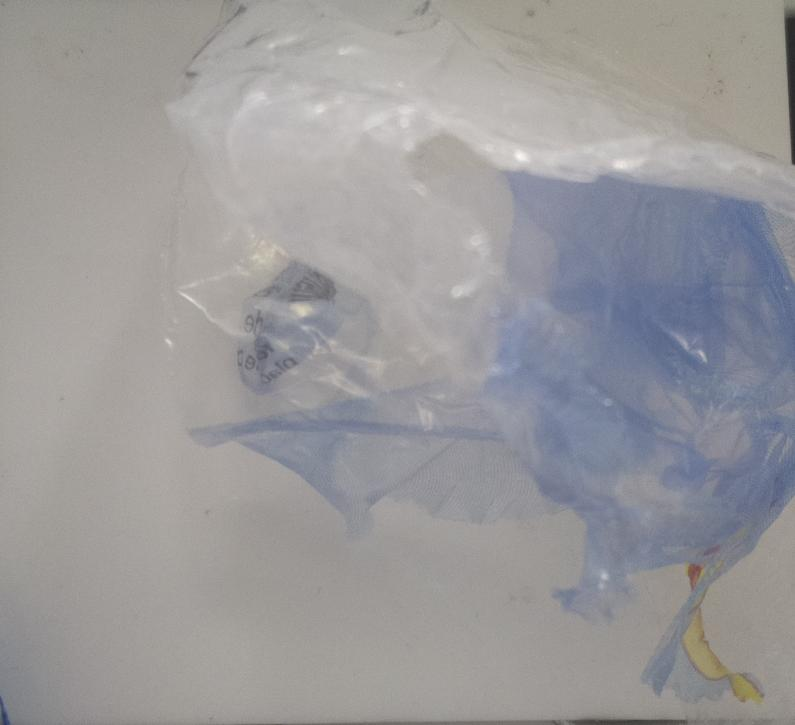
Data/Valid/plastic/plastic_new_16.jpg
