umiahmed30/RuTrash/Data/Valid/plastic/plastic_new_17.jpg

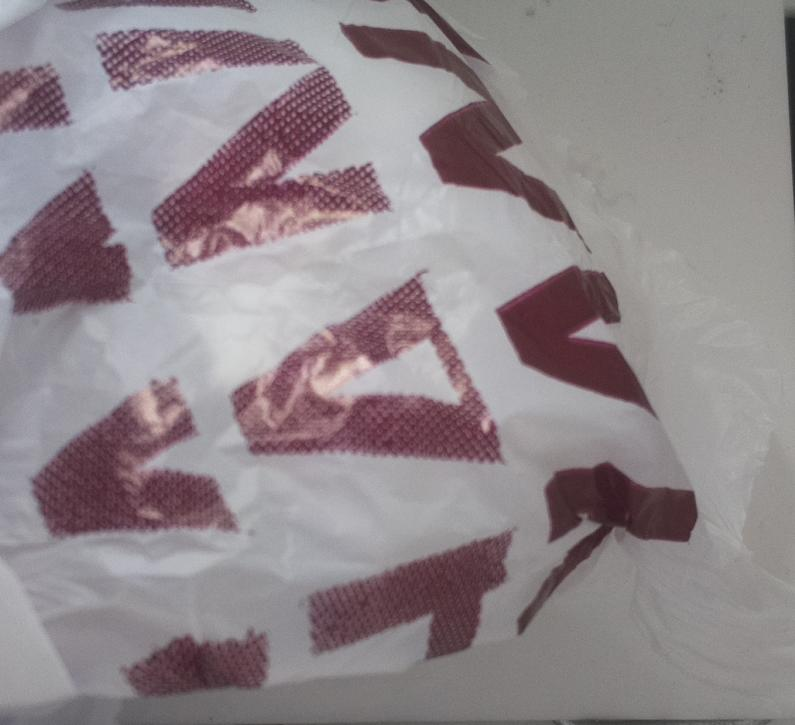
Data/Valid/plastic/plastic_new_17.jpg
