umiahmed30/RuTrash/Data/Valid/plastic/plastic_new_18.jpg

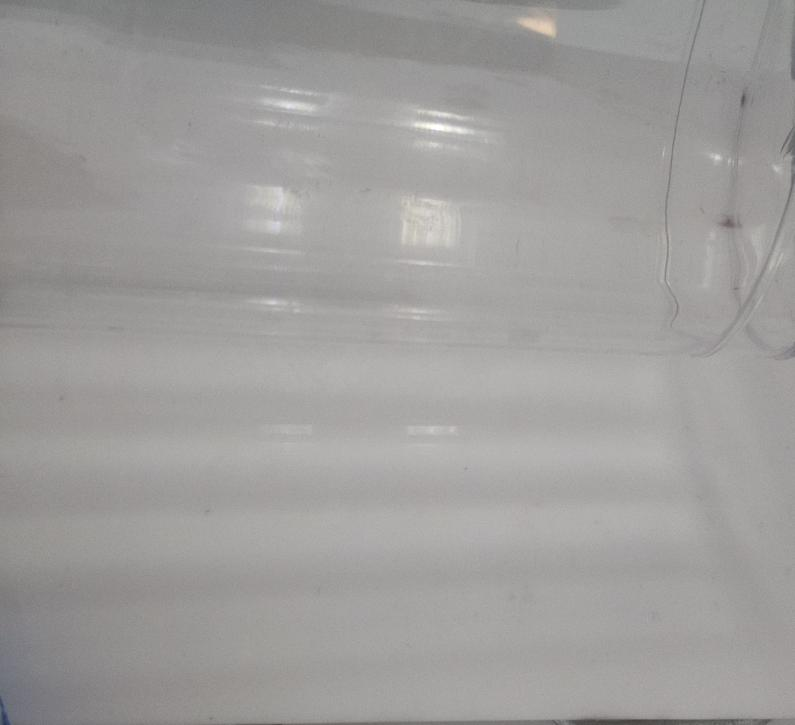
Data/Valid/plastic/plastic_new_18.jpg
