umiahmed30/RuTrash/Data/Valid/plastic/plastic_new_19.jpg

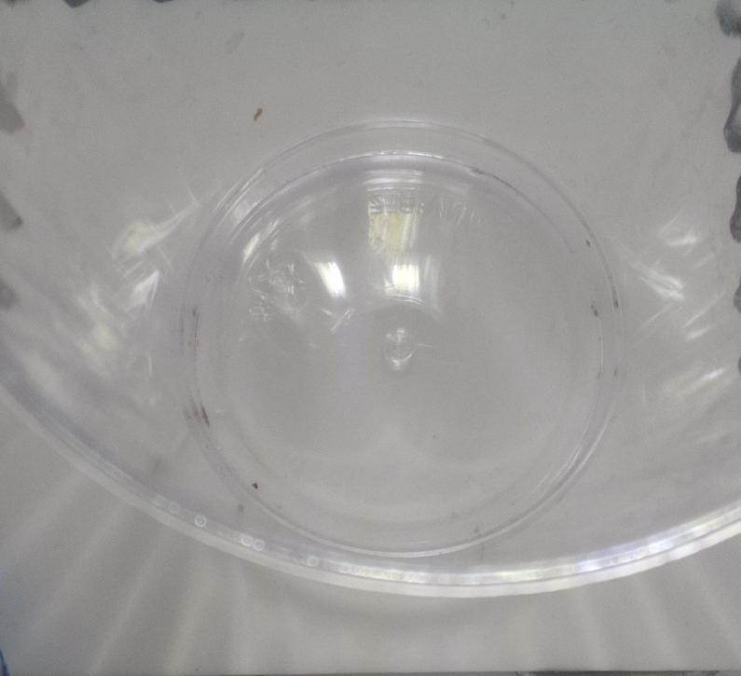
Data/Valid/plastic/plastic_new_19.jpg
