umiahmed30/RuTrash/Data/Valid/plastic/plastic_new_20.jpg

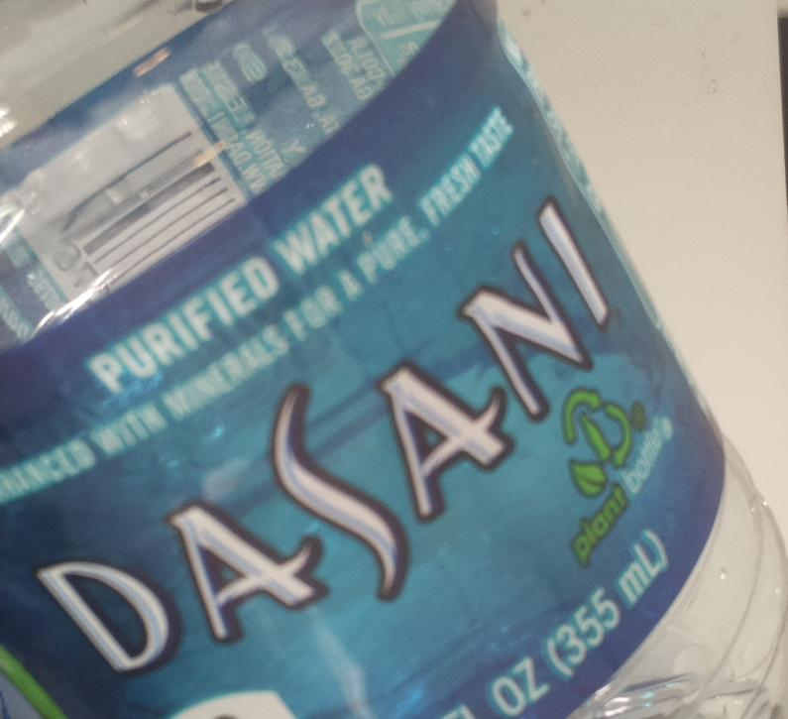
Data/Valid/plastic/plastic_new_20.jpg
