umiahmed30/RuTrash/Data/Valid/plastic/plastic_new_21.jpg

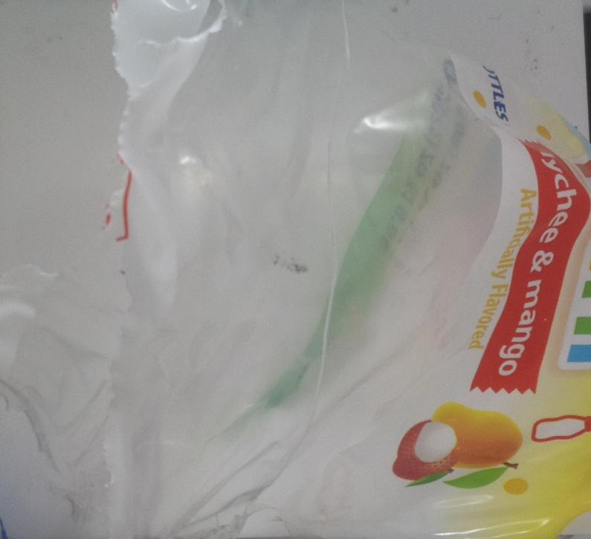
Data/Valid/plastic/plastic_new_21.jpg
