umiahmed30/RuTrash/Data/Valid/plastic/plastic_new_22.jpg

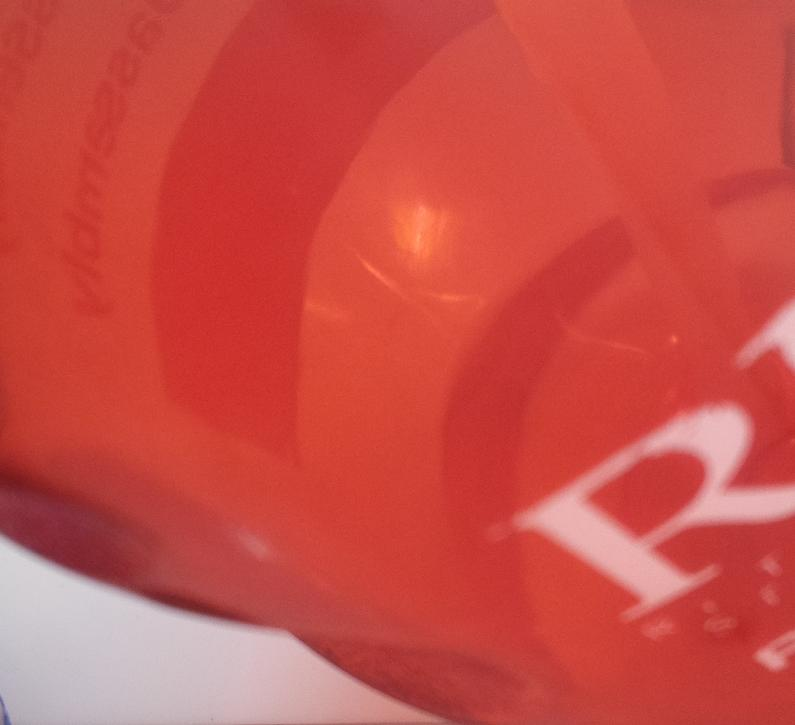
Data/Valid/plastic/plastic_new_22.jpg
