umiahmed30/RuTrash/Data/Valid/plastic/plastic_new_23.jpg

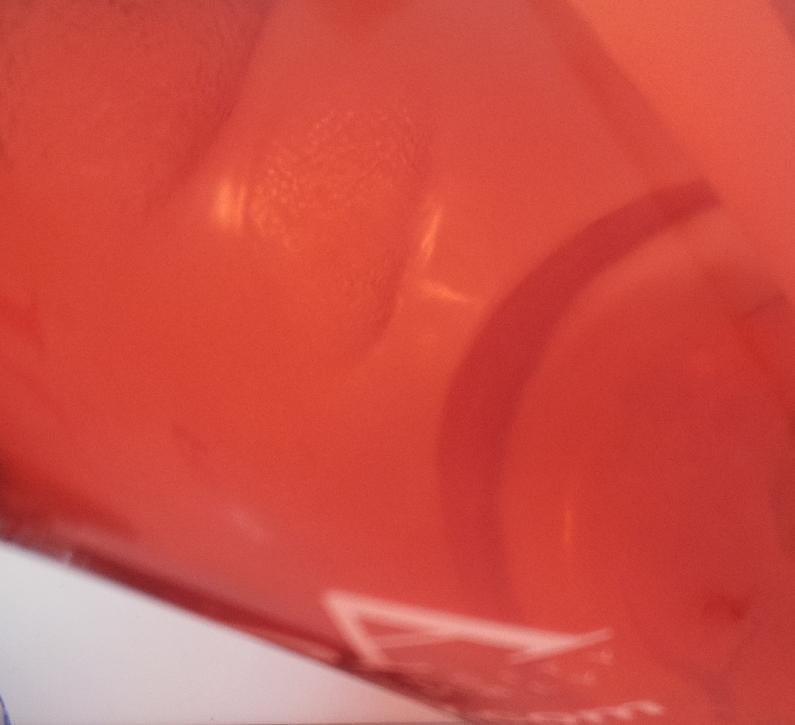
Data/Valid/plastic/plastic_new_23.jpg
