umiahmed30/RuTrash/Data/Valid/plastic/plastic_new_24.jpg

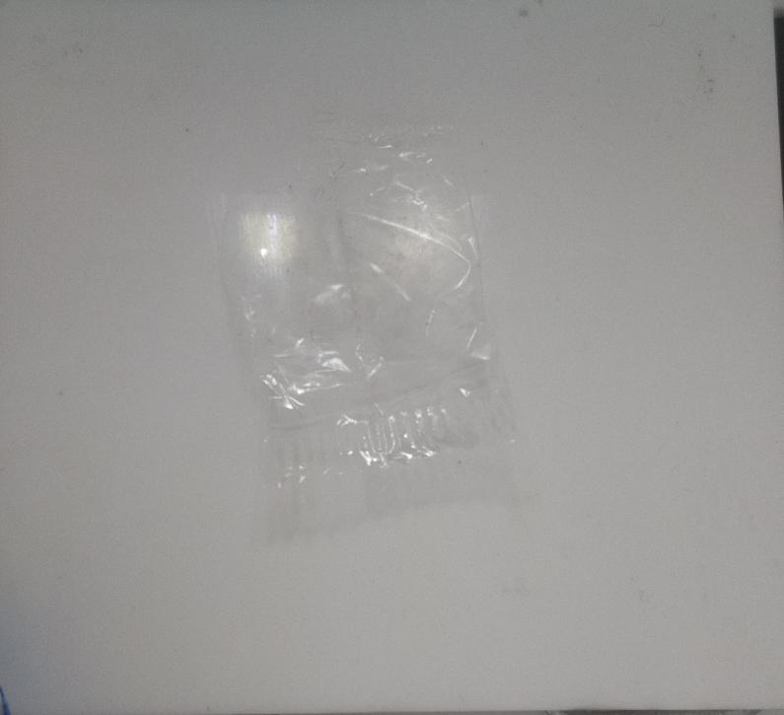
Data/Valid/plastic/plastic_new_24.jpg
