umiahmed30/RuTrash/Data/Valid/plastic/plastic_new_26.jpg

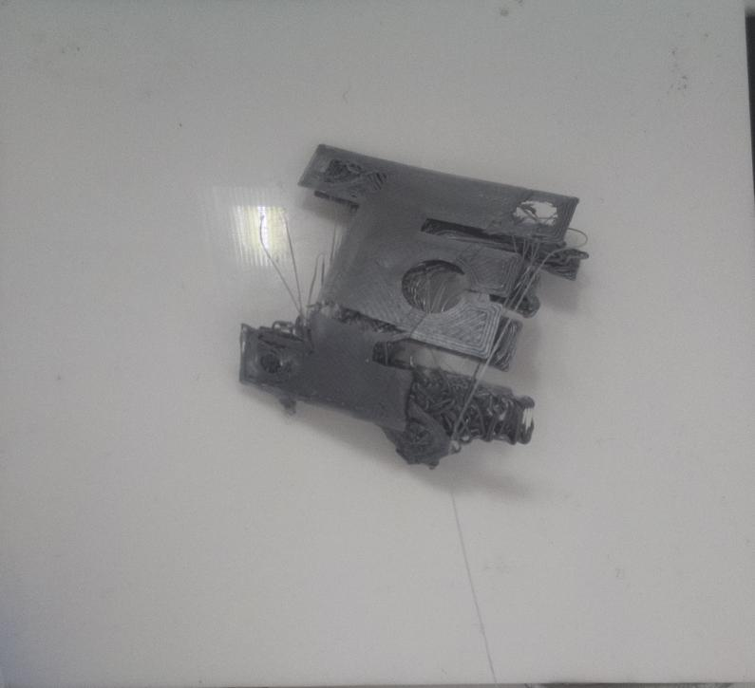
Data/Valid/plastic/plastic_new_26.jpg
