umiahmed30/RuTrash/Data/Valid/plastic/plastic_new_27.jpg

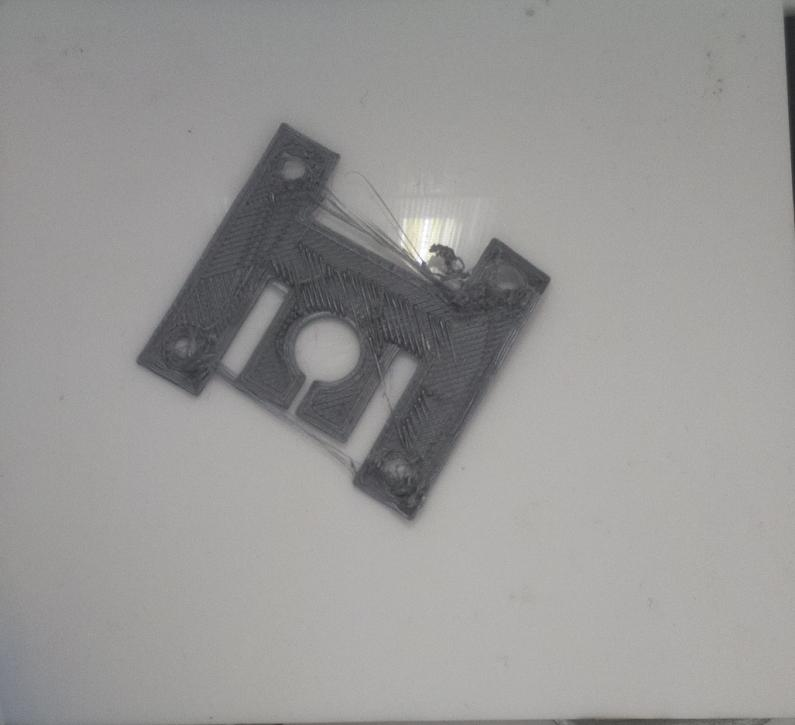
Data/Valid/plastic/plastic_new_27.jpg
