umiahmed30/RuTrash/Data/Valid/plastic/plastic_new_29.jpg

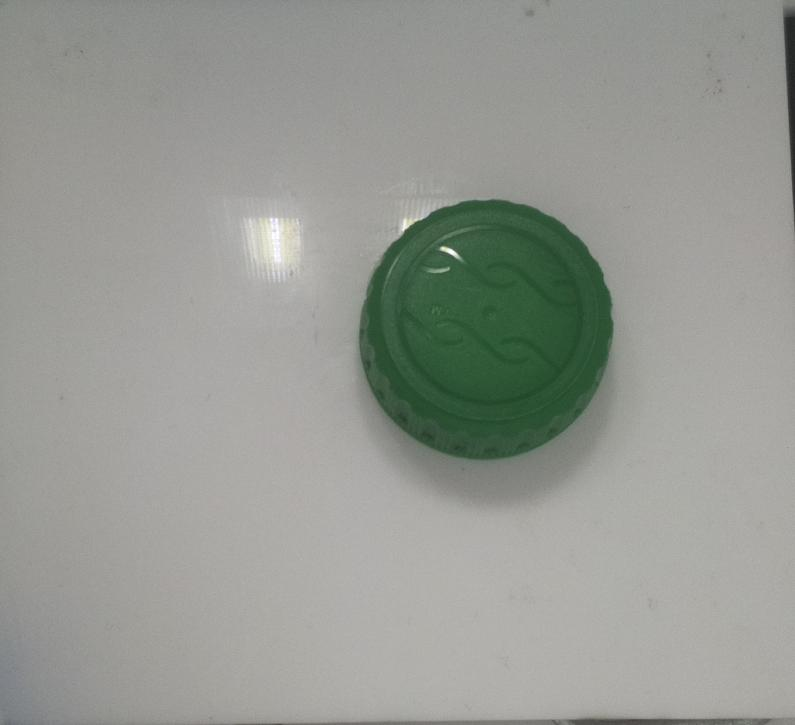
Data/Valid/plastic/plastic_new_29.jpg
