umiahmed30/RuTrash/Data/Valid/plastic/plastic_new_30.jpg

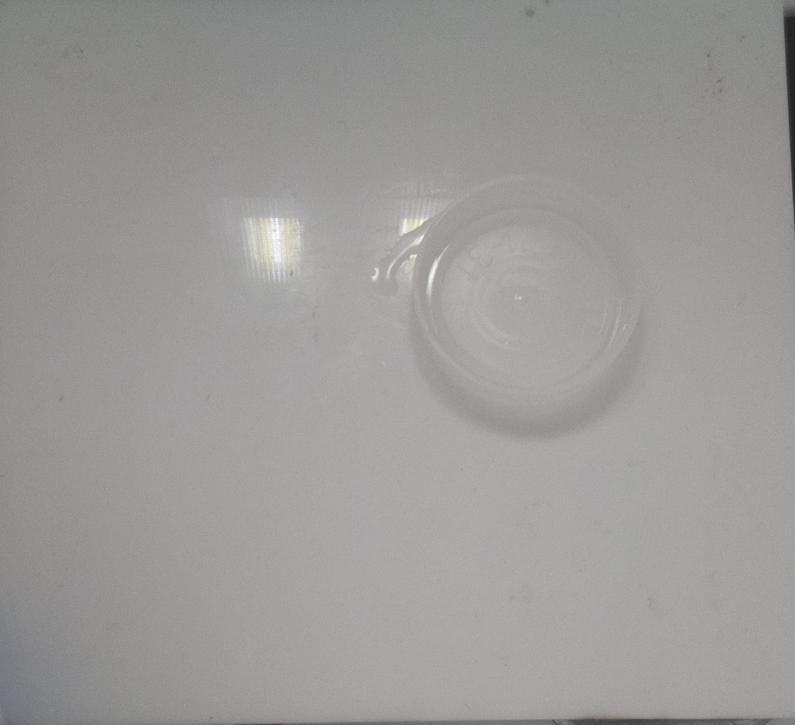
Data/Valid/plastic/plastic_new_30.jpg
