umiahmed30/RuTrash/Data/Valid/plastic/plastic_new_31.jpg

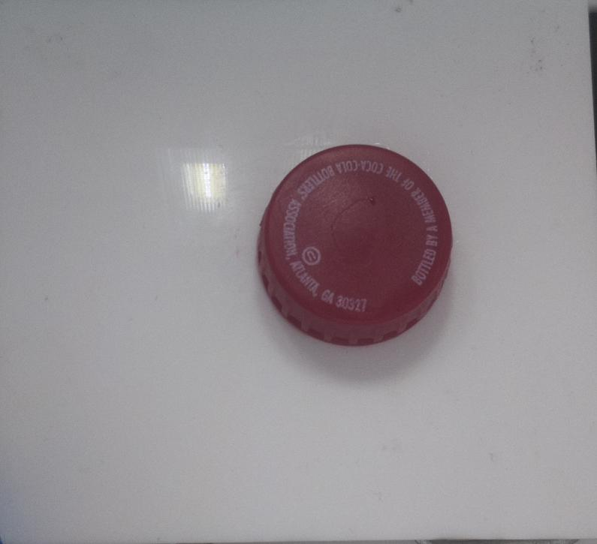
Data/Valid/plastic/plastic_new_31.jpg
