umiahmed30/RuTrash/Data/Valid/trash/trash_new_0.jpg

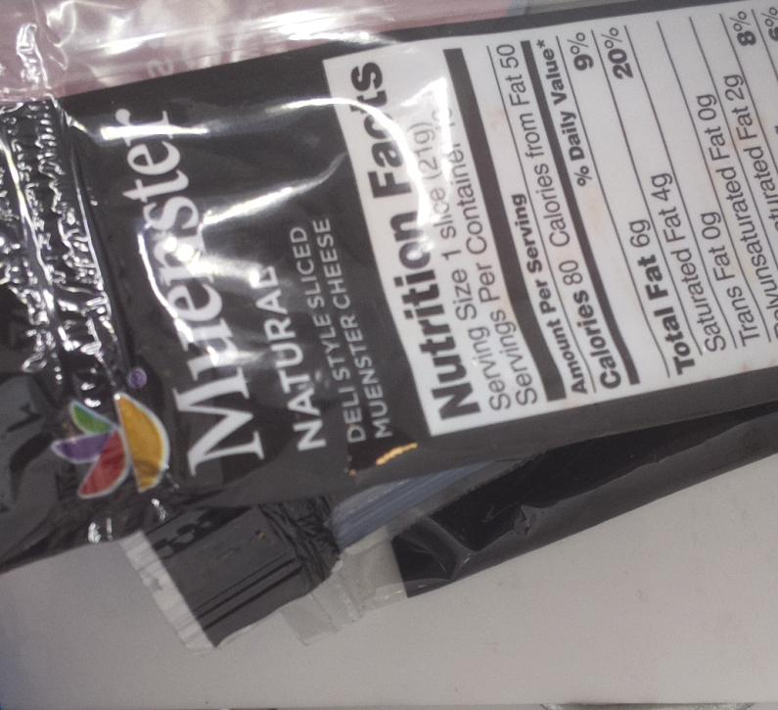
Data/Valid/trash/trash_new_0.jpg
