umiahmed30/RuTrash/Data/Valid/trash/trash_new_1.jpg

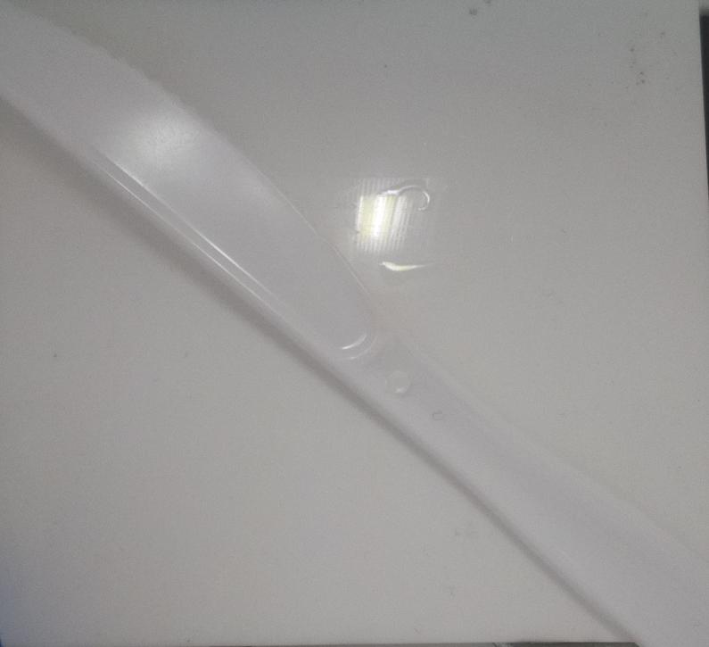
Data/Valid/trash/trash_new_1.jpg
