umiahmed30/RuTrash/Data/Valid/trash/trash_new_2.jpg

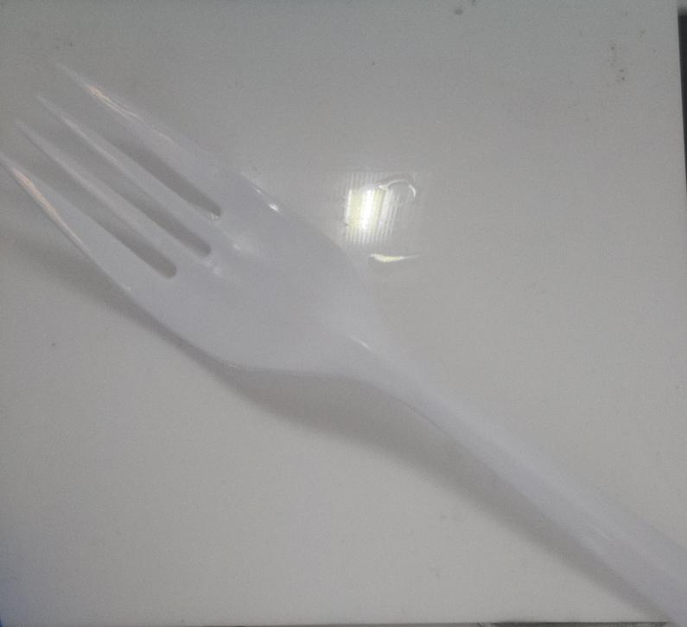
Data/Valid/trash/trash_new_2.jpg
