umiahmed30/RuTrash/Data/Valid/trash/trash_new_3.jpg

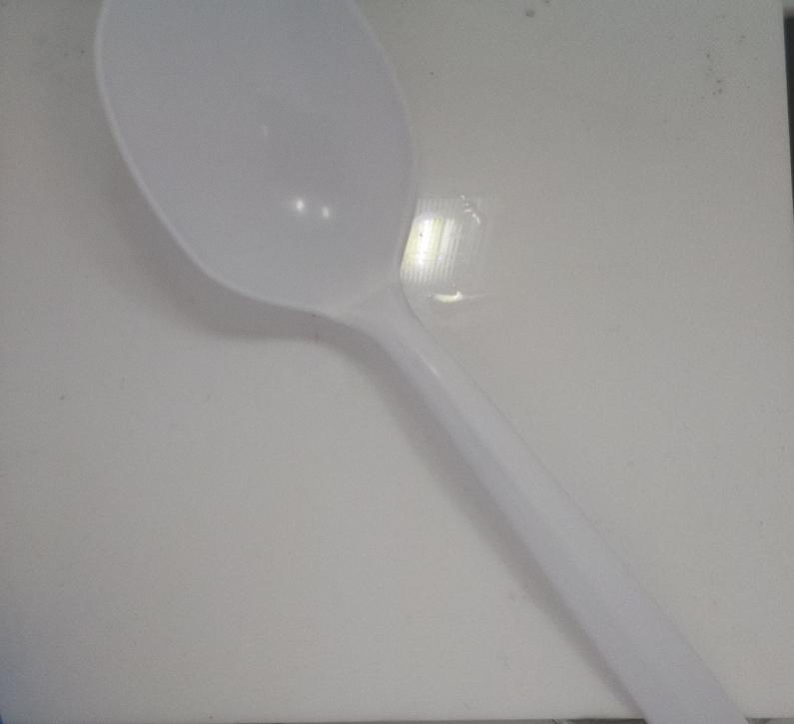
Data/Valid/trash/trash_new_3.jpg
