umiahmed30/RuTrash/Data/Valid/trash/trash_new_4.jpg

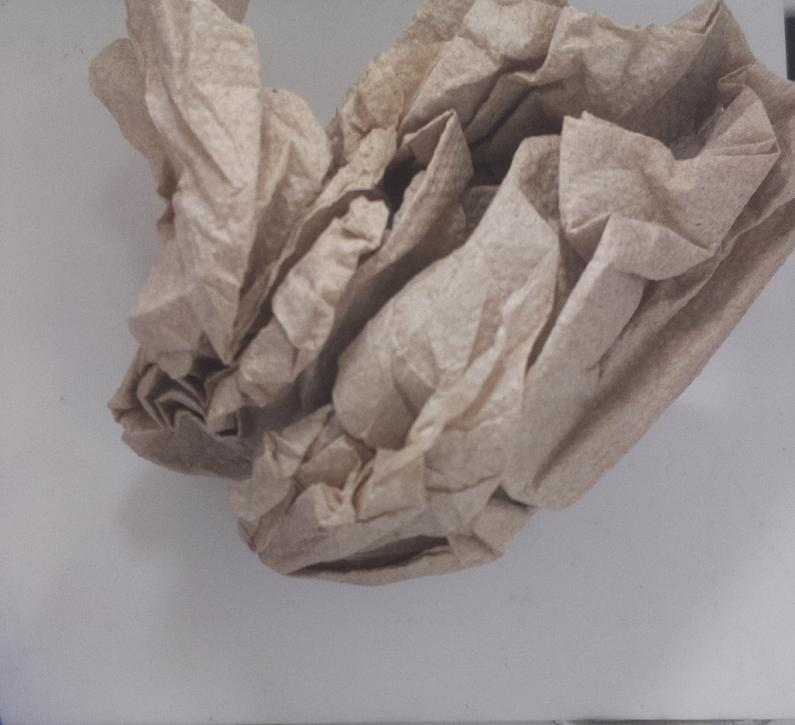
Data/Valid/trash/trash_new_4.jpg
