umiahmed30/RuTrash/Data/Valid/trash/trash_new_5.jpg

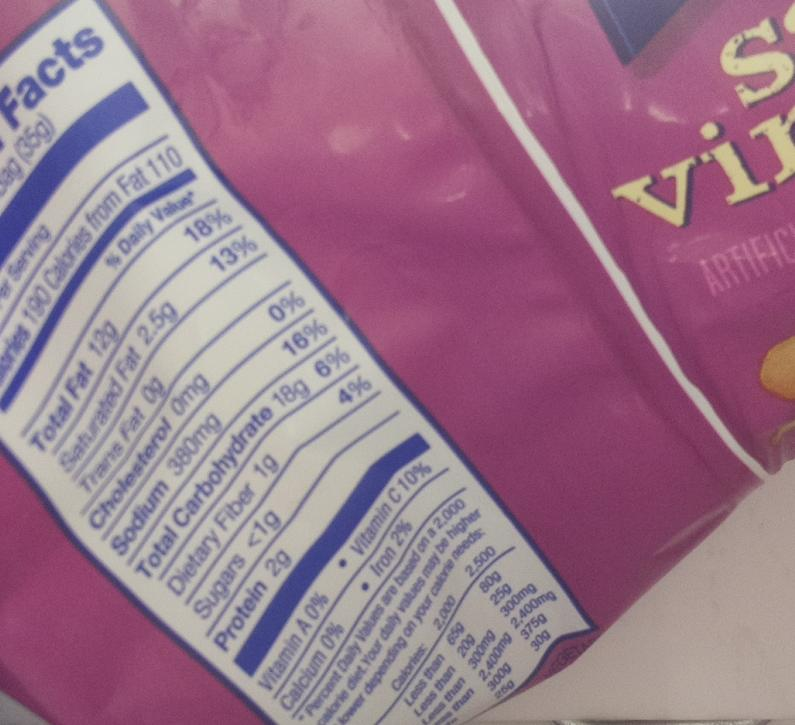
Data/Valid/trash/trash_new_5.jpg
