umiahmed30/RuTrash/Data/Valid/trash/trash_new_6.jpg

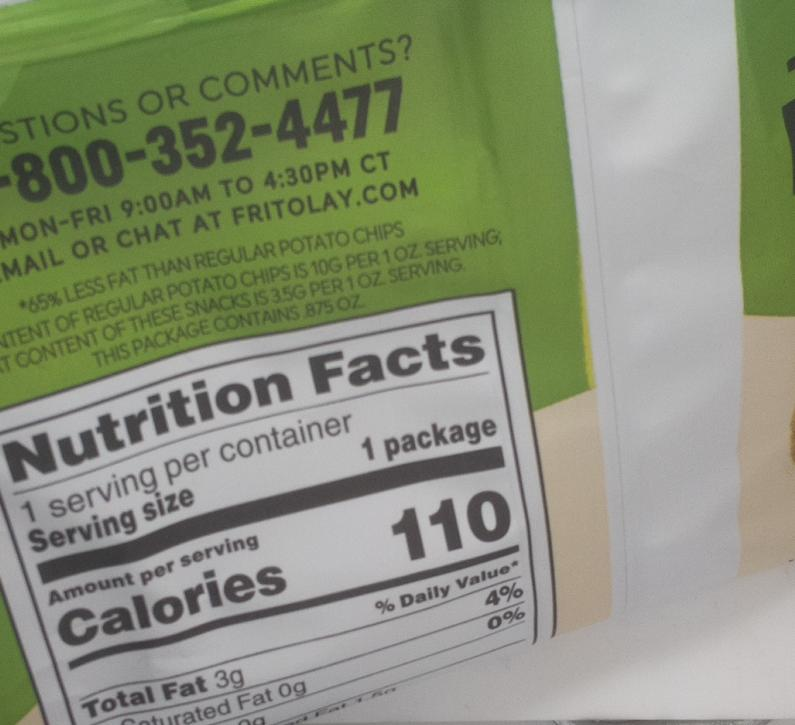
Data/Valid/trash/trash_new_6.jpg
