umiahmed30/RuTrash/Data/Valid/trash/trash_new_7.jpg

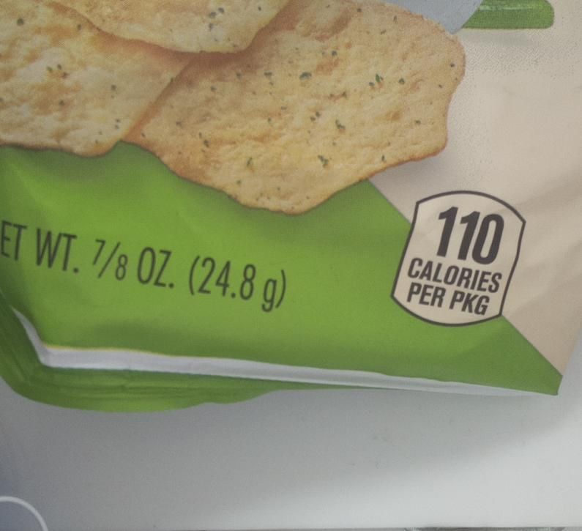
Data/Valid/trash/trash_new_7.jpg
