umiahmed30/RuTrash/Data/Valid/trash/trash_new_8.jpg

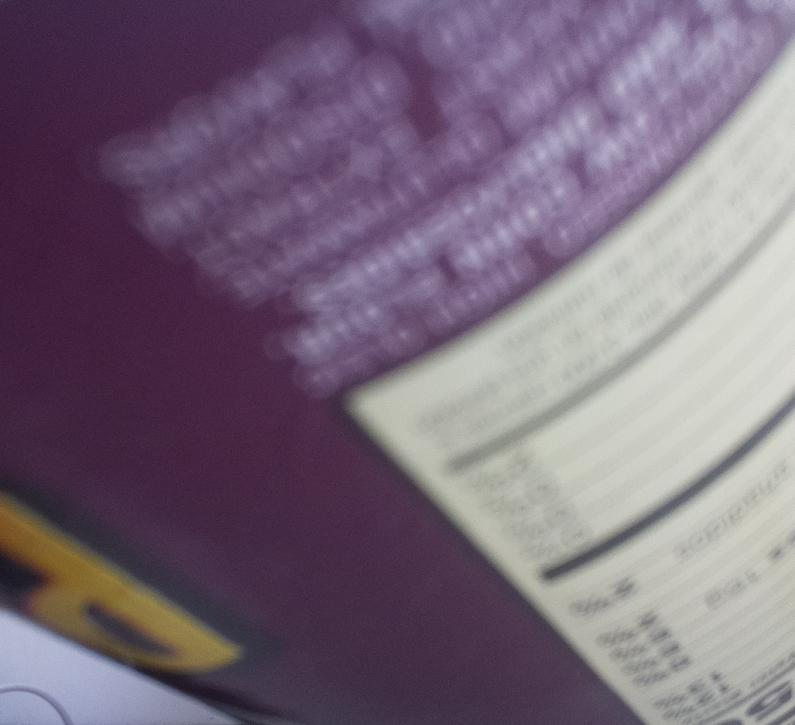
Data/Valid/trash/trash_new_8.jpg
