umiahmed30/RuTrash/Data/Valid/trash/trash_new_9.jpg

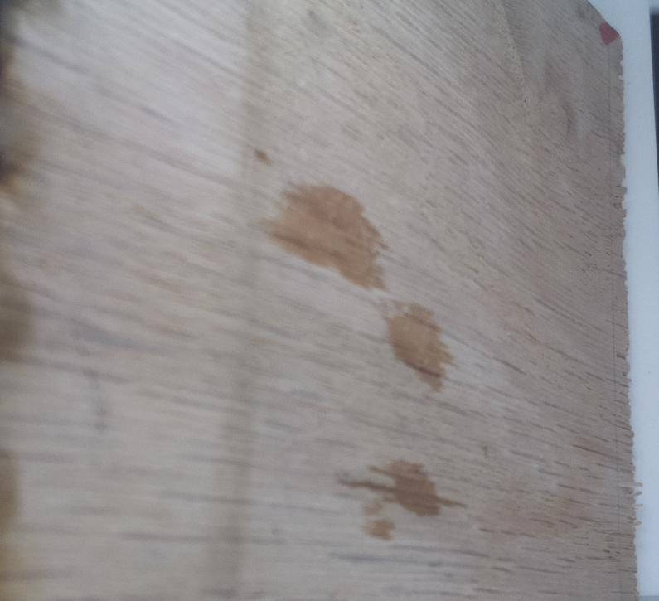
Data/Valid/trash/trash_new_9.jpg
