umiahmed30/RuTrash/Data/Valid/trash/trash_new_10.jpg

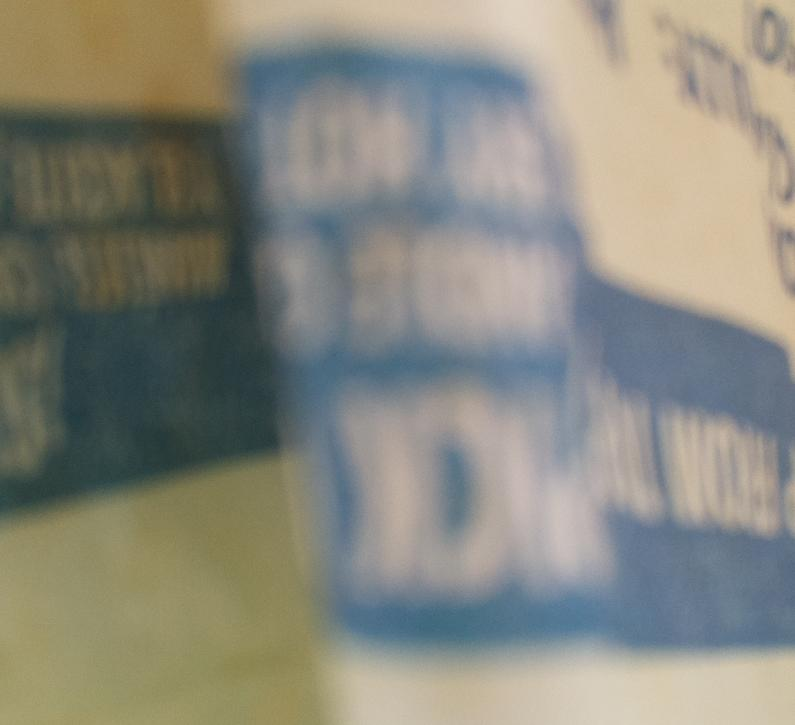
Data/Valid/trash/trash_new_10.jpg
