umiahmed30/RuTrash/Data/Valid/trash/trash_new_11.jpg

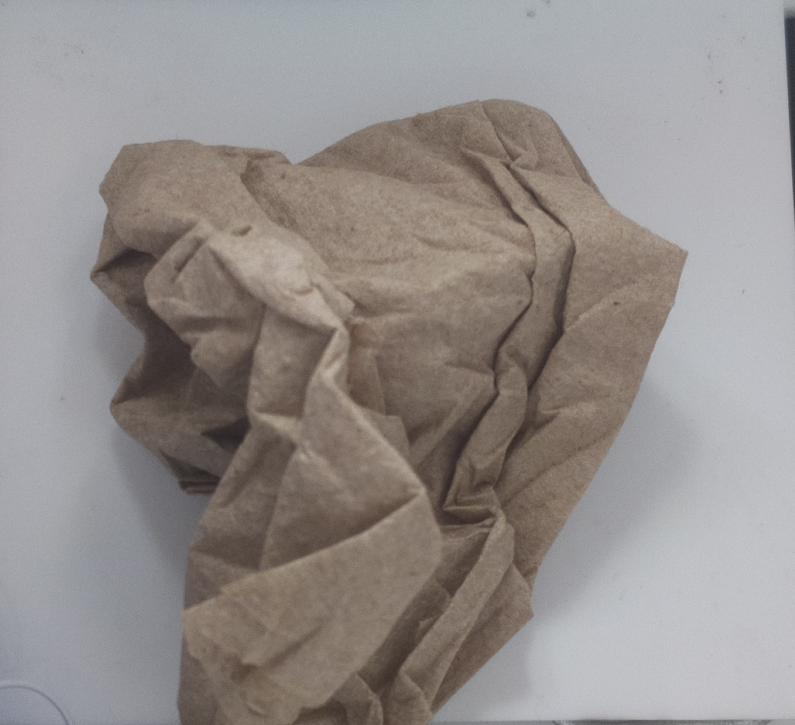
Data/Valid/trash/trash_new_11.jpg
