umiahmed30/RuTrash/Data/Valid/trash/trash_new_12.jpg

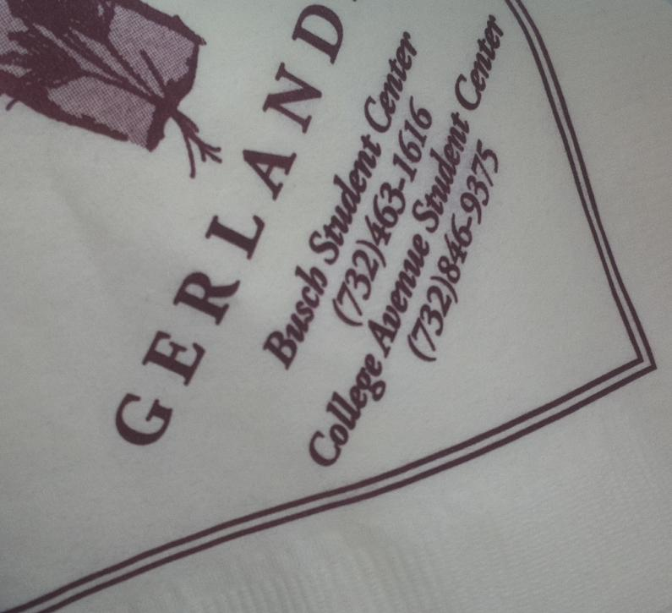
Data/Valid/trash/trash_new_12.jpg
