umiahmed30/RuTrash/Data/Valid/trash/trash_new_13.jpg

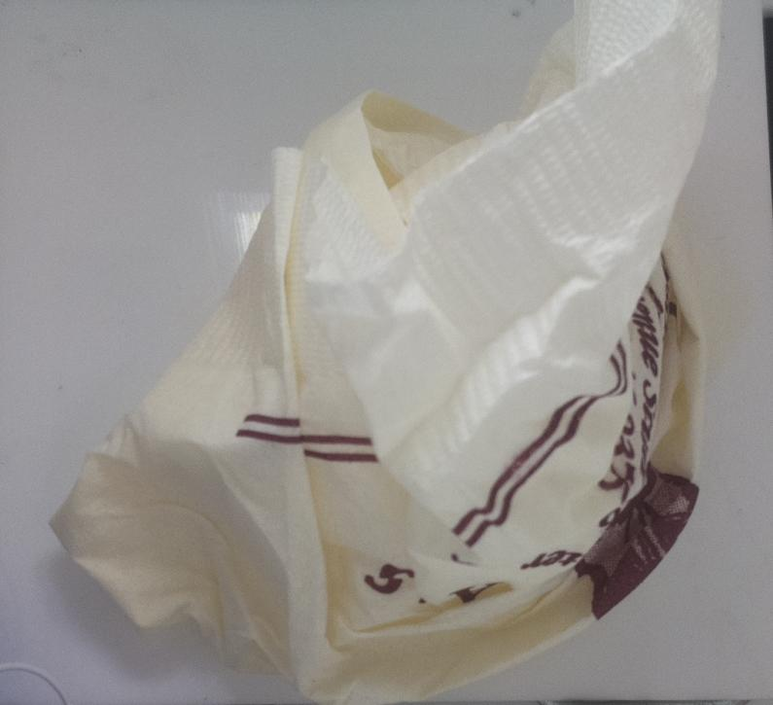
Data/Valid/trash/trash_new_13.jpg
