umiahmed30/RuTrash/Data/Valid/trash/trash_new_14.jpg

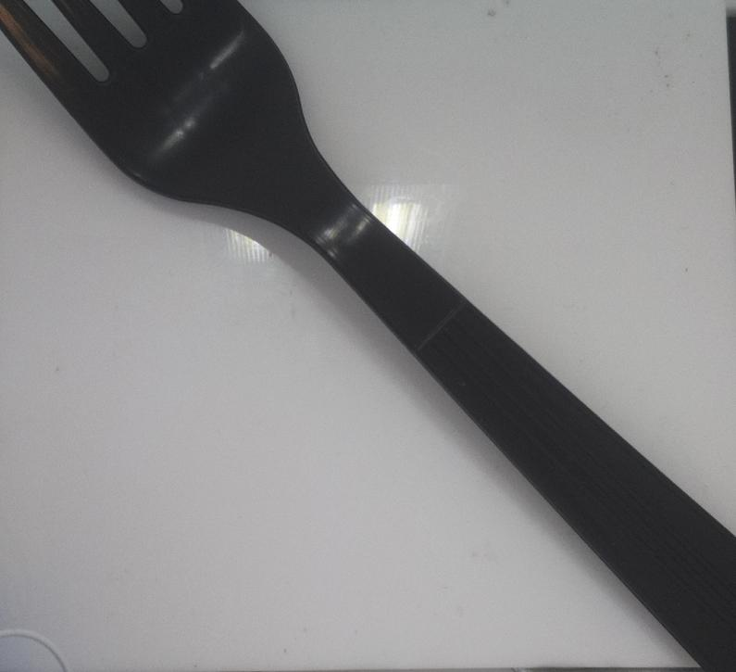
Data/Valid/trash/trash_new_14.jpg
