umiahmed30/RuTrash/Data/Valid/trash/trash_new_15.jpg

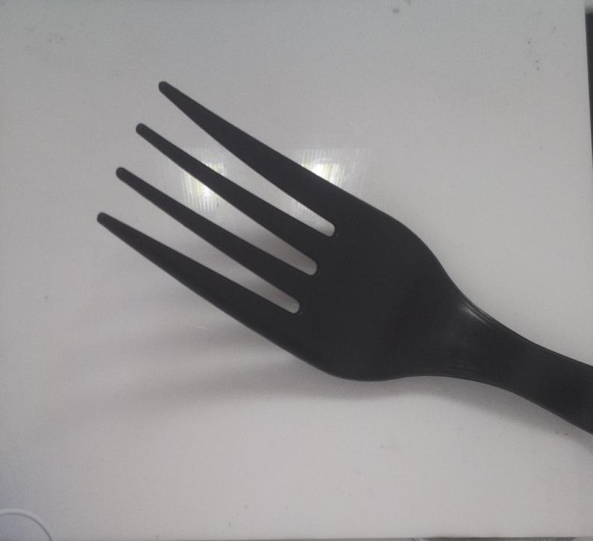
Data/Valid/trash/trash_new_15.jpg
