umiahmed30/RuTrash/Data/Valid/trash/trash_new_16.jpg

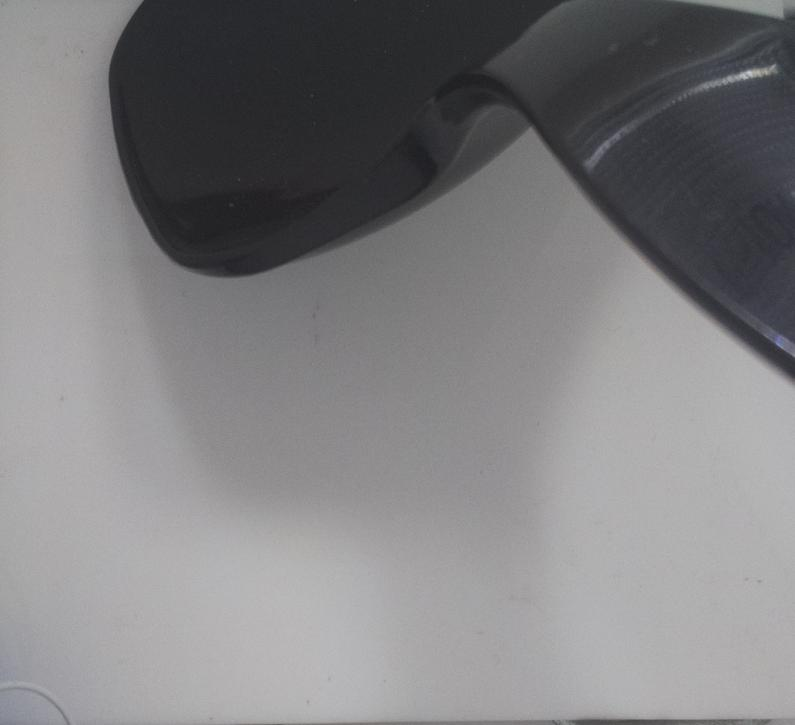
Data/Valid/trash/trash_new_16.jpg
