umiahmed30/RuTrash/Data/Valid/trash/trash_new_17.jpg

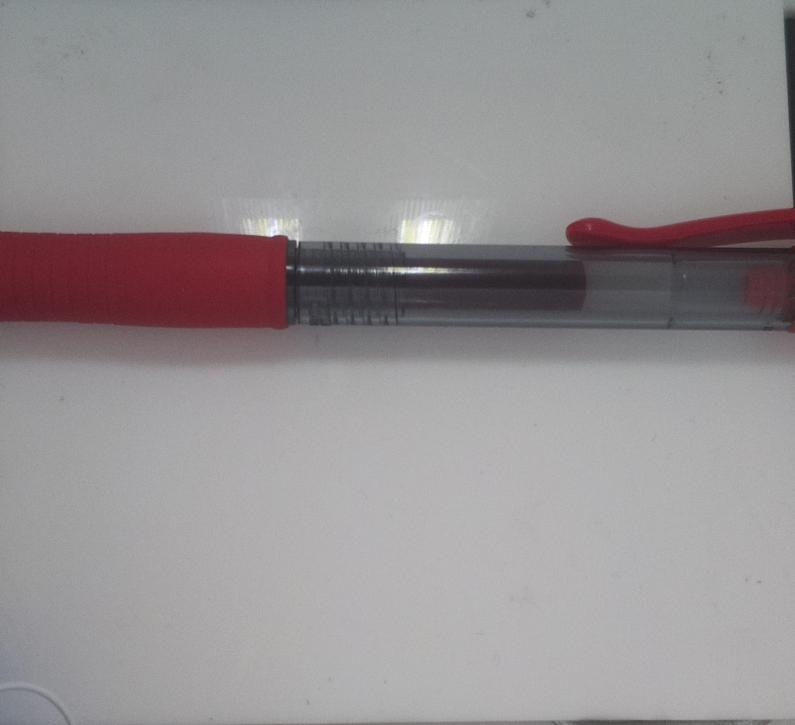
Data/Valid/trash/trash_new_17.jpg
