umiahmed30/RuTrash/Data/Valid/trash/trash_new_18.jpg

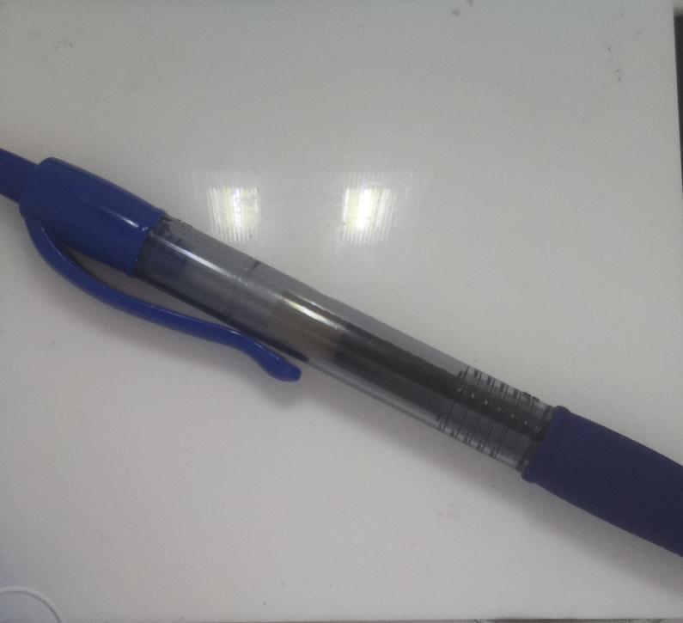
Data/Valid/trash/trash_new_18.jpg
