umiahmed30/RuTrash/Data/Valid/trash/trash_new_19.jpg

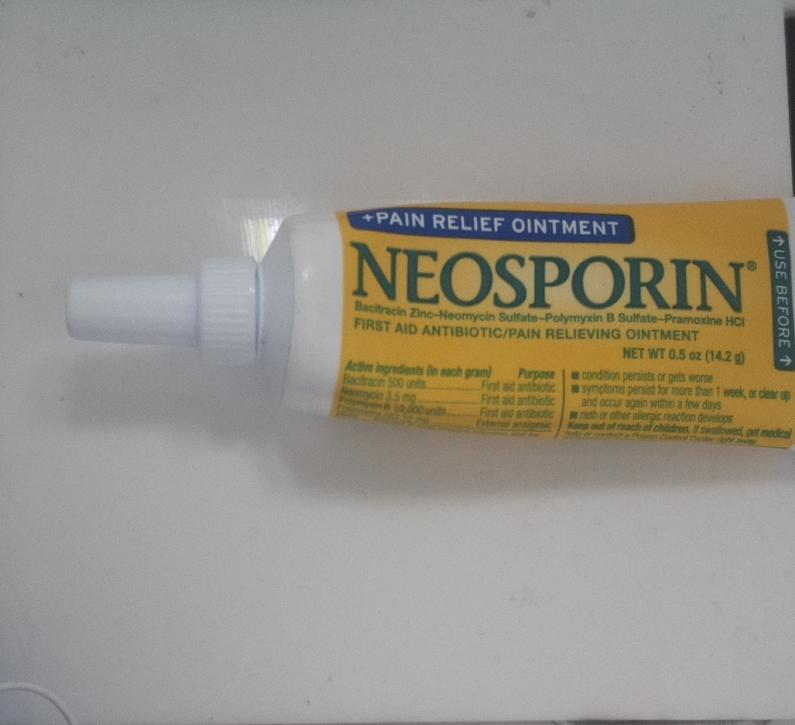
Data/Valid/trash/trash_new_19.jpg
