umiahmed30/RuTrash/Data/Valid/trash/trash_new_20.jpg

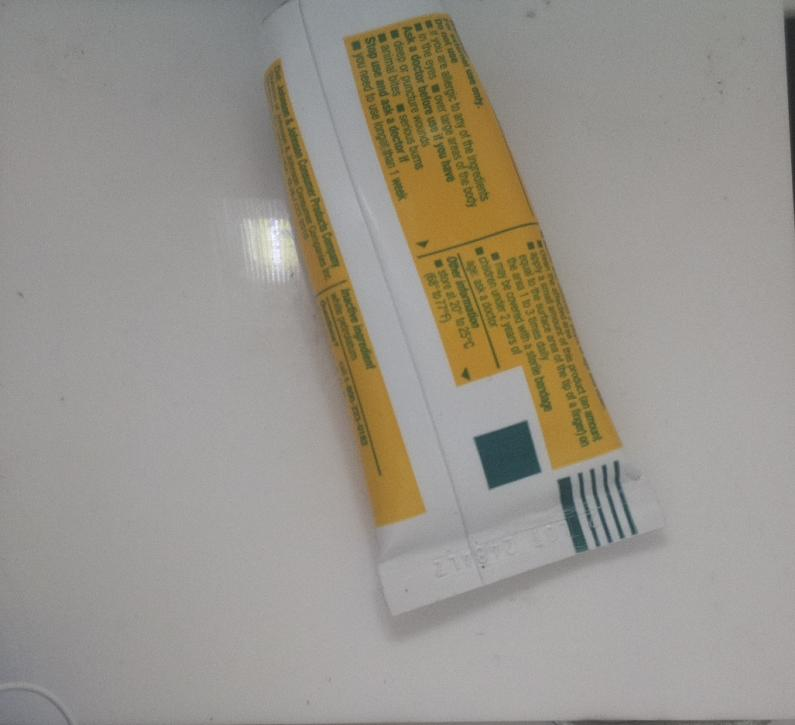
Data/Valid/trash/trash_new_20.jpg
