umiahmed30/RuTrash/Data/Valid/trash/trash_new_21.jpg

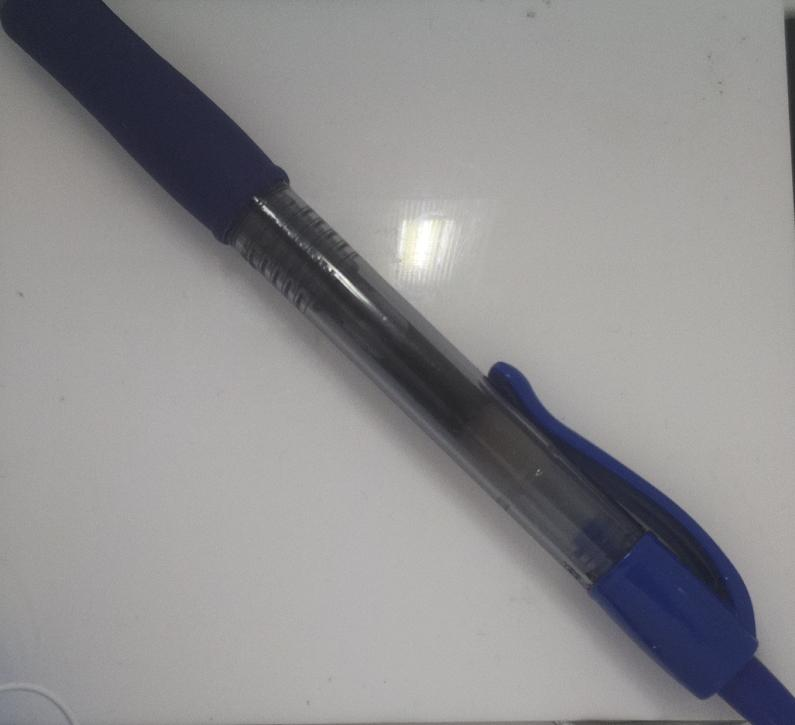
Data/Valid/trash/trash_new_21.jpg
