umiahmed30/RuTrash/Data/Valid/trash/trash_new_22.jpg

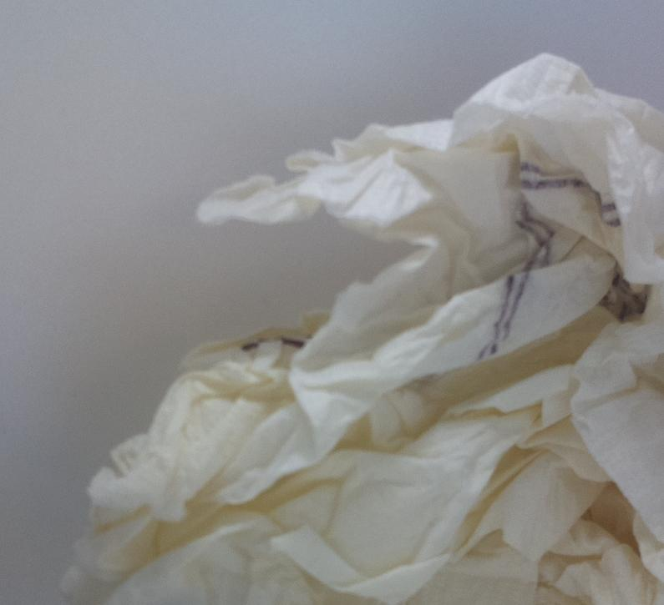
Data/Valid/trash/trash_new_22.jpg
