umiahmed30/RuTrash/Data/Valid/trash/trash_new_23.jpg

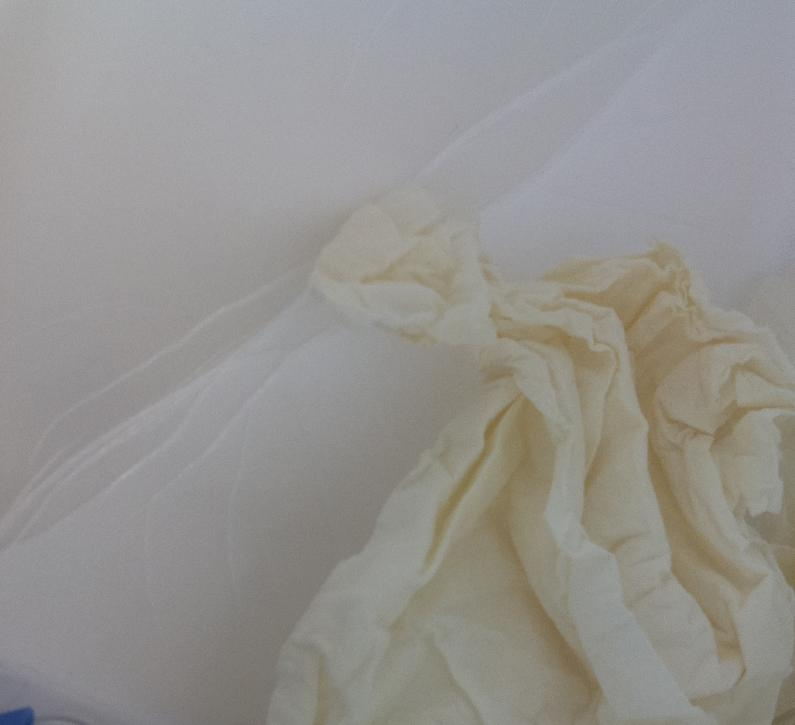
Data/Valid/trash/trash_new_23.jpg
