umiahmed30/RuTrash/Data/Valid/trash/trash_new_24.jpg

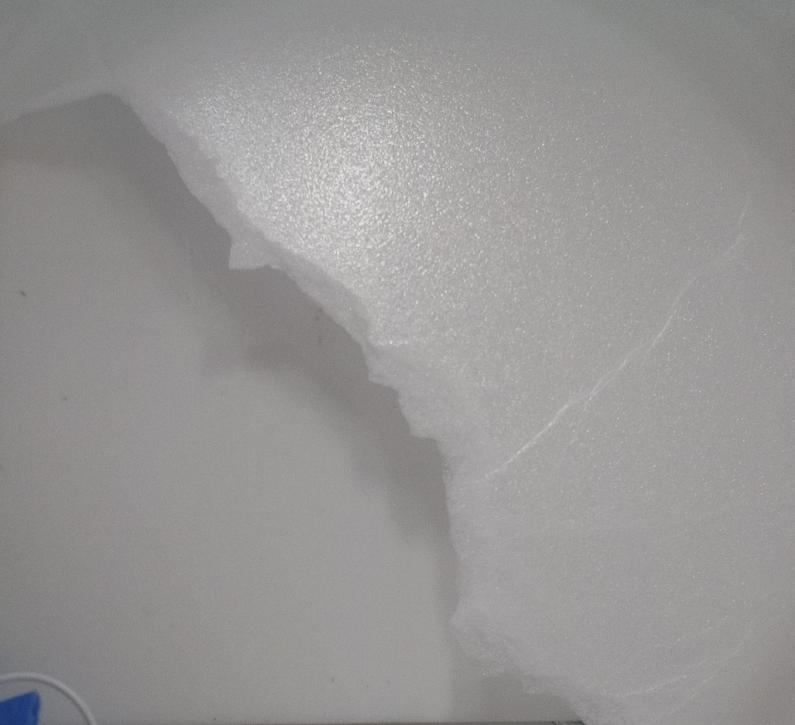
Data/Valid/trash/trash_new_24.jpg
