umiahmed30/RuTrash/Data/Valid/trash/trash_new_25.jpg

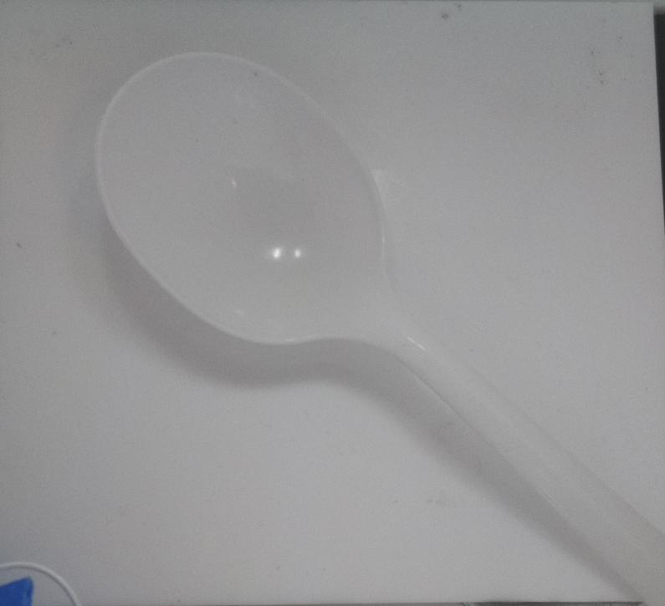
Data/Valid/trash/trash_new_25.jpg
