umiahmed30/RuTrash/Data/Valid/trash/trash_new_26.jpg

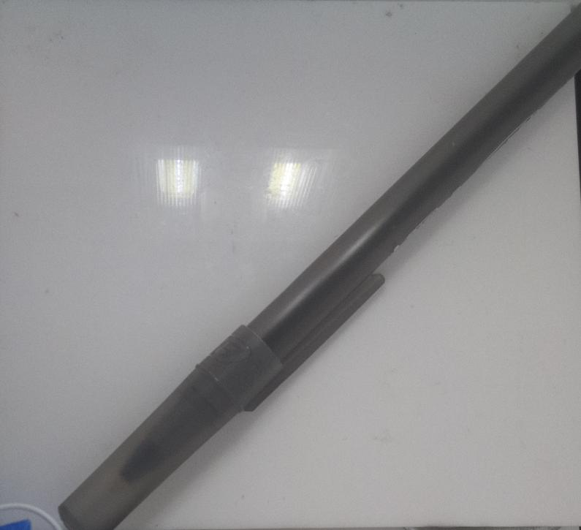
Data/Valid/trash/trash_new_26.jpg
