umiahmed30/RuTrash/Data/Valid/trash/trash_new_27.jpg

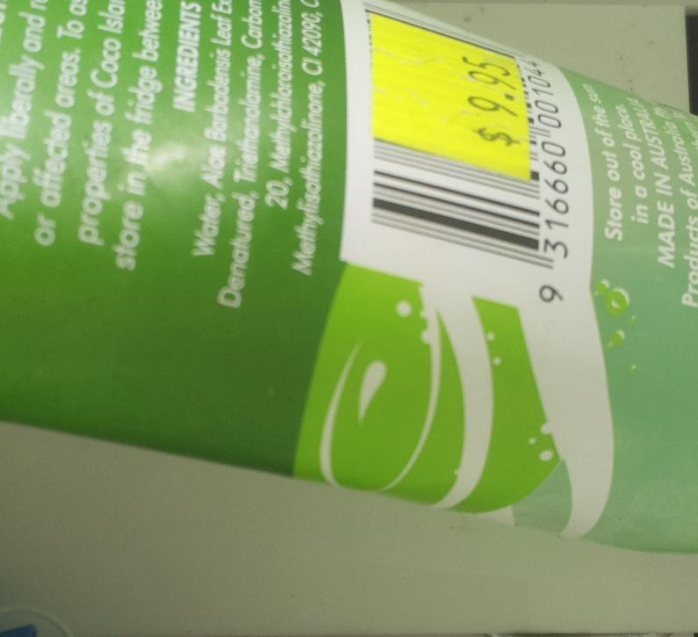
Data/Valid/trash/trash_new_27.jpg
