umiahmed30/RuTrash/Data/Valid/trash/trash_new_29.jpg

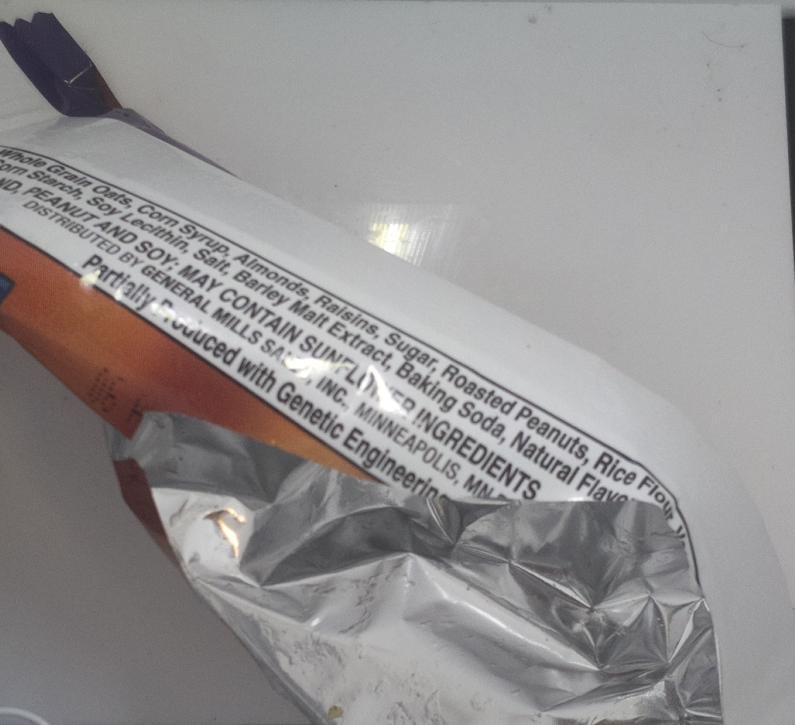
Data/Valid/trash/trash_new_29.jpg
