umiahmed30/RuTrash/Data/Valid/trash/trash_new_30.jpg

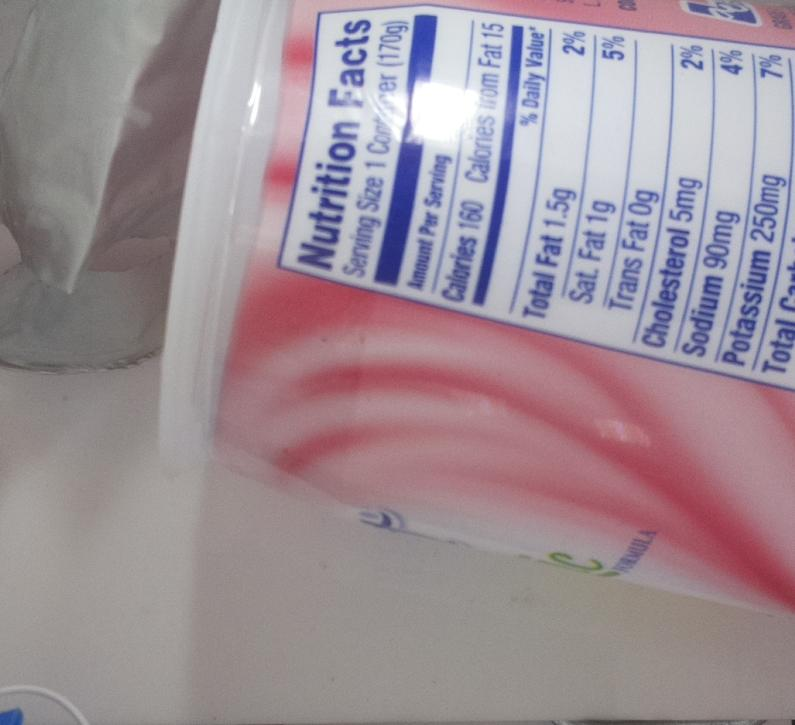
Data/Valid/trash/trash_new_30.jpg
