umiahmed30/RuTrash/Data/Valid/trash/trash_new_31.jpg

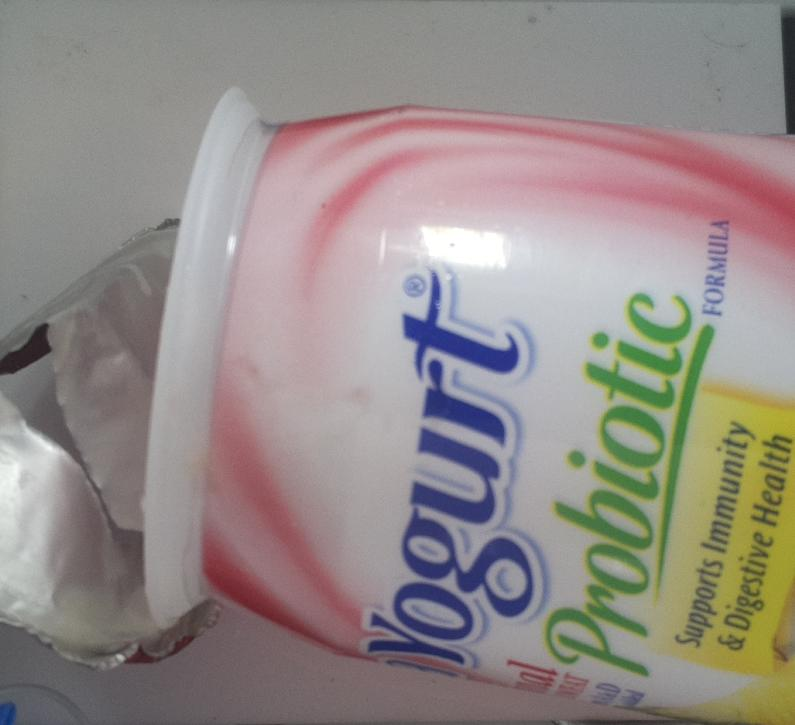
Data/Valid/trash/trash_new_31.jpg
