umiahmed30/RuTrash/Documents/3D Printed Hardware Part Designs/pi camera mount top 3.0.SLDPRT

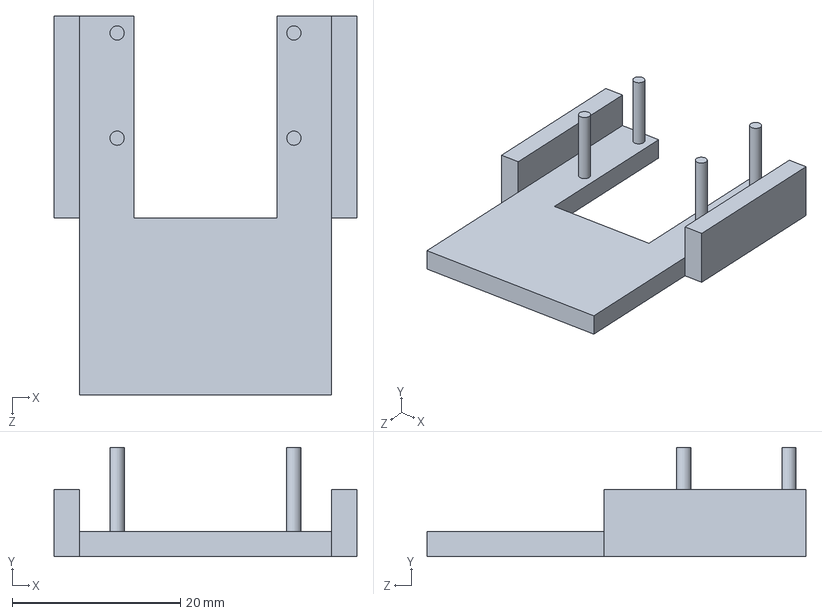
[picture p208: CAD file, 2022-03-16]
Documents/3D Printed Hardware Part Designs/pi camera mount top 3.0.SLDPRT
36.0 x 13.0 x 45.0 mm
