umiahmed30/RuTrash/Documents/3D Printed Hardware Part Designs/divider.SLDPRT

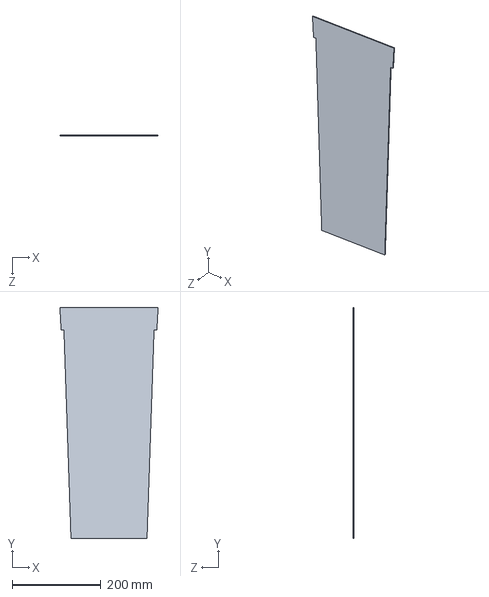
[picture p210: CAD file, 2022-03-16]
Documents/3D Printed Hardware Part Designs/divider.SLDPRT
221.5 x 520.7 x 2.03 mm
