umiahmed30/RuTrash/Documents/3D Printed Hardware Part Designs/Acrylic Carrier/capstone wall width.SLDPRT

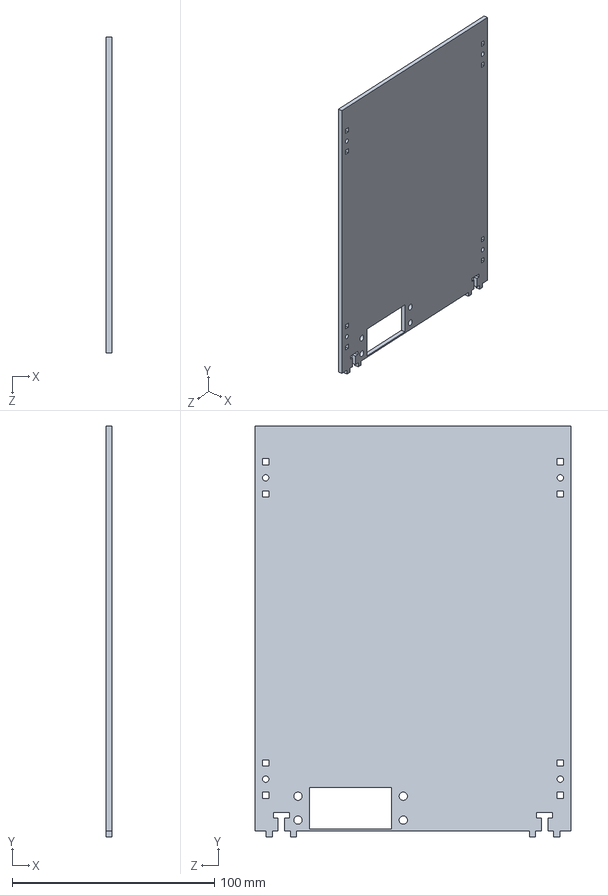
[picture p211: CAD file, 2022-03-16]
Documents/3D Printed Hardware Part Designs/Acrylic Carrier/capstone wall width.SLDPRT
3.00 x 203.0 x 156.0 mm
