umiahmed30/RuTrash/Documents/3D Printed Hardware Part Designs/rod bearing.SLDPRT

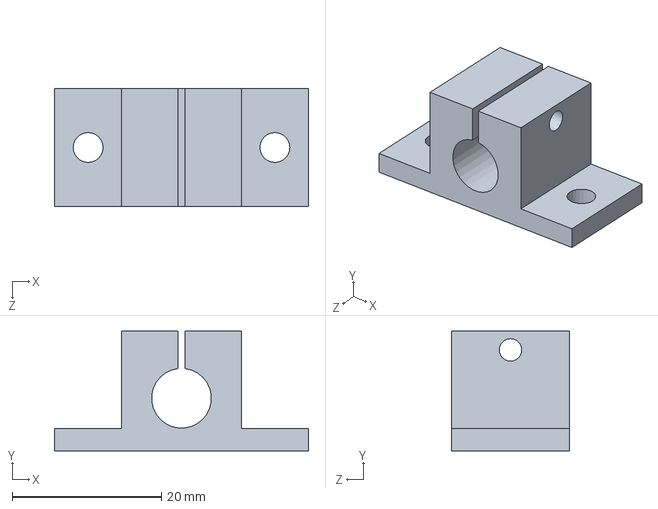
[picture p212: CAD file, 2022-03-16]
Documents/3D Printed Hardware Part Designs/rod bearing.SLDPRT
34.0 x 16.0 x 15.8 mm
