umiahmed30/RuTrash/Documents/3D Printed Hardware Part Designs/pi camer mount bottom 3.0.SLDPRT

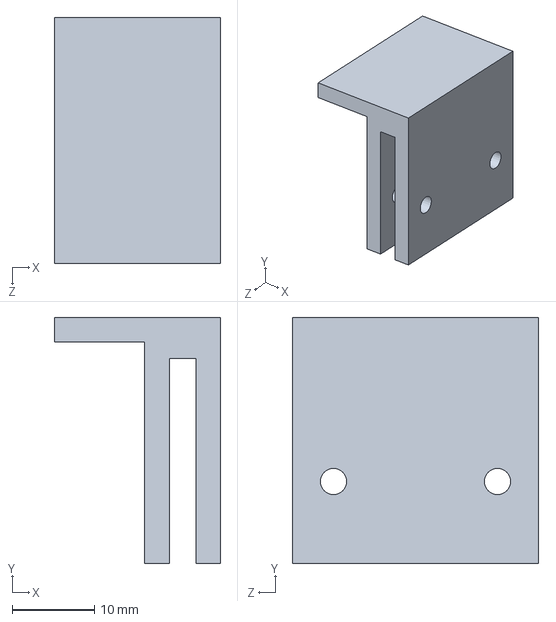
[picture p214: CAD file, 2022-03-16]
Documents/3D Printed Hardware Part Designs/pi camer mount bottom 3.0.SLDPRT
20.2 x 30.0 x 30.0 mm
