umiahmed30/RuTrash/Documents/3D Printed Hardware Part Designs/Acrylic Carrier/capstone wall length.SLDPRT

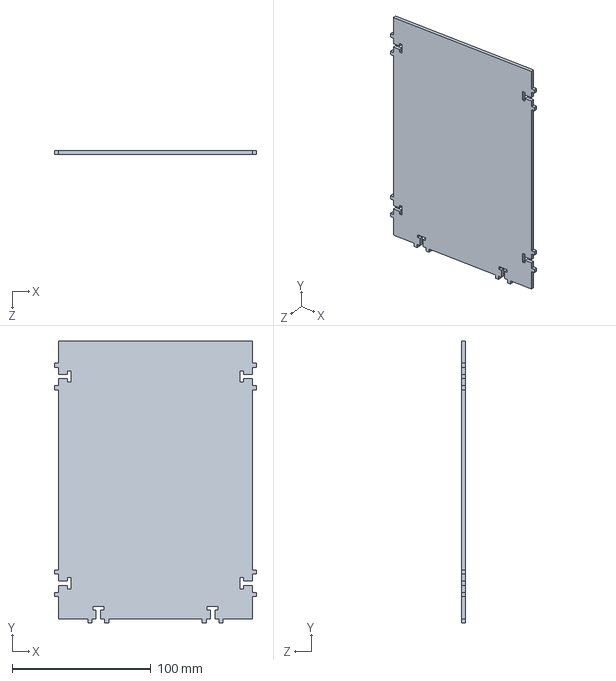
[picture p215: CAD file, 2022-03-16]
Documents/3D Printed Hardware Part Designs/Acrylic Carrier/capstone wall length.SLDPRT
145.6 x 203.0 x 3.00 mm
