umiahmed30/RuTrash/Documents/3D Printed Hardware Part Designs/Y-Belt-Holder-Thin-GT2_A6Ext3_V2_PP.stl

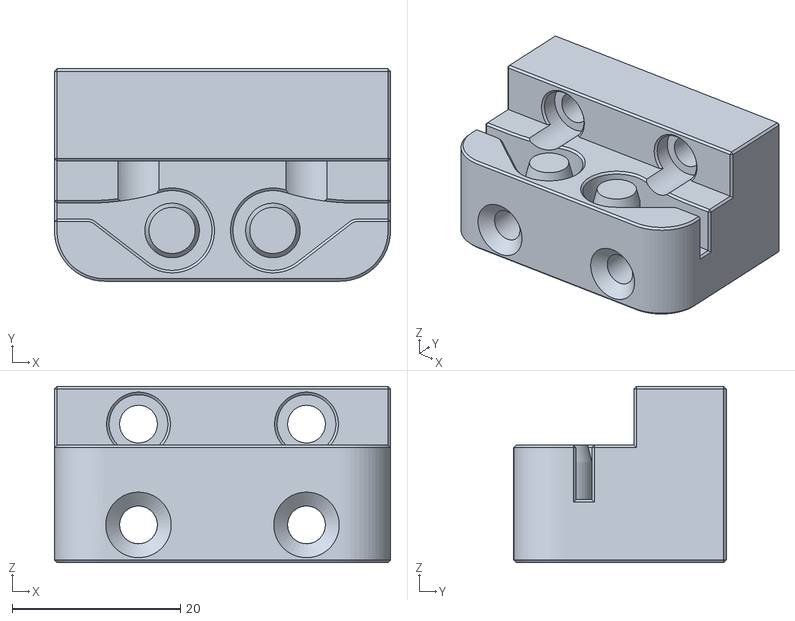
[picture p216: CAD file, 2022-03-16]
Documents/3D Printed Hardware Part Designs/Y-Belt-Holder-Thin-GT2_A6Ext3_V2_PP.stl
40.0 x 25.3 x 21.0
