umiahmed30/RuTrash/Documents/3D Printed Hardware Part Designs/Acrylic Carrier/capstone wall width 3.0.DXF

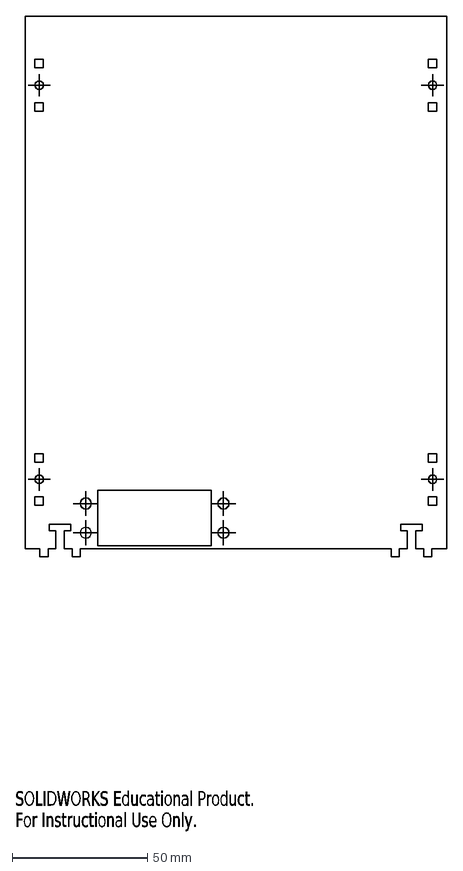
[picture p217: CAD file, 2022-03-16]
Documents/3D Printed Hardware Part Designs/Acrylic Carrier/capstone wall width 3.0.DXF
SOLIDWORKS Educational Product.
For Instructional Use Only.
