umiahmed30/RuTrash/Documents/3D Printed Hardware Part Designs/possible stepper motor mount.SLDPRT

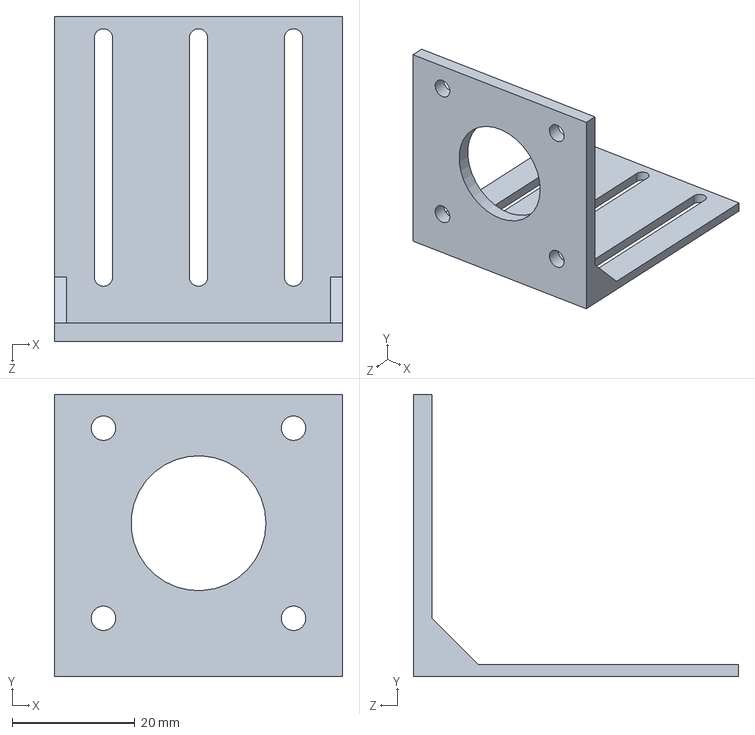
[picture p218: CAD file, 2022-03-16]
Documents/3D Printed Hardware Part Designs/possible stepper motor mount.SLDPRT
47.0 x 46.0 x 53.0 mm
