umiahmed30/RuTrash/Documents/3D Printed Hardware Part Designs/Acrylic Carrier/sketch 3.5  i think.DXF

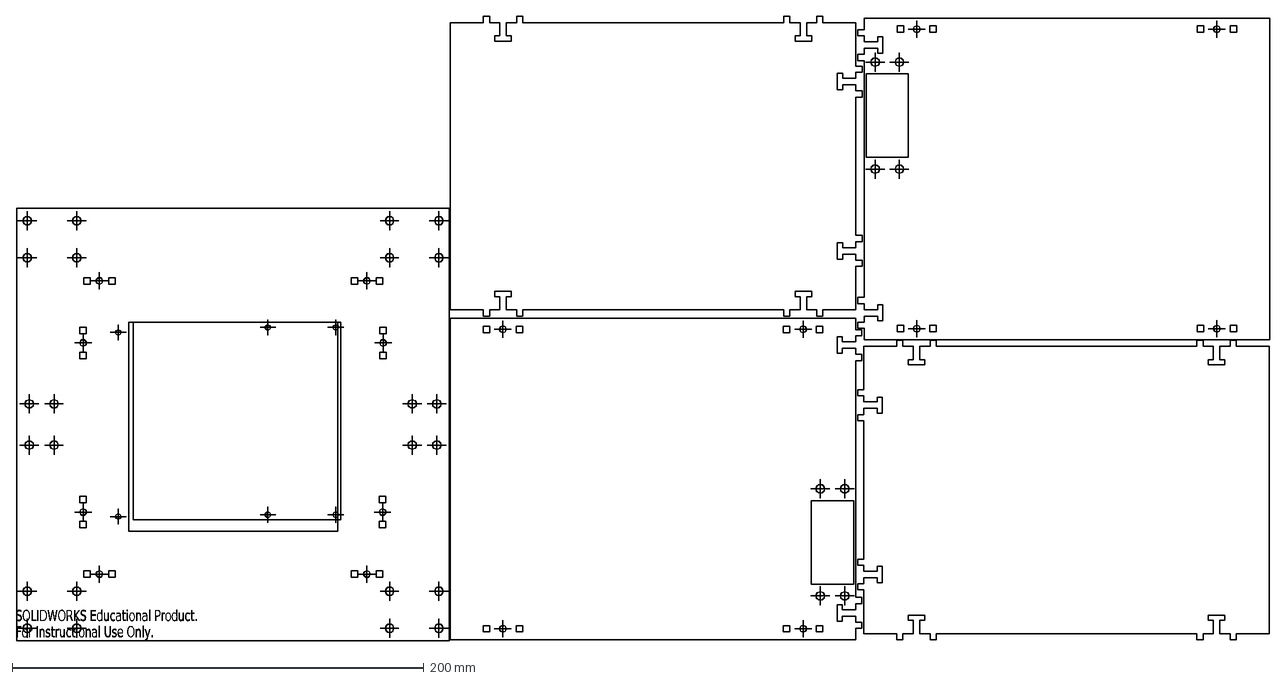
[picture p219: CAD file, 2022-03-16]
Documents/3D Printed Hardware Part Designs/Acrylic Carrier/sketch 3.5 i think.DXF
SOLIDWORKS Educational Product.
For Instructional Use Only.
