umiahmed30/RuTrash/Documents/3D Printed Hardware Part Designs/garbage pale 2.0.SLDPRT

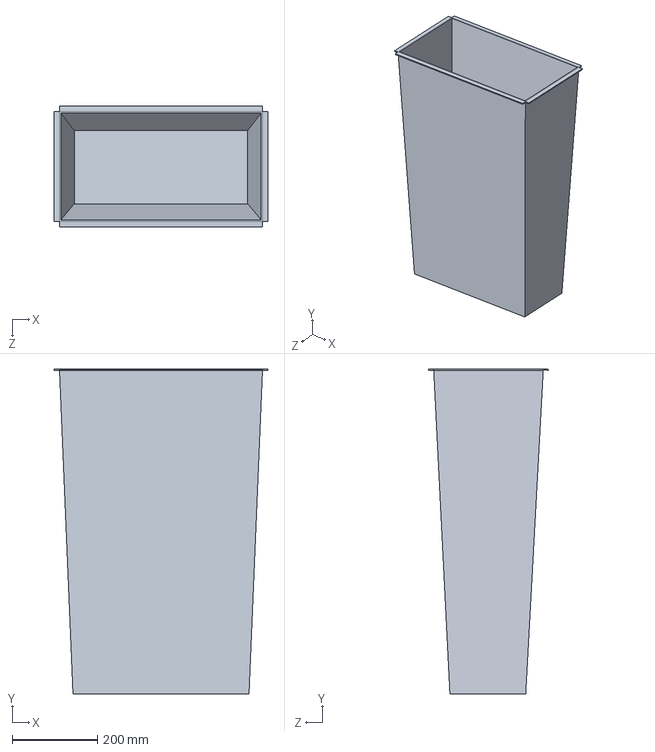
[picture p220: CAD file, 2022-03-16]
Documents/3D Printed Hardware Part Designs/garbage pale 2.0.SLDPRT
501.6 x 762.0 x 282.5 mm
