umiahmed30/RuTrash/Documents/3D Printed Hardware Part Designs/Acrylic Carrier/cheap servo.SLDPRT

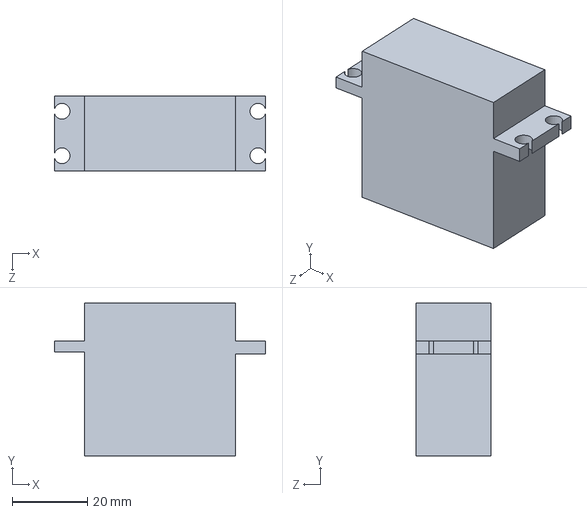
[picture p221: CAD file, 2022-03-16]
Documents/3D Printed Hardware Part Designs/Acrylic Carrier/cheap servo.SLDPRT
56.0 x 40.5 x 20.0 mm
