umiahmed30/RuTrash/Documents/3D Printed Hardware Part Designs/Acrylic Carrier/sketch 5.5  i think.DXF

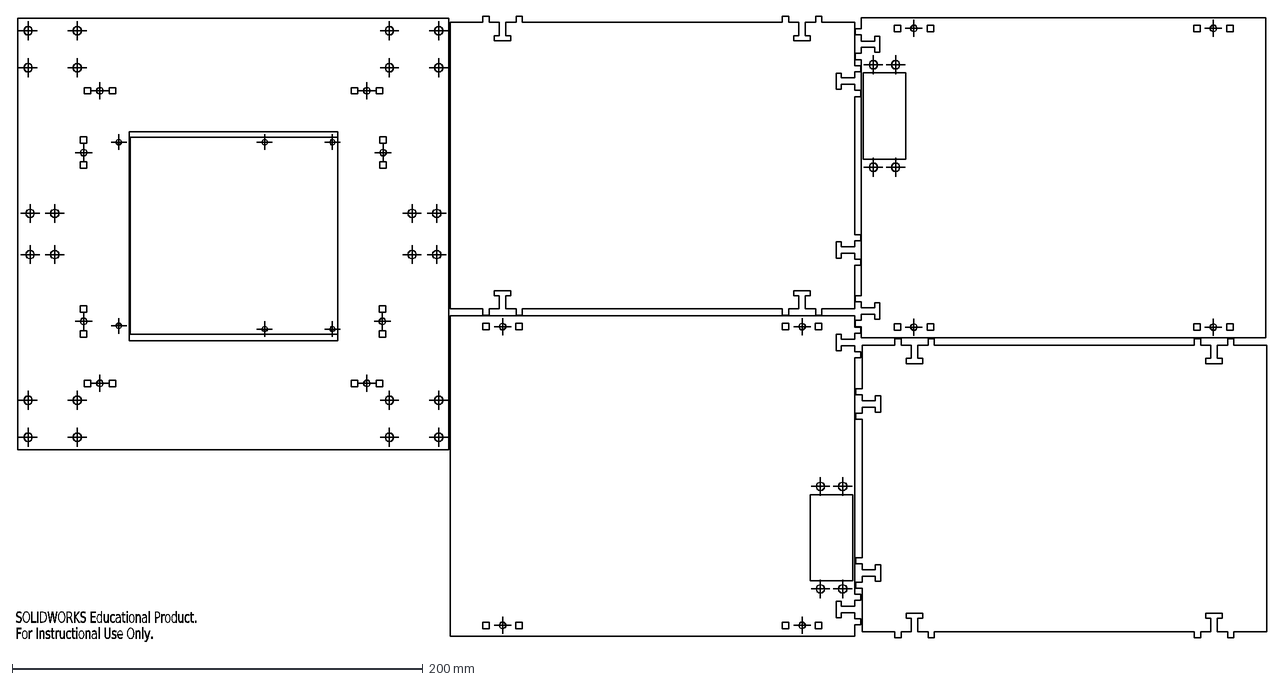
[picture p222: CAD file, 2022-03-16]
Documents/3D Printed Hardware Part Designs/Acrylic Carrier/sketch 5.5 i think.DXF
SOLIDWORKS Educational Product.
For Instructional Use Only.
