umiahmed30/RuTrash/Documents/3D Printed Hardware Part Designs/pi camera mount cover.SLDPRT

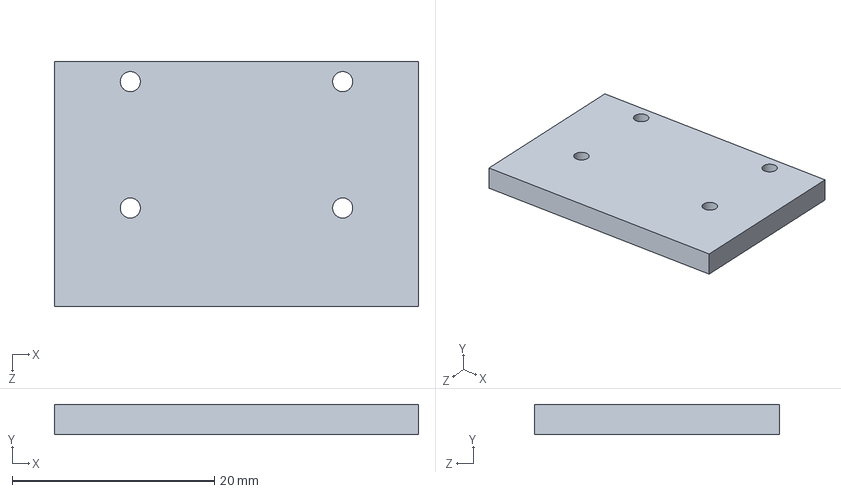
[picture p223: CAD file, 2022-03-16]
Documents/3D Printed Hardware Part Designs/pi camera mount cover.SLDPRT
36.0 x 3.00 x 24.2 mm
