umiahmed30/RuTrash/Documents/3D Printed Hardware Part Designs/servo mount.SLDPRT

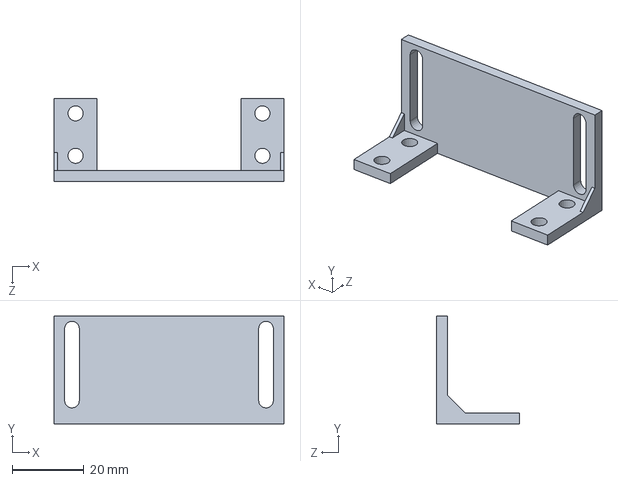
[picture p224: CAD file, 2022-03-16]
Documents/3D Printed Hardware Part Designs/servo mount.SLDPRT
64.0 x 30.0 x 23.0 mm
