umiahmed30/RuTrash/Documents/3D Printed Hardware Part Designs/pi camera mount 2.0.SLDPRT

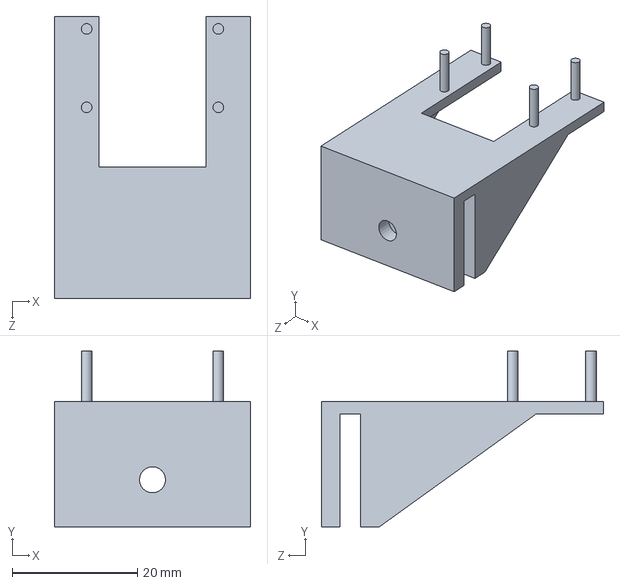
[picture p225: CAD file, 2022-03-16]
Documents/3D Printed Hardware Part Designs/pi camera mount 2.0.SLDPRT
31.2 x 28.0 x 45.0 mm
