umiahmed30/RuTrash/Documents/3D Printed Hardware Part Designs/8 mm bearing.SLDPRT

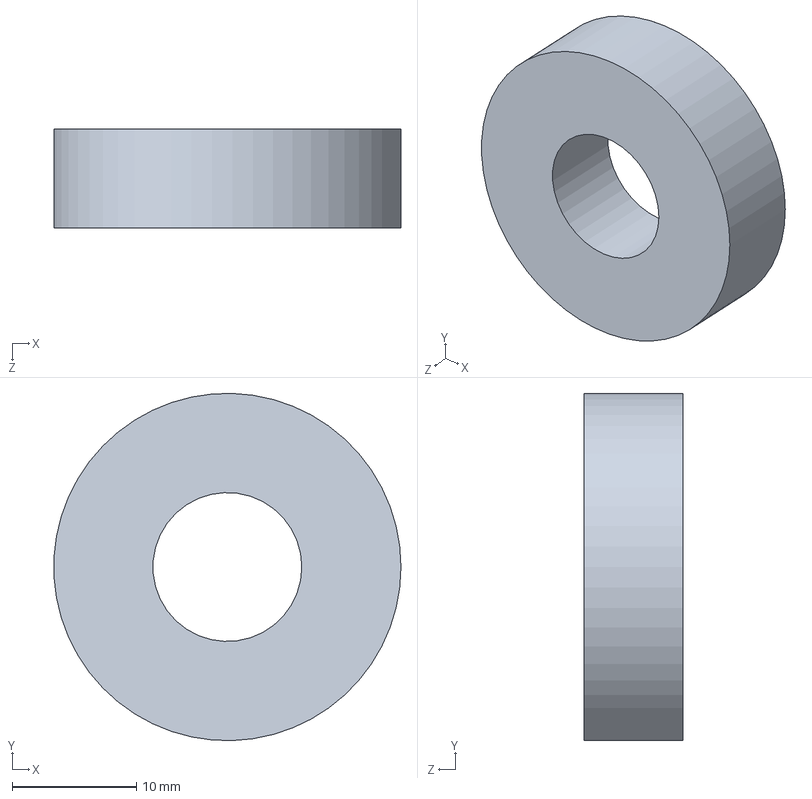
[picture p226: CAD file, 2022-03-16]
Documents/3D Printed Hardware Part Designs/8 mm bearing.SLDPRT
28.0 x 28.0 x 8.00 mm
