umiahmed30/RuTrash/Documents/3D Printed Hardware Part Designs/I  bracket for linear rod.SLDPRT

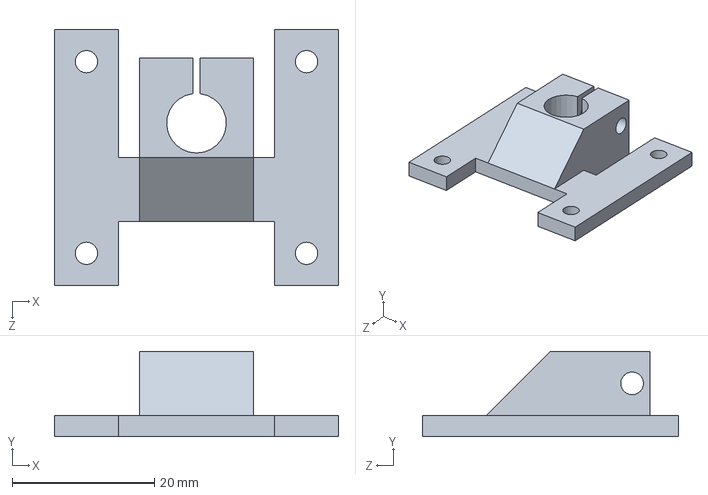
[picture p227: CAD file, 2022-03-16]
Documents/3D Printed Hardware Part Designs/I bracket for linear rod.SLDPRT
40.0 x 12.0 x 36.0 mm
